jotego/jts16/cores/s16/ver/game/wb35/7.png

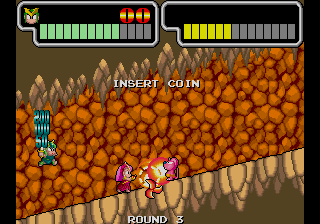
cores/s16/ver/game/wb35/7.png
