jotego/jts16/cores/s16/ver/game/shinobi/1.png

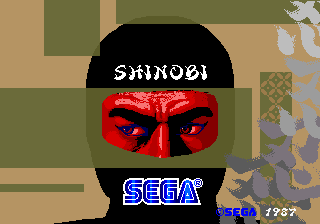
cores/s16/ver/game/shinobi/1.png
