jotego/jts16/cores/s16/ver/game/shinobi/2.png

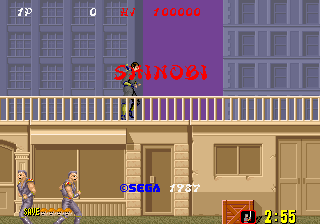
cores/s16/ver/game/shinobi/2.png
