jotego/jts16/cores/s16/ver/game/shinobi/3.png

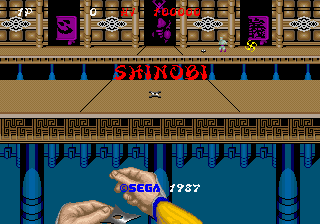
cores/s16/ver/game/shinobi/3.png
