jotego/jts16/cores/s16/ver/game/shinobi/4.png

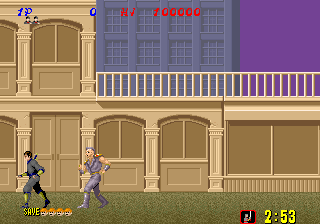
cores/s16/ver/game/shinobi/4.png
