jotego/jts16/cores/s16/ver/game/shinobi/5.png

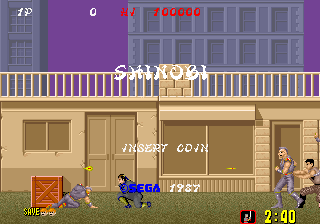
cores/s16/ver/game/shinobi/5.png
