jotego/jts16/cores/s16/ver/game/shinobi/6.png

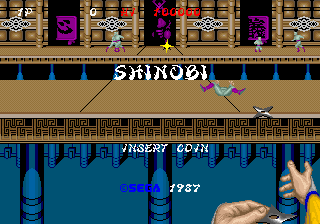
cores/s16/ver/game/shinobi/6.png
