jotego/jts16/cores/s16/ver/game/shinobi/7.png

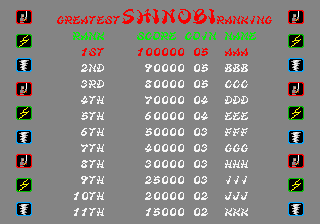
cores/s16/ver/game/shinobi/7.png
