jotego/jts16/cores/s16/ver/game/shinobi/8.png

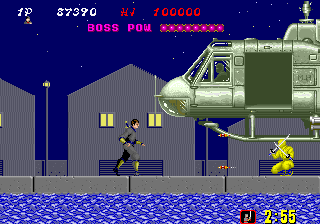
cores/s16/ver/game/shinobi/8.png
