jotego/jts16/cores/s16/ver/game/shinobi/9.png

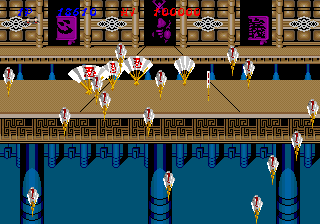
cores/s16/ver/game/shinobi/9.png
