jotego/jts16/cores/s16/ver/game/wb35/2.png

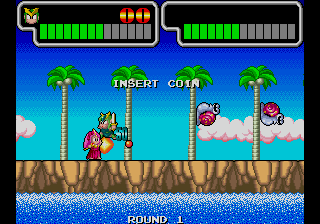
cores/s16/ver/game/wb35/2.png
