jotego/jts16/cores/s16/ver/game/wb35/3.png

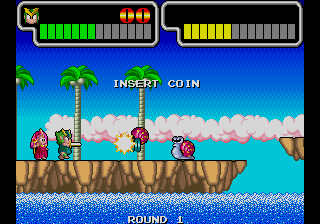
cores/s16/ver/game/wb35/3.png
