jotego/jts16/cores/s16/ver/game/wb35/4.png

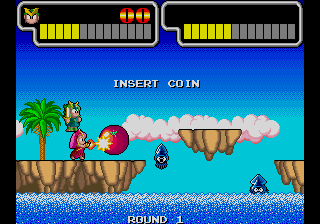
cores/s16/ver/game/wb35/4.png
