jotego/jts16/cores/s16/ver/game/wb35/6.png

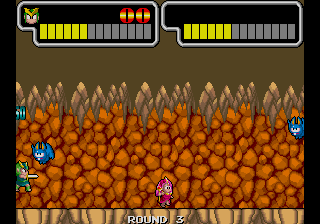
cores/s16/ver/game/wb35/6.png
