jotego/jts16/cores/s16/ver/game/wb35/8.png

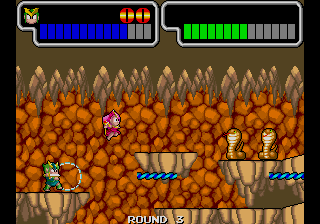
cores/s16/ver/game/wb35/8.png
