jotego/jts16/doc/scope/DTACKn.png

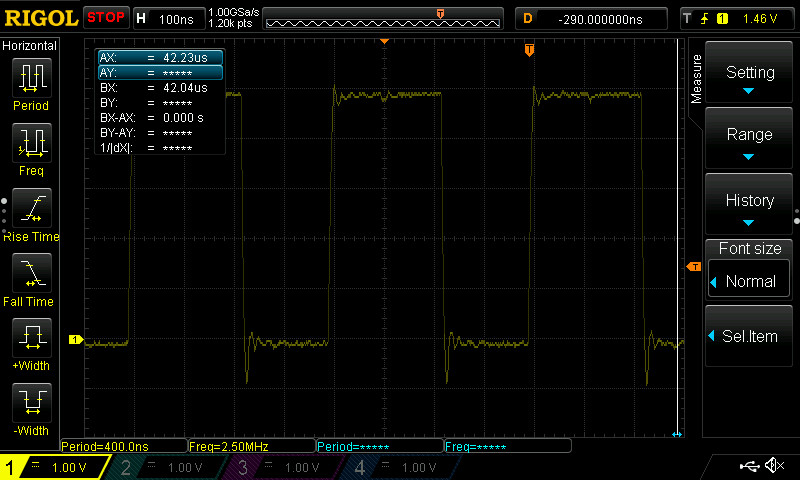
doc/scope/DTACKn.png
