jotego/jts16/doc/scope/IPL2.png

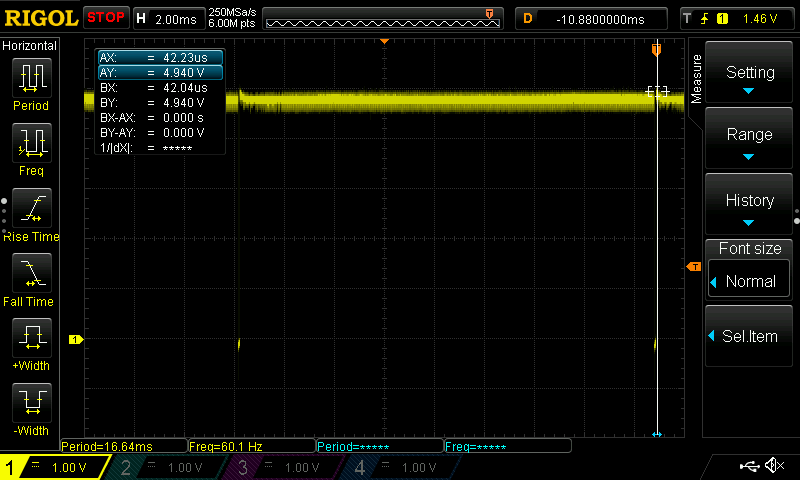
doc/scope/IPL2.png
