jotego/jts16/doc/scope/wb3/wb3.png

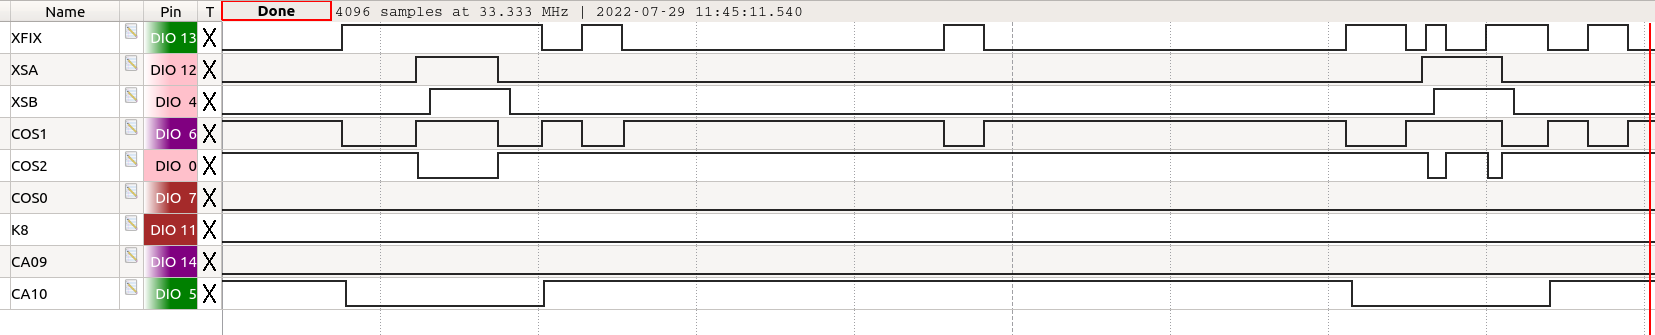
doc/scope/wb3/wb3.png
