jotego/jts16/doc/scope/wb3/WB3_no_OBJ.png

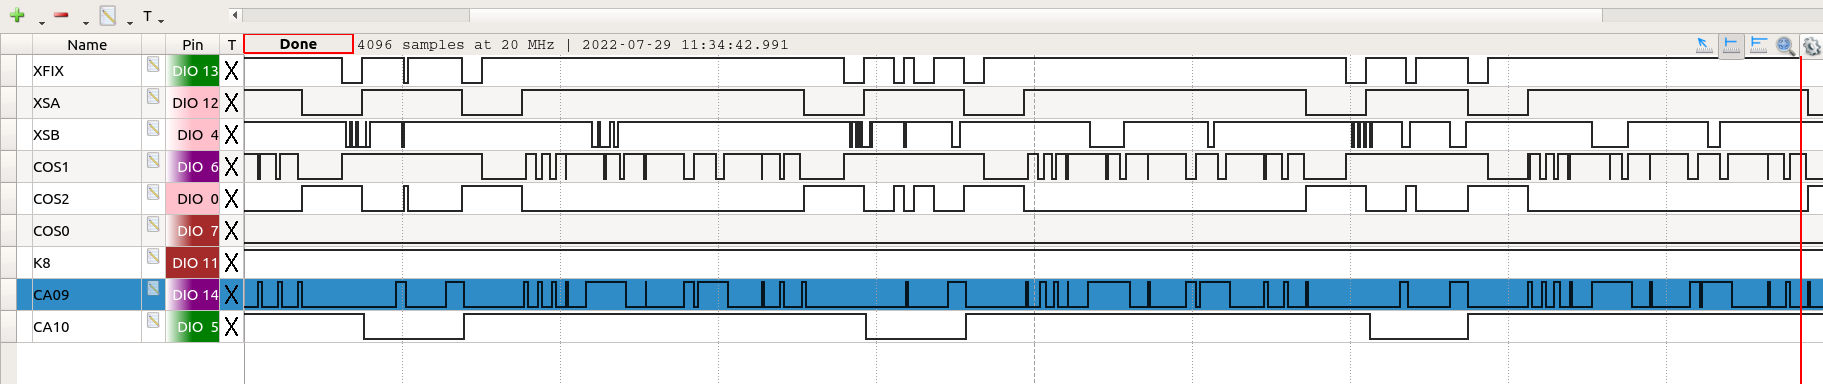
doc/scope/wb3/WB3_no_OBJ.png
