jotego/jts16/doc/scope/wb3/WB3_only_char.png

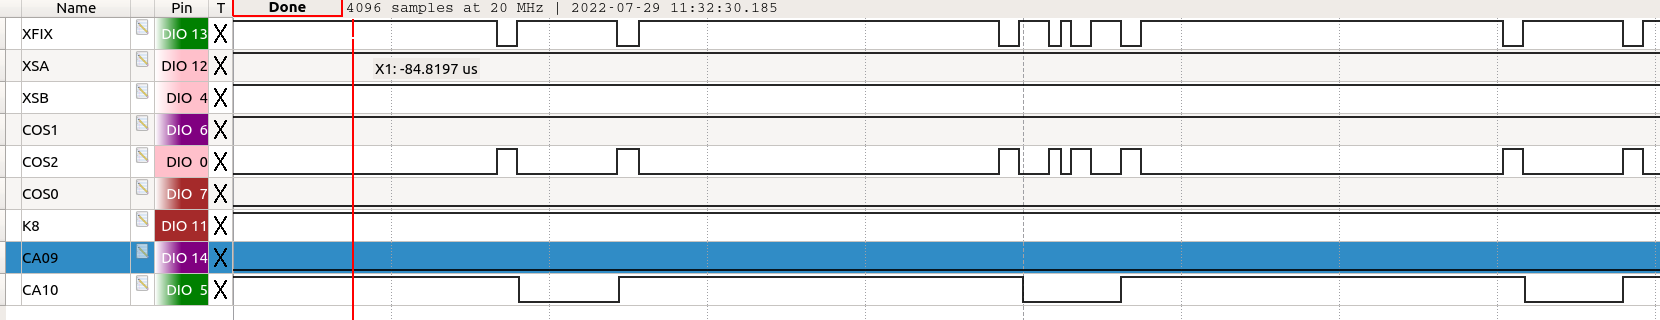
doc/scope/wb3/WB3_only_char.png
