jotego/jts16/doc/scope/Z80 clk.png

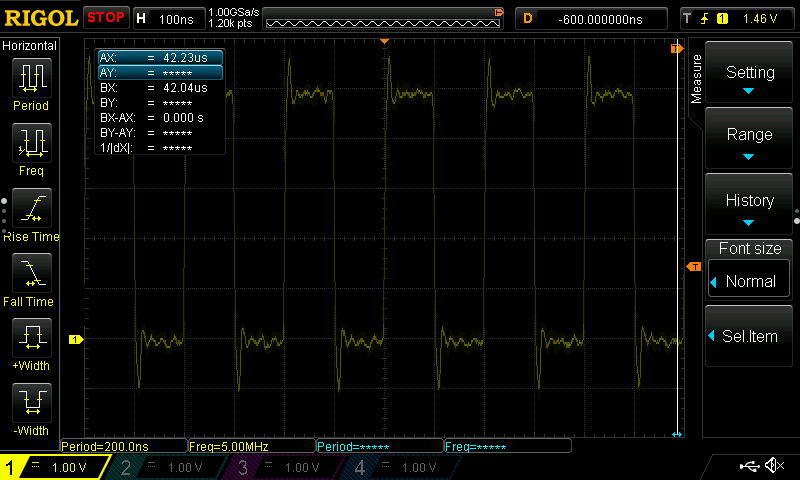
doc/scope/Z80 clk.png
