jotego/jts16/cores/s18/sch/amd.kicad_sch

## KiCad design cores/s18/sch/amd.kicad_sch (2022-12-19)

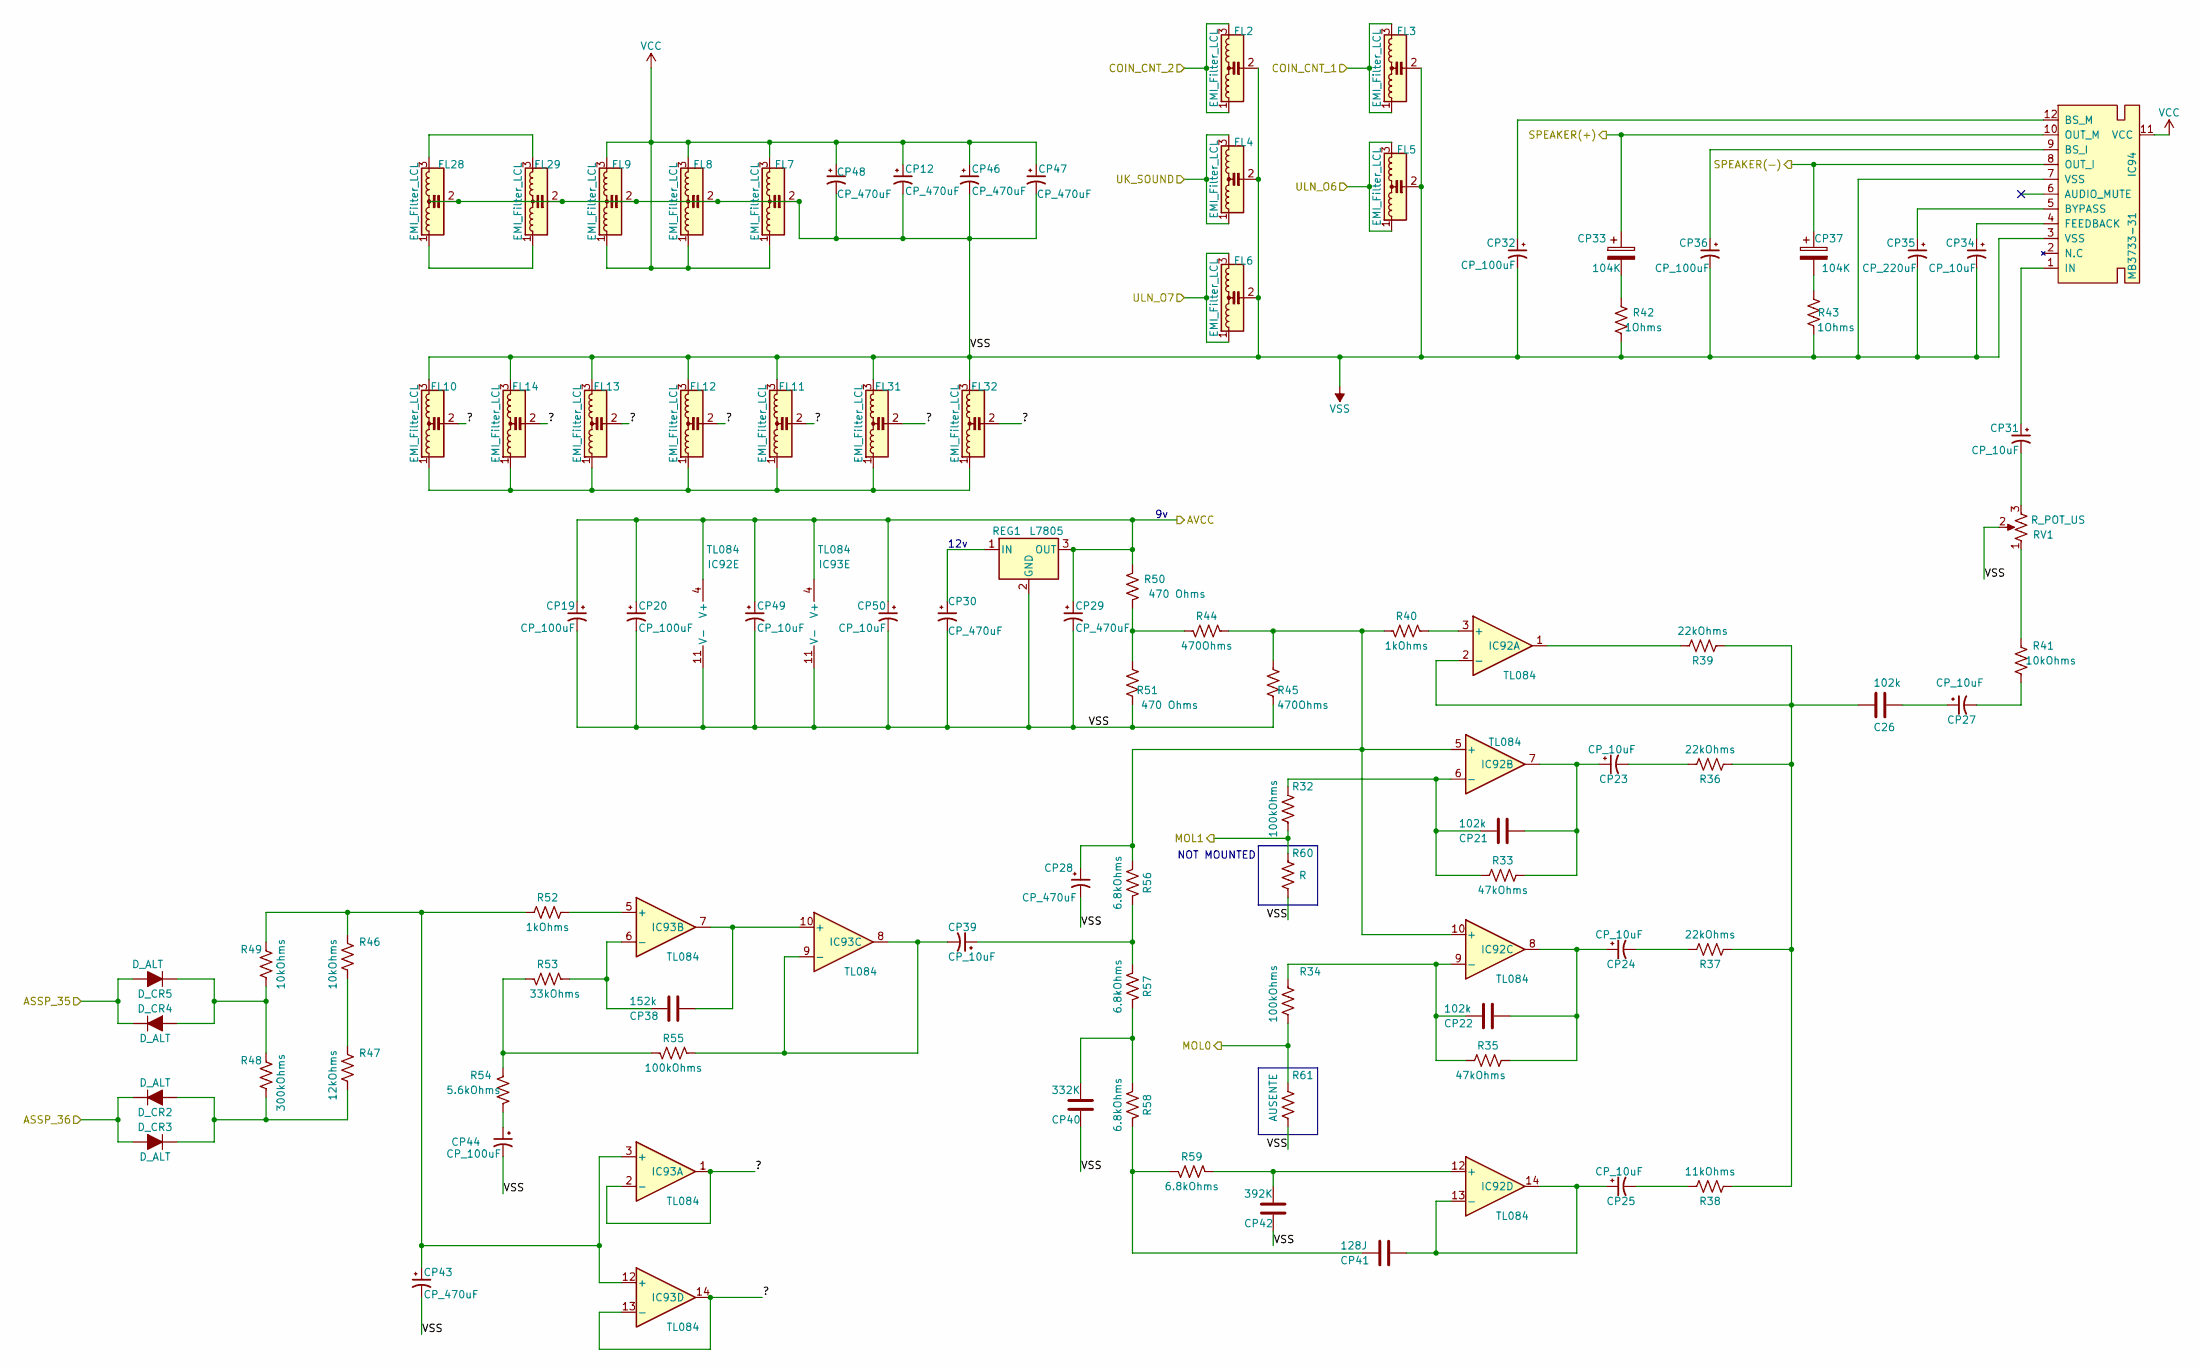
[picture p33: schematic amd.kicad_sch]

Parts:
104K: CP37
C26: 102k
CP12, CP28, CP29, CP30, CP43, CP46, CP47, CP48: CP_470uF
CP19, CP20, CP32, CP36, CP44: CP_100uF
CP21, CP22: 102k
CP23, CP24, CP25, CP27, CP31, CP34, CP39, CP49, CP50: CP_10uF
CP35: CP_220uF
CP38: 152k
CP40: 332K
CP41: 128J
CP42: 392K
D_CR2, D_CR3, D_CR4, D_CR5: D_ALT
FL2, FL3, FL4, FL5, FL6, FL7, FL8, FL9, FL10, FL11, FL12, FL13, FL14, FL28, FL29, FL31, FL32: EMI_Filter_LCL
IC92, IC93: TL084
IC94: MB3733-31
R32, R34, R55: 100kOhms
R33, R35: 47kOhms
R36, R37, R39: 22kOhms
R38: 11kOhms
R40, R52: 1kOhms
R41, R46, R49: 10kOhms
R42, R43: 1Ohms
R44, R45: 470Ohms
R47: 12kOhms
R48: 300kOhms
R50, R51: 470 Ohms
R53: 33kOhms
R54: 5.6kOhms
R56, R57, R58, R59: 6.8kOhms
R60: R
R61: AUSENTE
REG1: L7805
RV1: R_POT_US

Connections:
?: FL10.2, FL11.2, FL12.2, FL13.2, FL14.2, FL31.2, FL32.2, IC93.1, IC93.2 (-), IC93.13 (-), IC93.14
ASSP_35: D_CR4.1 (K), D_CR5.2 (A)
ASSP_36: D_CR2.1 (K), D_CR3.2 (A)
AVCC: CP19.1, CP20.1, CP29.1, CP49.1, CP50.1, IC92.4 (V+), IC93.4 (V+), R50.1, REG1.3 (OUT)
COIN_CNT_1: FL3.1, FL3.3
COIN_CNT_2: FL2.1, FL2.3
MOL0: R34.2, R61.1
MOL1: R32.2, R60.1
unnamed: 104K.2, R42.1, R43.1
unnamed: C26.1, CP27.1
unnamed: C26.2, IC92.2 (-), R36.2, R37.2, R38.2, R39.2
unnamed: CP12.1, CP46.1, CP47.1, CP48.1, FL7.1, FL7.3, FL8.1, FL8.3, FL9.1, FL9.3
unnamed: CP21.1, CP23.1, IC92.7, R33.1
unnamed: CP21.2, IC92.6 (-), R32.1, R33.2
unnamed: CP22.1, CP24.1, IC92.8, R35.1
unnamed: CP22.2, IC92.9 (-), R34.1, R35.2
unnamed: CP23.2, R36.1
unnamed: CP24.2, R37.1
unnamed: CP25.1, CP41.1, IC92.13 (-), IC92.14
unnamed: CP25.2, R38.1
unnamed: CP27.2, R41.1
unnamed: CP28.1, IC92.5 (+), IC92.10 (+), R40.1, R44.1, R45.1, R56.2
unnamed: CP30.1, REG1.1 (IN)
unnamed: CP31.1, IC94.1 (IN)
unnamed: CP31.2, RV1.3
unnamed: CP32.1, IC94.12 (BS_M)
unnamed: CP34.1, IC94.4 (FEEDBACK)
unnamed: CP35.1, IC94.5 (BYPASS)
unnamed: CP36.1, IC94.9 (BS_I)
unnamed: CP38.1, IC93.7, IC93.10 (+)
unnamed: CP38.2, IC93.6 (-), R53.1
unnamed: CP39.1, R56.1, R57.2
unnamed: CP39.2, IC93.8, IC93.9 (-), R55.1
unnamed: CP40.1, R57.1, R58.2
unnamed: CP41.2, R58.1, R59.1
unnamed: CP42.1, IC92.12 (+), R59.2
unnamed: CP43.1, IC93.3 (+), IC93.12 (+), R46.2, R49.1, R52.2
unnamed: CP44.1, R54.2
unnamed: D_CR2.2 (A), D_CR3.1 (K), R47.2, R48.1
unnamed: D_CR4.2 (A), D_CR5.1 (K), R48.2, R49.2
unnamed: FL10.1, FL11.1, FL12.1, FL13.1, FL14.1, FL31.1, FL32.1
unnamed: FL28.1, FL29.1
unnamed: FL28.3, FL29.3
unnamed: IC92.1, R39.1
unnamed: IC92.3 (+), R40.2
unnamed: IC93.5 (+), R52.1
unnamed: R41.2, RV1.1
unnamed: R44.2, R50.2, R51.2
unnamed: R46.1, R47.1
unnamed: R53.2, R54.1, R55.2
SPEAKER(+): 104K.1, IC94.10 (OUT_M)
SPEAKER(-): 104K.1, IC94.8 (OUT_I)
UK_SOUND: FL4.1, FL4.3
ULN_O6: FL5.1, FL5.3
ULN_O7: FL6.1, FL6.3
VSS: CP12.2, CP19.2, CP20.2, CP28.2, CP29.2, CP30.2, CP32.2, CP34.2, CP35.2, CP36.2, CP40.2, CP42.2, CP43.2, CP44.2, CP46.2, CP47.2, CP48.2, CP49.2, CP50.2, FL2.2, FL3.2, FL4.2, FL5.2, FL6.2, FL7.2, FL8.2, FL9.2, FL10.3, FL11.3, FL12.3, FL13.3, FL14.3, FL28.2, FL29.2, FL31.3, FL32.3, IC92.11 (V-), IC93.11 (V-), IC94.3 (VSS), IC94.7 (VSS), R42.2, R43.2, R45.2, R51.1, R60.2, R61.2, REG1.2 (GND), RV1.2

Notes on the sheet:
NOT MOUNTED
12v
