jotego/jts16/cores/s18/sch/blanking.kicad_sch

## KiCad design cores/s18/sch/blanking.kicad_sch (2022-12-19)

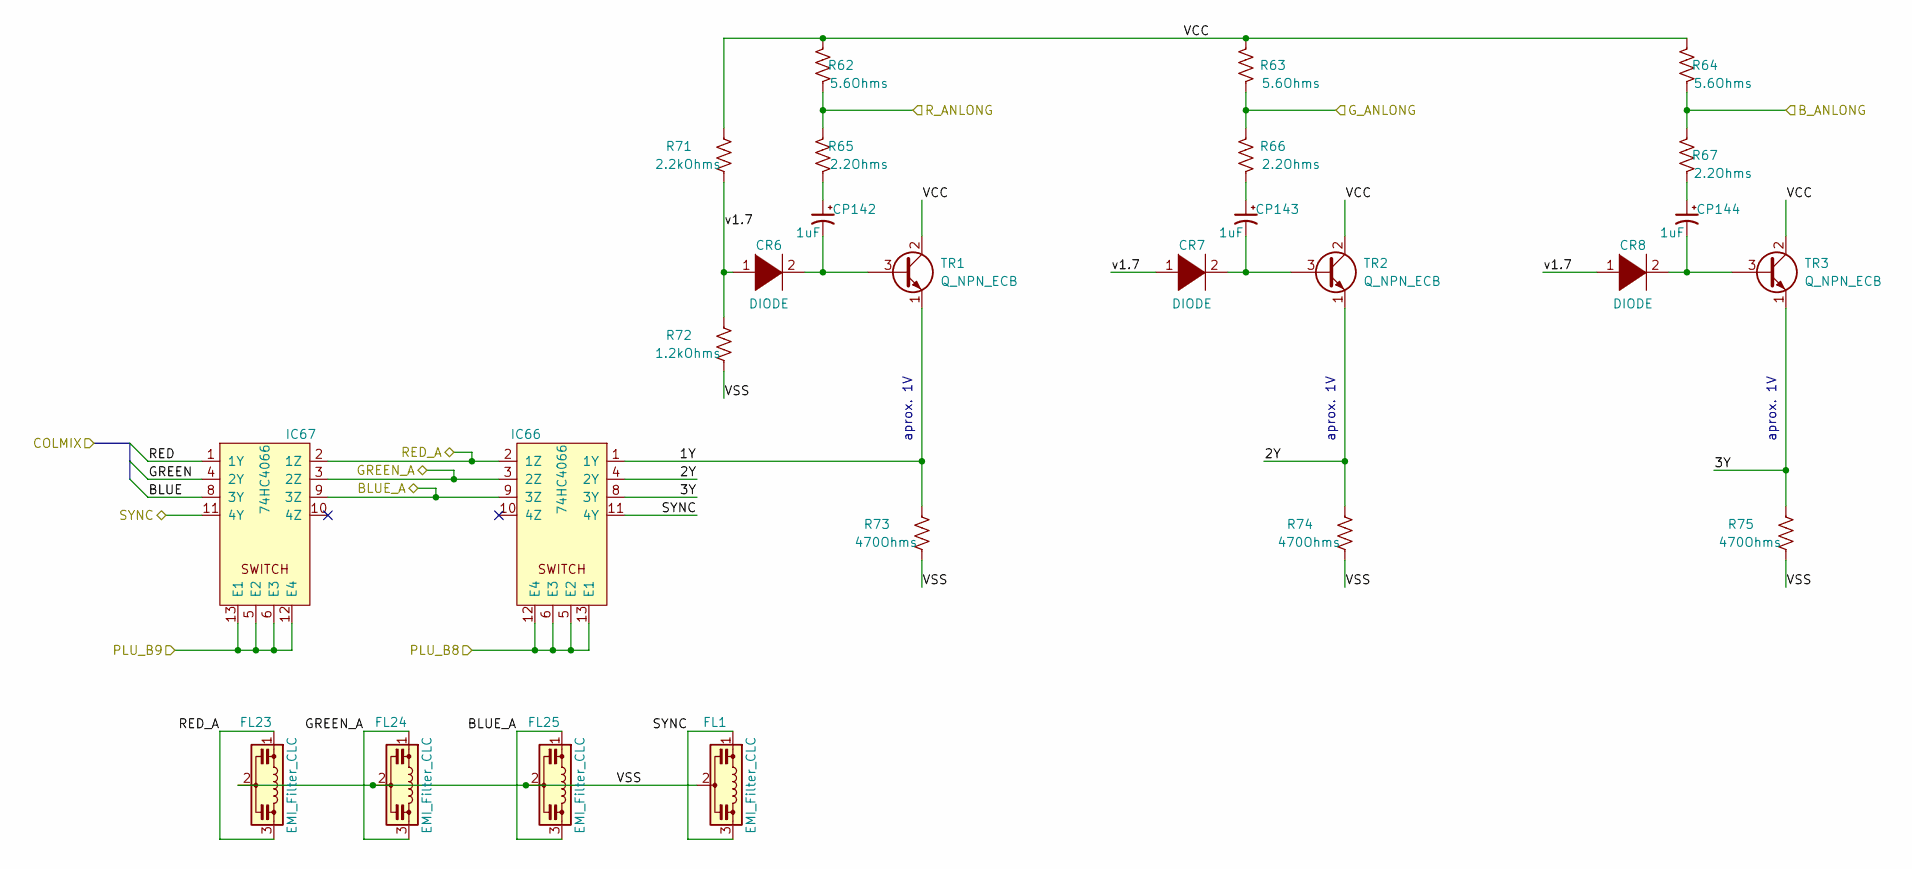
[picture p34: schematic blanking.kicad_sch]

Parts:
CP142, CP143, CP144: 1uF
CR6, CR7, CR8: DIODE
FL1, FL23, FL24, FL25: EMI_Filter_CLC
IC66, IC67: 74HC4066
R62, R63, R64: 5.6Ohms
R65, R66, R67: 2.2Ohms
R71: 2.2kOhms
R72: 1.2kOhms
R73, R74, R75: 470Ohms
TR1, TR2, TR3: Q_NPN_ECB

Connections:
1Y: IC66.1 (1Y), R73.1, TR1.1 (E)
2Y: IC66.4 (2Y), R74.1, TR2.1 (E)
3Y: IC66.8 (3Y), R75.1, TR3.1 (E)
BLUE: IC67.8 (3Y)
BLUE_A: FL25.1, FL25.3, IC66.9 (3Z), IC67.9 (3Z)
B_ANLONG: R64.1, R67.2
GREEN: IC67.4 (2Y)
GREEN_A: FL24.1, FL24.3, IC66.3 (2Z), IC67.3 (2Z)
G_ANLONG: R63.1, R66.2
unnamed: CP142.1, R65.1
unnamed: CP142.2, CR6.2 (A), TR1.3 (B)
unnamed: CP143.1, R66.1
unnamed: CP143.2, CR7.2 (A), TR2.3 (B)
unnamed: CP144.1, R67.1
unnamed: CP144.2, CR8.2 (A), TR3.3 (B)
PLU_B8: IC66.5 (E2), IC66.6 (E3), IC66.12 (E4), IC66.13 (E1)
PLU_B9: IC67.5 (E2), IC67.6 (E3), IC67.12 (E4), IC67.13 (E1)
RED: IC67.1 (1Y)
RED_A: FL23.1, FL23.3, IC66.2 (1Z), IC67.2 (1Z)
R_ANLONG: R62.1, R65.2
SYNC: FL1.1, FL1.3, IC66.11 (4Y), IC67.11 (4Y)
VCC: R62.2, R63.2, R64.2, R71.1, TR1.2 (C), TR2.2 (C), TR3.2 (C)
VSS: FL1.2, FL23.2, FL24.2, FL25.2, R72.2, R73.2, R74.2, R75.2
v1.7: CR6.1 (K), CR7.1 (K), CR8.1 (K), R71.2, R72.1

Notes on the sheet:
aprox. 1V
