jotego/jts16/cores/s18/sch/capacitors.kicad_sch

## KiCad design cores/s18/sch/capacitors.kicad_sch (2022-12-19)

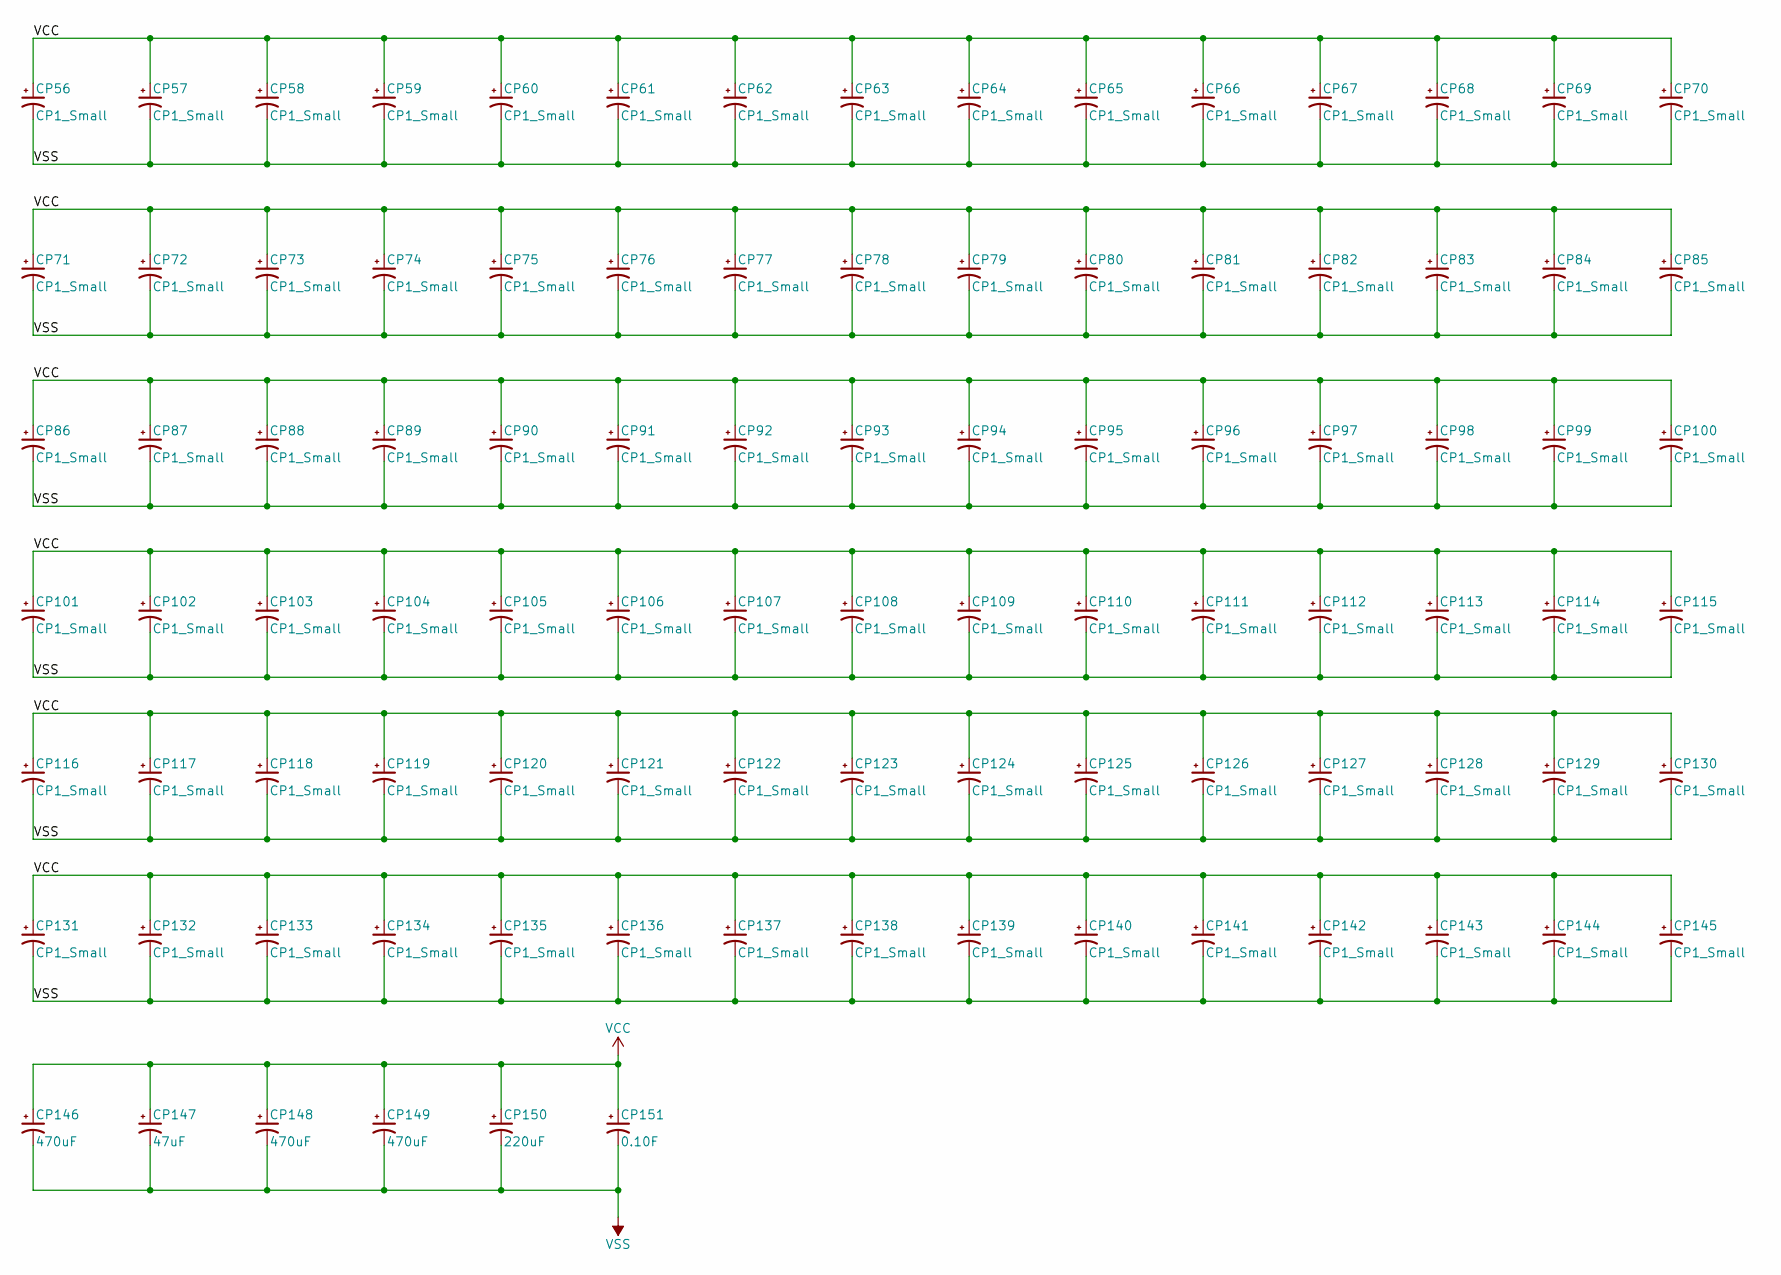
[picture p35: schematic capacitors.kicad_sch]

Parts:
CP56, CP57, CP58, CP59, CP60, CP61, CP62, CP63, CP64, CP65, CP66, CP67, CP68, CP69, CP70, CP71, CP72, CP73, CP74, CP75, CP76, CP77, CP78, CP79, CP80, CP81, CP82, CP83, CP84, CP85, CP86, CP87, CP88, CP89, CP90, CP91, CP92, CP93, CP94, CP95, CP96, CP97, CP98, CP99, CP100, CP101, CP102, CP103, CP104, CP105, CP106, CP107, CP108, CP109, CP110, CP111, CP112, CP113, CP114, CP115, CP116, CP117, CP118, CP119, CP120, CP121, CP122, CP123, CP124, CP125, CP126, CP127, CP128, CP129, CP130, CP131, CP132, CP133, CP134, CP135, CP136, CP137, CP138, CP139, CP140, CP141, CP142, CP143, CP144, CP145: CP1_Small
CP146, CP148, CP149: 470uF
CP147: 47uF
CP150: 220uF
CP151: 0.10F

Connections:
VCC: CP56.1, CP57.1, CP58.1, CP59.1, CP60.1, CP61.1, CP62.1, CP63.1, CP64.1, CP65.1, CP66.1, CP67.1, CP68.1, CP69.1, CP70.1, CP71.1, CP72.1, CP73.1, CP74.1, CP75.1, CP76.1, CP77.1, CP78.1, CP79.1, CP80.1, CP81.1, CP82.1, CP83.1, CP84.1, CP85.1, CP86.1, CP87.1, CP88.1, CP89.1, CP90.1, CP91.1, CP92.1, CP93.1, CP94.1, CP95.1, CP96.1, CP97.1, CP98.1, CP99.1, CP100.1, CP101.1, CP102.1, CP103.1, CP104.1, CP105.1, CP106.1, CP107.1, CP108.1, CP109.1, CP110.1, CP111.1, CP112.1, CP113.1, CP114.1, CP115.1, CP116.1, CP117.1, CP118.1, CP119.1, CP120.1, CP121.1, CP122.1, CP123.1, CP124.1, CP125.1, CP126.1, CP127.1, CP128.1, CP129.1, CP130.1, CP131.1, CP132.1, CP133.1, CP134.1, CP135.1, CP136.1, CP137.1, CP138.1, CP139.1, CP140.1, CP141.1, CP142.1, CP143.1, CP144.1, CP145.1, CP146.1, CP147.1, CP148.1, CP149.1, CP150.1, CP151.1
VSS: CP56.2, CP57.2, CP58.2, CP59.2, CP60.2, CP61.2, CP62.2, CP63.2, CP64.2, CP65.2, CP66.2, CP67.2, CP68.2, CP69.2, CP70.2, CP71.2, CP72.2, CP73.2, CP74.2, CP75.2, CP76.2, CP77.2, CP78.2, CP79.2, CP80.2, CP81.2, CP82.2, CP83.2, CP84.2, CP85.2, CP86.2, CP87.2, CP88.2, CP89.2, CP90.2, CP91.2, CP92.2, CP93.2, CP94.2, CP95.2, CP96.2, CP97.2, CP98.2, CP99.2, CP100.2, CP101.2, CP102.2, CP103.2, CP104.2, CP105.2, CP106.2, CP107.2, CP108.2, CP109.2, CP110.2, CP111.2, CP112.2, CP113.2, CP114.2, CP115.2, CP116.2, CP117.2, CP118.2, CP119.2, CP120.2, CP121.2, CP122.2, CP123.2, CP124.2, CP125.2, CP126.2, CP127.2, CP128.2, CP129.2, CP130.2, CP131.2, CP132.2, CP133.2, CP134.2, CP135.2, CP136.2, CP137.2, CP138.2, CP139.2, CP140.2, CP141.2, CP142.2, CP143.2, CP144.2, CP145.2, CP146.2, CP147.2, CP148.2, CP149.2, CP150.2, CP151.2
