jotego/jts16/cores/s18/sch/colmix.kicad_sch

## KiCad design cores/s18/sch/colmix.kicad_sch (2022-12-19)

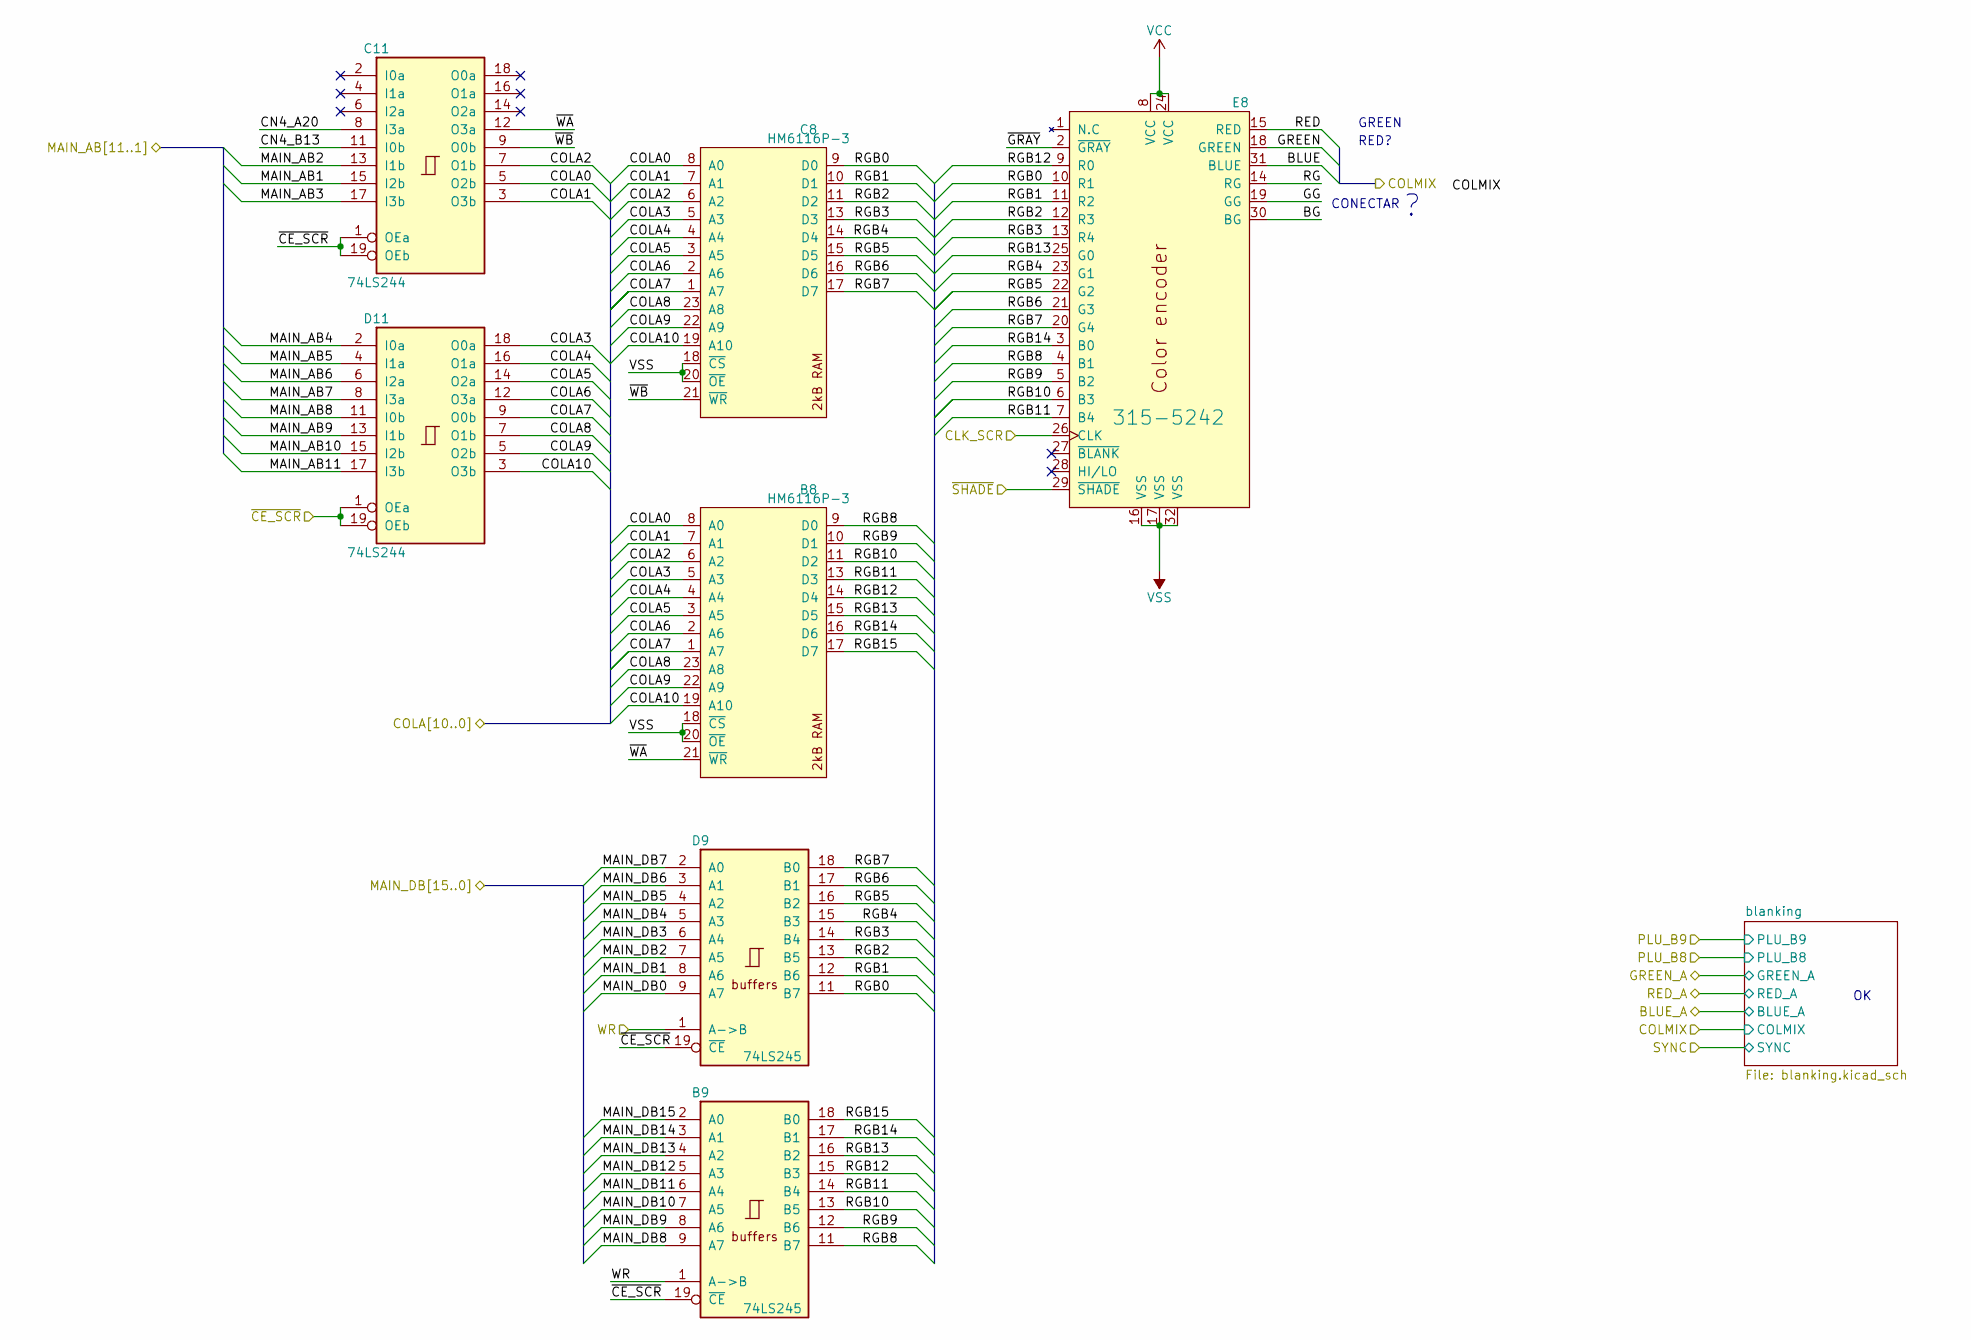
[picture p36: schematic colmix.kicad_sch]

Parts:
B8: HM6116P-3
B9: 74LS245
C8: HM6116P-3
C11: 74LS244
D9: 74LS245
D11: 74LS244
E8: 315-5242

Connections:
BG: E8.30 (BG)
BLUE: E8.31 (BLUE)
CLK_SCR: E8.26 (CLK)
CN4_A20: C11.8 (I3a)
CN4_B13: C11.11 (I0b)
COLA0: B8.8 (A0), C8.8 (A0), C11.5 (O2b)
COLA1: B8.7 (A1), C8.7 (A1), C11.3 (O3b)
COLA2: B8.6 (A2), C8.6 (A2), C11.7 (O1b)
COLA3: B8.5 (A3), C8.5 (A3), D11.18 (O0a)
COLA4: B8.4 (A4), C8.4 (A4), D11.16 (O1a)
COLA5: B8.3 (A5), C8.3 (A5), D11.14 (O2a)
COLA6: B8.2 (A6), C8.2 (A6), D11.12 (O3a)
COLA7: B8.1 (A7), C8.1 (A7), D11.9 (O0b)
COLA8: B8.23 (A8), C8.23 (A8), D11.7 (O1b)
COLA9: B8.22 (A9), C8.22 (A9), D11.5 (O2b)
COLA10: B8.19 (A10), C8.19 (A10), D11.3 (O3b)
GG: E8.19 (GG)
GREEN: E8.18 (GREEN)
MAIN_AB1: C11.15 (I2b)
MAIN_AB2: C11.13 (I1b)
MAIN_AB3: C11.17 (I3b)
MAIN_AB4: D11.2 (I0a)
MAIN_AB5: D11.4 (I1a)
MAIN_AB6: D11.6 (I2a)
MAIN_AB7: D11.8 (I3a)
MAIN_AB8: D11.11 (I0b)
MAIN_AB9: D11.13 (I1b)
MAIN_AB10: D11.15 (I2b)
MAIN_AB11: D11.17 (I3b)
MAIN_DB0: D9.9 (A7)
MAIN_DB1: D9.8 (A6)
MAIN_DB2: D9.7 (A5)
MAIN_DB3: D9.6 (A4)
MAIN_DB4: D9.5 (A3)
MAIN_DB5: D9.4 (A2)
MAIN_DB6: D9.3 (A1)
MAIN_DB7: D9.2 (A0)
MAIN_DB8: B9.9 (A7)
MAIN_DB9: B9.8 (A6)
MAIN_DB10: B9.7 (A5)
MAIN_DB11: B9.6 (A4)
MAIN_DB12: B9.5 (A3)
MAIN_DB13: B9.4 (A2)
MAIN_DB14: B9.3 (A1)
MAIN_DB15: B9.2 (A0)
unnamed: E8.16 (VSS), E8.17 (VSS), E8.32 (VSS)
unnamed: E8.8 (VCC), E8.24 (VCC)
RED: E8.15 (RED)
RG: E8.14 (RG)
RGB0: C8.9 (D0), D9.11 (B7), E8.10 (R1)
RGB1: C8.10 (D1), D9.12 (B6), E8.11 (R2)
RGB2: C8.11 (D2), D9.13 (B5), E8.12 (R3)
RGB3: C8.13 (D3), D9.14 (B4), E8.13 (R4)
RGB4: C8.14 (D4), D9.15 (B3), E8.23 (G1)
RGB5: C8.15 (D5), D9.16 (B2), E8.22 (G2)
RGB6: C8.16 (D6), D9.17 (B1), E8.21 (G3)
RGB7: C8.17 (D7), D9.18 (B0), E8.20 (G4)
RGB8: B8.9 (D0), B9.11 (B7), E8.4 (B1)
RGB9: B8.10 (D1), B9.12 (B6), E8.5 (B2)
RGB10: B8.11 (D2), B9.13 (B5), E8.6 (B3)
RGB11: B8.13 (D3), B9.14 (B4), E8.7 (B4)
RGB12: B8.14 (D4), B9.15 (B3), E8.9 (R0)
RGB13: B8.15 (D5), B9.16 (B2), E8.25 (G0)
RGB14: B8.16 (D6), B9.17 (B1), E8.3 (B0)
RGB15: B8.17 (D7), B9.18 (B0)
VSS: B8.18 (~CS), B8.20 (~OE), C8.18 (~CS), C8.20 (~OE)
WR: B9.1 (A->B), D9.1 (A->B)
~CE_SCR: B9.19 (~CE), C11.1 (OEa), C11.19 (OEb), D9.19 (~CE), D11.1 (OEa), D11.19 (OEb)
~GRAY: E8.2 (~GRAY)
~SHADE: E8.29 (~SHADE)
~WA: B8.21 (~WR), C11.12 (O3a)
~WB: C8.21 (~WR), C11.9 (O0b)

Notes on the sheet:
GREEN
RED?
CONECTAR
