jotego/jts16/cores/s18/sch/cpurom.kicad_sch

## KiCad design cores/s18/sch/cpurom.kicad_sch (2022-12-19)

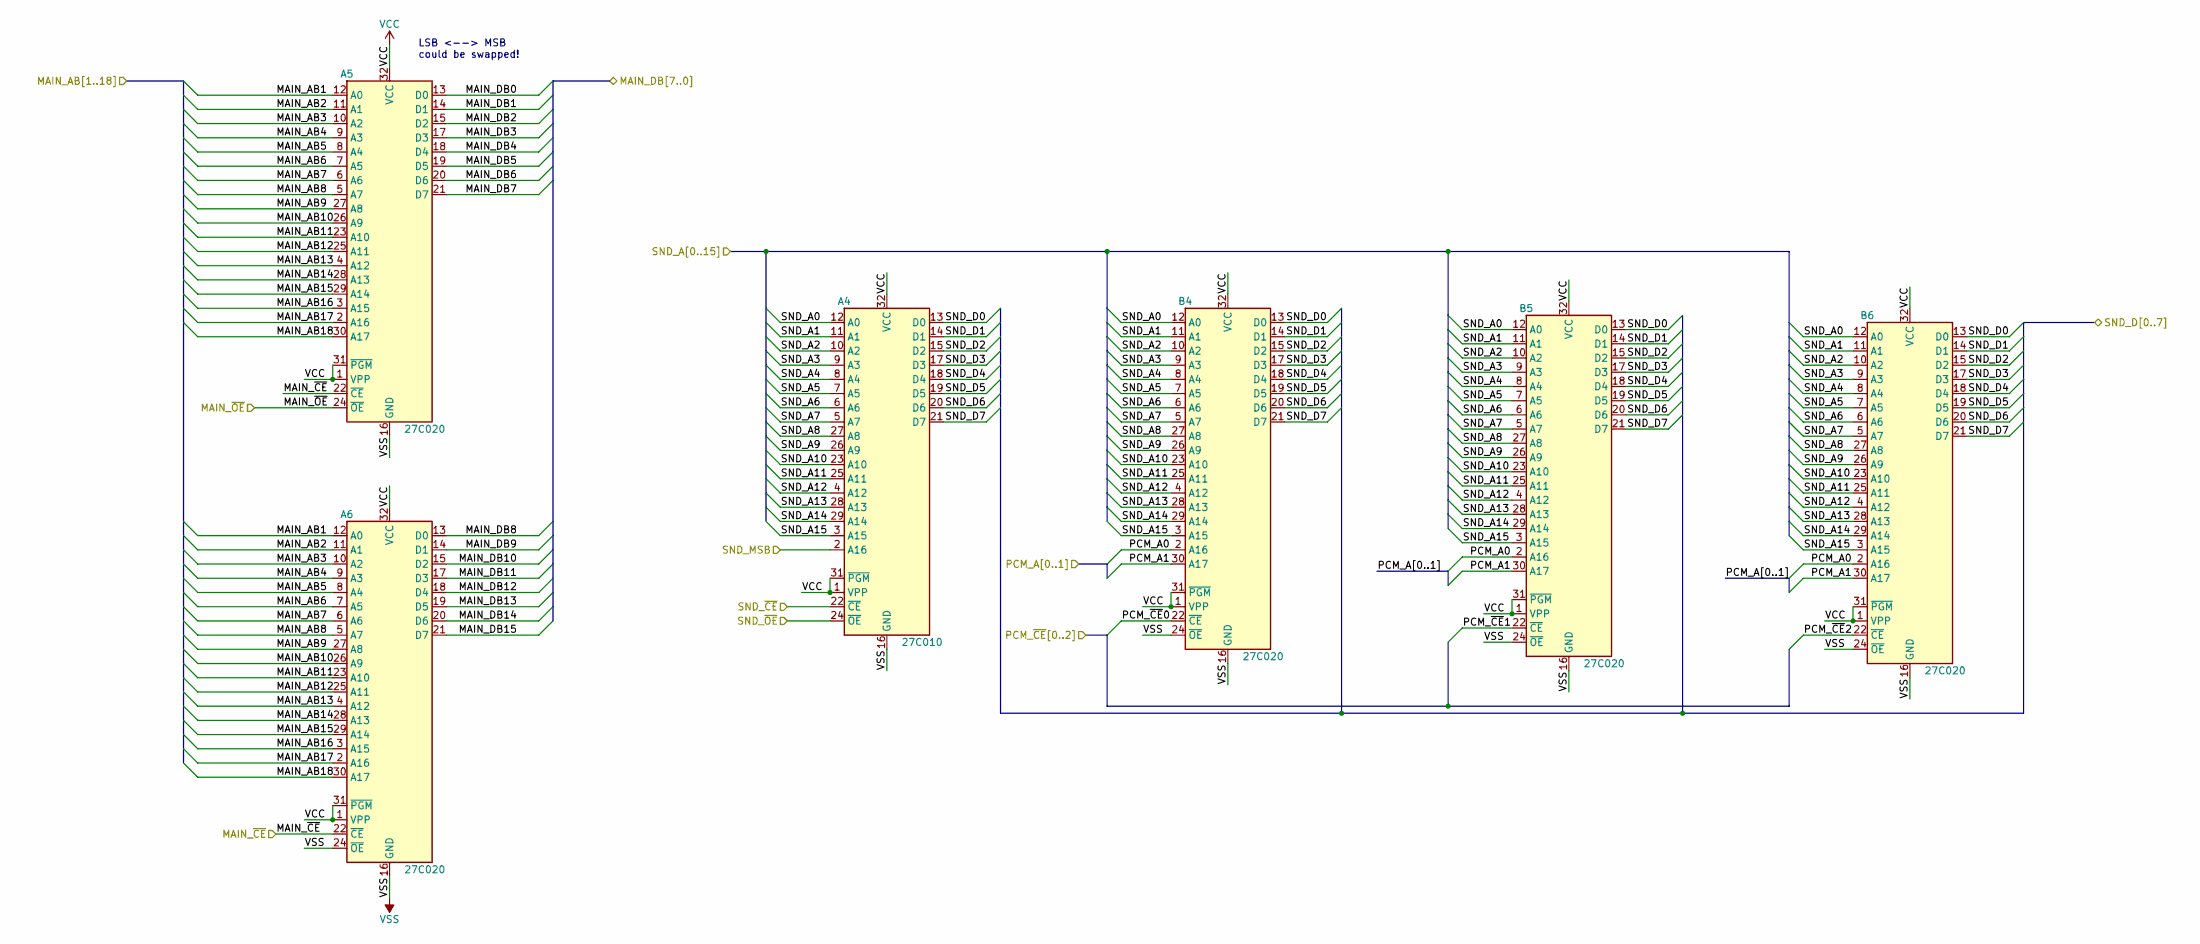
[picture p37: schematic cpurom.kicad_sch]

Parts:
A4: 27C010
A5, A6: 27C020
B4, B5, B6: 27C020

Connections:
MAIN_AB1: A5.12 (A0), A6.12 (A0)
MAIN_AB2: A5.11 (A1), A6.11 (A1)
MAIN_AB3: A5.10 (A2), A6.10 (A2)
MAIN_AB4: A5.9 (A3), A6.9 (A3)
MAIN_AB5: A5.8 (A4), A6.8 (A4)
MAIN_AB6: A5.7 (A5), A6.7 (A5)
MAIN_AB7: A5.6 (A6), A6.6 (A6)
MAIN_AB8: A5.5 (A7), A6.5 (A7)
MAIN_AB9: A5.27 (A8), A6.27 (A8)
MAIN_AB10: A5.26 (A9), A6.26 (A9)
MAIN_AB11: A5.23 (A10), A6.23 (A10)
MAIN_AB12: A5.25 (A11), A6.25 (A11)
MAIN_AB13: A5.4 (A12), A6.4 (A12)
MAIN_AB14: A5.28 (A13), A6.28 (A13)
MAIN_AB15: A5.29 (A14), A6.29 (A14)
MAIN_AB16: A5.3 (A15), A6.3 (A15)
MAIN_AB17: A5.2 (A16), A6.2 (A16)
MAIN_AB18: A5.30 (A17), A6.30 (A17)
MAIN_DB0: A5.13 (D0)
MAIN_DB1: A5.14 (D1)
MAIN_DB2: A5.15 (D2)
MAIN_DB3: A5.17 (D3)
MAIN_DB4: A5.18 (D4)
MAIN_DB5: A5.19 (D5)
MAIN_DB6: A5.20 (D6)
MAIN_DB7: A5.21 (D7)
MAIN_DB8: A6.13 (D0)
MAIN_DB9: A6.14 (D1)
MAIN_DB10: A6.15 (D2)
MAIN_DB11: A6.17 (D3)
MAIN_DB12: A6.18 (D4)
MAIN_DB13: A6.19 (D5)
MAIN_DB14: A6.20 (D6)
MAIN_DB15: A6.21 (D7)
MAIN_~CE: A5.22 (~CE), A6.22 (~CE)
MAIN_~OE: A5.24 (~OE)
PCM_A0: B4.2 (A16), B5.2 (A16), B6.2 (A16)
PCM_A1: B4.30 (A17), B5.30 (A17), B6.30 (A17)
PCM_~CE0: B4.22 (~CE)
PCM_~CE1: B5.22 (~CE)
PCM_~CE2: B6.22 (~CE)
SND_A0: A4.12 (A0), B4.12 (A0), B5.12 (A0), B6.12 (A0)
SND_A1: A4.11 (A1), B4.11 (A1), B5.11 (A1), B6.11 (A1)
SND_A2: A4.10 (A2), B4.10 (A2), B5.10 (A2), B6.10 (A2)
SND_A3: A4.9 (A3), B4.9 (A3), B5.9 (A3), B6.9 (A3)
SND_A4: A4.8 (A4), B4.8 (A4), B5.8 (A4), B6.8 (A4)
SND_A5: A4.7 (A5), B4.7 (A5), B5.7 (A5), B6.7 (A5)
SND_A6: A4.6 (A6), B4.6 (A6), B5.6 (A6), B6.6 (A6)
SND_A7: A4.5 (A7), B4.5 (A7), B5.5 (A7), B6.5 (A7)
SND_A8: A4.27 (A8), B4.27 (A8), B5.27 (A8), B6.27 (A8)
SND_A9: A4.26 (A9), B4.26 (A9), B5.26 (A9), B6.26 (A9)
SND_A10: A4.23 (A10), B4.23 (A10), B5.23 (A10), B6.23 (A10)
SND_A11: A4.25 (A11), B4.25 (A11), B5.25 (A11), B6.25 (A11)
SND_A12: A4.4 (A12), B4.4 (A12), B5.4 (A12), B6.4 (A12)
SND_A13: A4.28 (A13), B4.28 (A13), B5.28 (A13), B6.28 (A13)
SND_A14: A4.29 (A14), B4.29 (A14), B5.29 (A14), B6.29 (A14)
SND_A15: A4.3 (A15), B4.3 (A15), B5.3 (A15), B6.3 (A15)
SND_D0: A4.13 (D0), B4.13 (D0), B5.13 (D0), B6.13 (D0)
SND_D1: A4.14 (D1), B4.14 (D1), B5.14 (D1), B6.14 (D1)
SND_D2: A4.15 (D2), B4.15 (D2), B5.15 (D2), B6.15 (D2)
SND_D3: A4.17 (D3), B4.17 (D3), B5.17 (D3), B6.17 (D3)
SND_D4: A4.18 (D4), B4.18 (D4), B5.18 (D4), B6.18 (D4)
SND_D5: A4.19 (D5), B4.19 (D5), B5.19 (D5), B6.19 (D5)
SND_D6: A4.20 (D6), B4.20 (D6), B5.20 (D6), B6.20 (D6)
SND_D7: A4.21 (D7), B4.21 (D7), B5.21 (D7), B6.21 (D7)
SND_MSB: A4.2 (A16)
SND_~CE: A4.22 (~CE)
SND_~OE: A4.24 (~OE)
VCC: A4.1 (VPP), A4.31 (~PGM), A4.32 (VCC), A5.1 (VPP), A5.31 (~PGM), A5.32 (VCC), A6.1 (VPP), A6.31 (~PGM), A6.32 (VCC), B4.1 (VPP), B4.31 (~PGM), B4.32 (VCC), B5.1 (VPP), B5.31 (~PGM), B5.32 (VCC), B6.1 (VPP), B6.31 (~PGM), B6.32 (VCC)
VSS: A4.16 (GND), A5.16 (GND), A6.16 (GND), A6.24 (~OE), B4.16 (GND), B4.24 (~OE), B5.16 (GND), B5.24 (~OE), B6.16 (GND), B6.24 (~OE)

Notes on the sheet:
LSB <--> MSB could be swapped!
