jotego/jts16/cores/s18/sch/gfx_main.kicad_sch

## KiCad design cores/s18/sch/gfx_main.kicad_sch (2022-12-19)

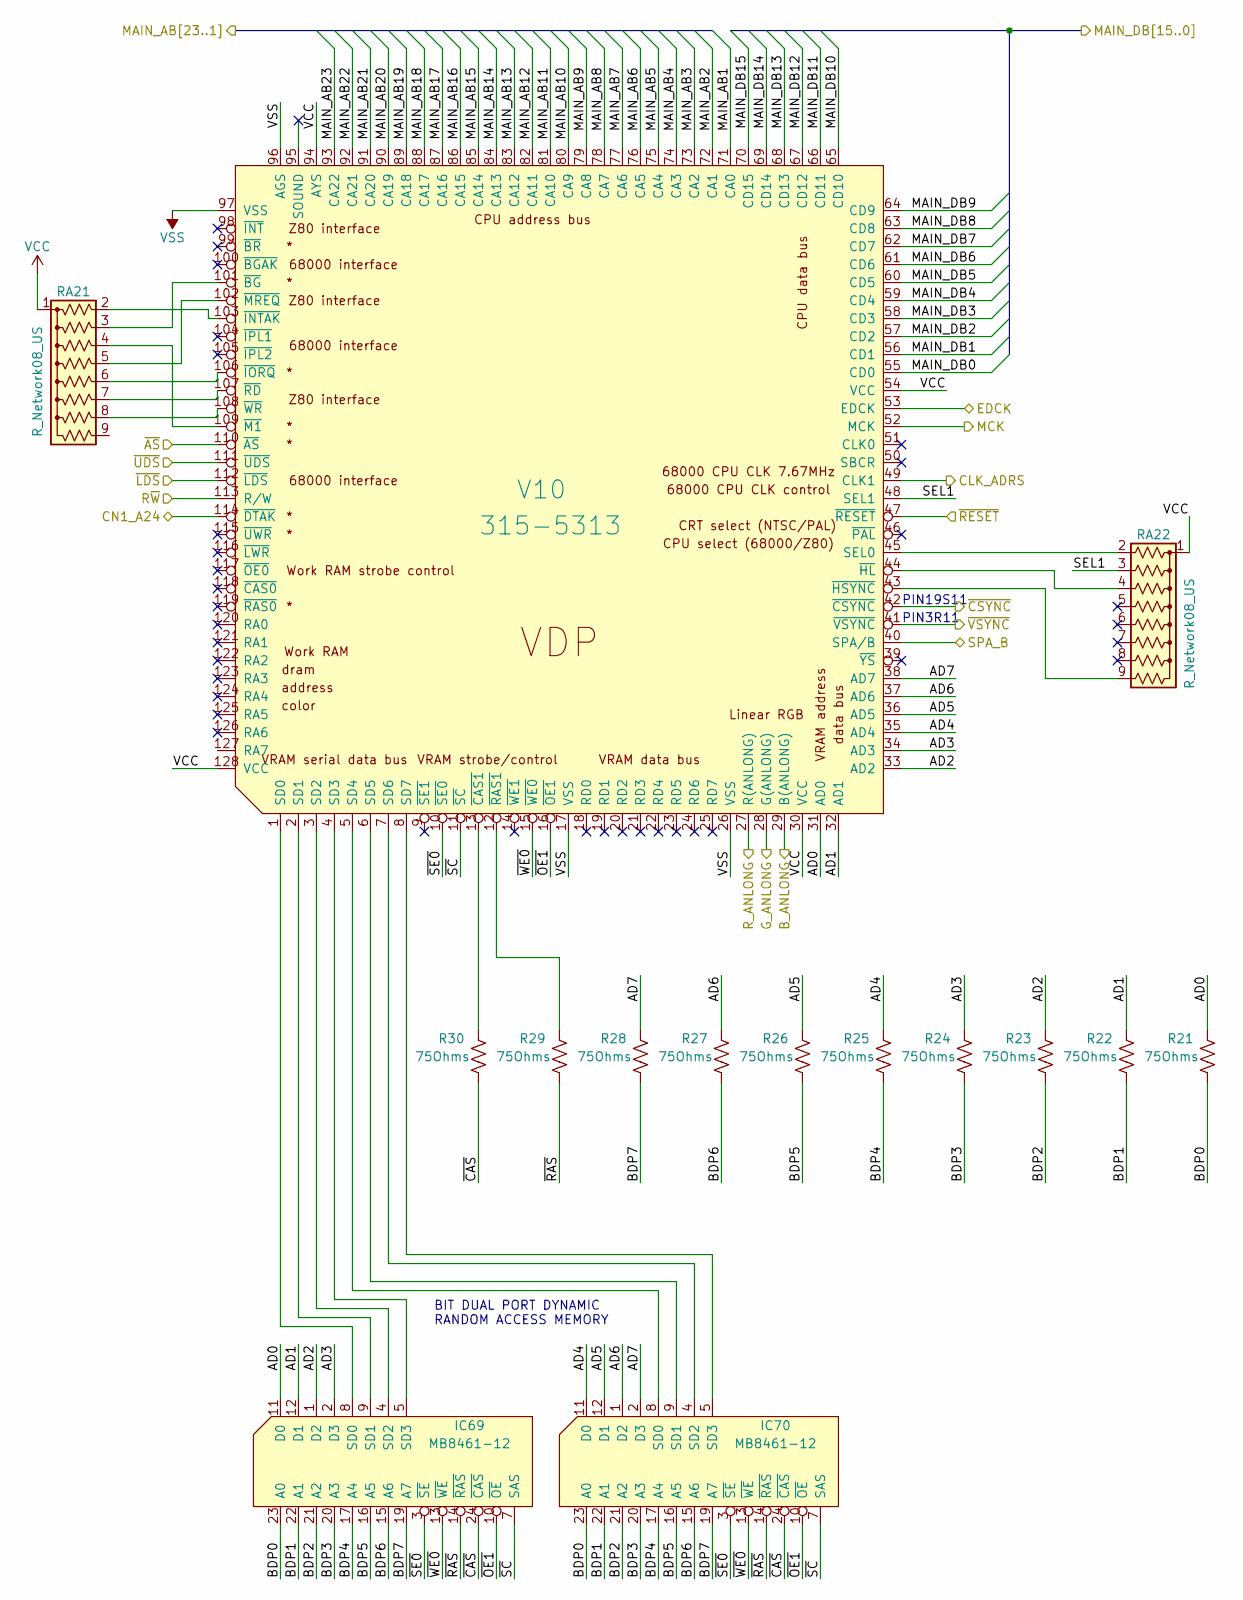
[picture p38: schematic gfx_main.kicad_sch]

Parts:
75Ohms: R30
IC69, IC70: MB8461-12
RA21, RA22: R_Network08_US; R_Array_SIP9
V10: 315-5313

Connections:
AD0: 75Ohms.1, IC69.11 (D0), V10.31 (AD0)
AD1: 75Ohms.1, IC69.12 (D1), V10.32 (AD1)
AD2: 75Ohms.1, IC69.1 (D2), V10.33 (AD2)
AD3: 75Ohms.1, IC69.2 (D3), V10.34 (AD3)
AD4: 75Ohms.1, IC70.11 (D0), V10.35 (AD4)
AD5: 75Ohms.1, IC70.12 (D1), V10.36 (AD5)
AD6: 75Ohms.1, IC70.1 (D2), V10.37 (AD6)
AD7: 75Ohms.1, IC70.2 (D3), V10.38 (AD7)
BDP0: 75Ohms.2, IC69.23 (A0), IC70.23 (A0)
BDP1: 75Ohms.2, IC69.22 (A1), IC70.22 (A1)
BDP2: 75Ohms.2, IC69.21 (A2), IC70.21 (A2)
BDP3: 75Ohms.2, IC69.20 (A3), IC70.20 (A3)
BDP4: 75Ohms.2, IC69.17 (A4), IC70.17 (A4)
BDP5: 75Ohms.2, IC69.16 (A5), IC70.16 (A5)
BDP6: 75Ohms.2, IC69.15 (A6), IC70.15 (A6)
BDP7: 75Ohms.2, IC69.19 (A7), IC70.19 (A7)
B_ANLONG: V10.29 (B(ANLONG))
CLK_ADRS: V10.49 (CLK1)
CN1_A24: V10.114 (~DTAK)
EDCK: V10.53 (EDCK)
G_ANLONG: V10.28 (G(ANLONG))
MAIN_AB1: V10.71 (CA0)
MAIN_AB2: V10.72 (CA1)
MAIN_AB3: V10.73 (CA2)
MAIN_AB4: V10.74 (CA3)
MAIN_AB5: V10.75 (CA4)
MAIN_AB6: V10.76 (CA5)
MAIN_AB7: V10.77 (CA6)
MAIN_AB8: V10.78 (CA7)
MAIN_AB9: V10.79 (CA8)
MAIN_AB10: V10.80 (CA9)
MAIN_AB11: V10.81 (CA10)
MAIN_AB12: V10.82 (CA11)
MAIN_AB13: V10.83 (CA12)
MAIN_AB14: V10.84 (CA13)
MAIN_AB15: V10.85 (CA14)
MAIN_AB16: V10.86 (CA15)
MAIN_AB17: V10.87 (CA16)
MAIN_AB18: V10.88 (CA17)
MAIN_AB19: V10.89 (CA18)
MAIN_AB20: V10.90 (CA19)
MAIN_AB21: V10.91 (CA20)
MAIN_AB22: V10.92 (CA21)
MAIN_AB23: V10.93 (CA22)
MAIN_DB0: V10.55 (CD0)
MAIN_DB1: V10.56 (CD1)
MAIN_DB2: V10.57 (CD2)
MAIN_DB3: V10.58 (CD3)
MAIN_DB4: V10.59 (CD4)
MAIN_DB5: V10.60 (CD5)
MAIN_DB6: V10.61 (CD6)
MAIN_DB7: V10.62 (CD7)
MAIN_DB8: V10.63 (CD8)
MAIN_DB9: V10.64 (CD9)
MAIN_DB10: V10.65 (CD10)
MAIN_DB11: V10.66 (CD11)
MAIN_DB12: V10.67 (CD12)
MAIN_DB13: V10.68 (CD13)
MAIN_DB14: V10.69 (CD14)
MAIN_DB15: V10.70 (CD15)
MCK: V10.52 (MCK)
unnamed: 75Ohms.1, V10.12 (~RAS1), V10.13 (~CAS1)
unnamed: IC69.4 (SD2), V10.3 (SD2)
unnamed: IC69.5 (SD3), V10.4 (SD3)
unnamed: IC69.8 (SD0), V10.1 (SD0)
unnamed: IC69.9 (SD1), V10.2 (SD1)
unnamed: IC70.4 (SD2), V10.7 (SD6)
unnamed: IC70.5 (SD3), V10.8 (SD7)
unnamed: IC70.8 (SD0), V10.5 (SD4)
unnamed: IC70.9 (SD1), V10.6 (SD5)
unnamed: RA21.2 (R1), V10.103 (~INTAK)
unnamed: RA21.3 (R2), V10.101 (~BG)
unnamed: RA21.4 (R3), V10.109 (~M1)
unnamed: RA21.5 (R4), V10.102 (~MREQ)
unnamed: RA21.6 (R5), V10.106 (~IORQ)
unnamed: RA21.7 (R6), V10.107 (~RD)
unnamed: RA21.8 (R7), V10.108 (~WR)
unnamed: RA22.2 (R1), V10.45 (SEL0)
unnamed: RA22.4 (R3), V10.44 (~HL)
unnamed: RA22.9 (R8), V10.43 (~HSYNC)
R_ANLONG: V10.27 (R(ANLONG))
R~W: V10.113 (R/W)
SEL1: RA22.3 (R2), V10.48 (SEL1)
SPA_B: V10.40 (SPA/B)
VCC: RA22.1 (common), V10.30 (VCC), V10.54 (VCC), V10.94 (AYS), V10.128 (VCC)
VSS: V10.17 (VSS), V10.26 (VSS), V10.96 (AGS)
~AS: V10.110 (~AS)
~CAS: 75Ohms.2, IC69.24 (~CAS), IC70.24 (~CAS)
~CSYNC: V10.42 (~CSYNC)
~LDS: V10.112 (~LDS)
~OE1: IC69.10 (~OE), IC70.10 (~OE), V10.16 (~OE1)
~RAS: 75Ohms.2, IC69.14 (~RAS), IC70.14 (~RAS)
~RESET: V10.47 (~RESET)
~SC: IC69.7 (SAS), IC70.7 (SAS), V10.11 (~SC)
~SE0: IC69.3 (~SE), IC70.3 (~SE), V10.10 (~SE0)
~UDS: V10.111 (~UDS)
~VSYNC: V10.41 (~VSYNC)
~WE0: IC69.13 (~WE), IC70.13 (~WE), V10.15 (~WE0)

Notes on the sheet:
PIN19S11
PIN3R11
BIT DUAL PORT DYNAMIC RANDOM ACCESS MEMORY
