jotego/jts16/cores/s18/sch/gfx_obj.kicad_sch

## KiCad design cores/s18/sch/gfx_obj.kicad_sch (2022-12-19)

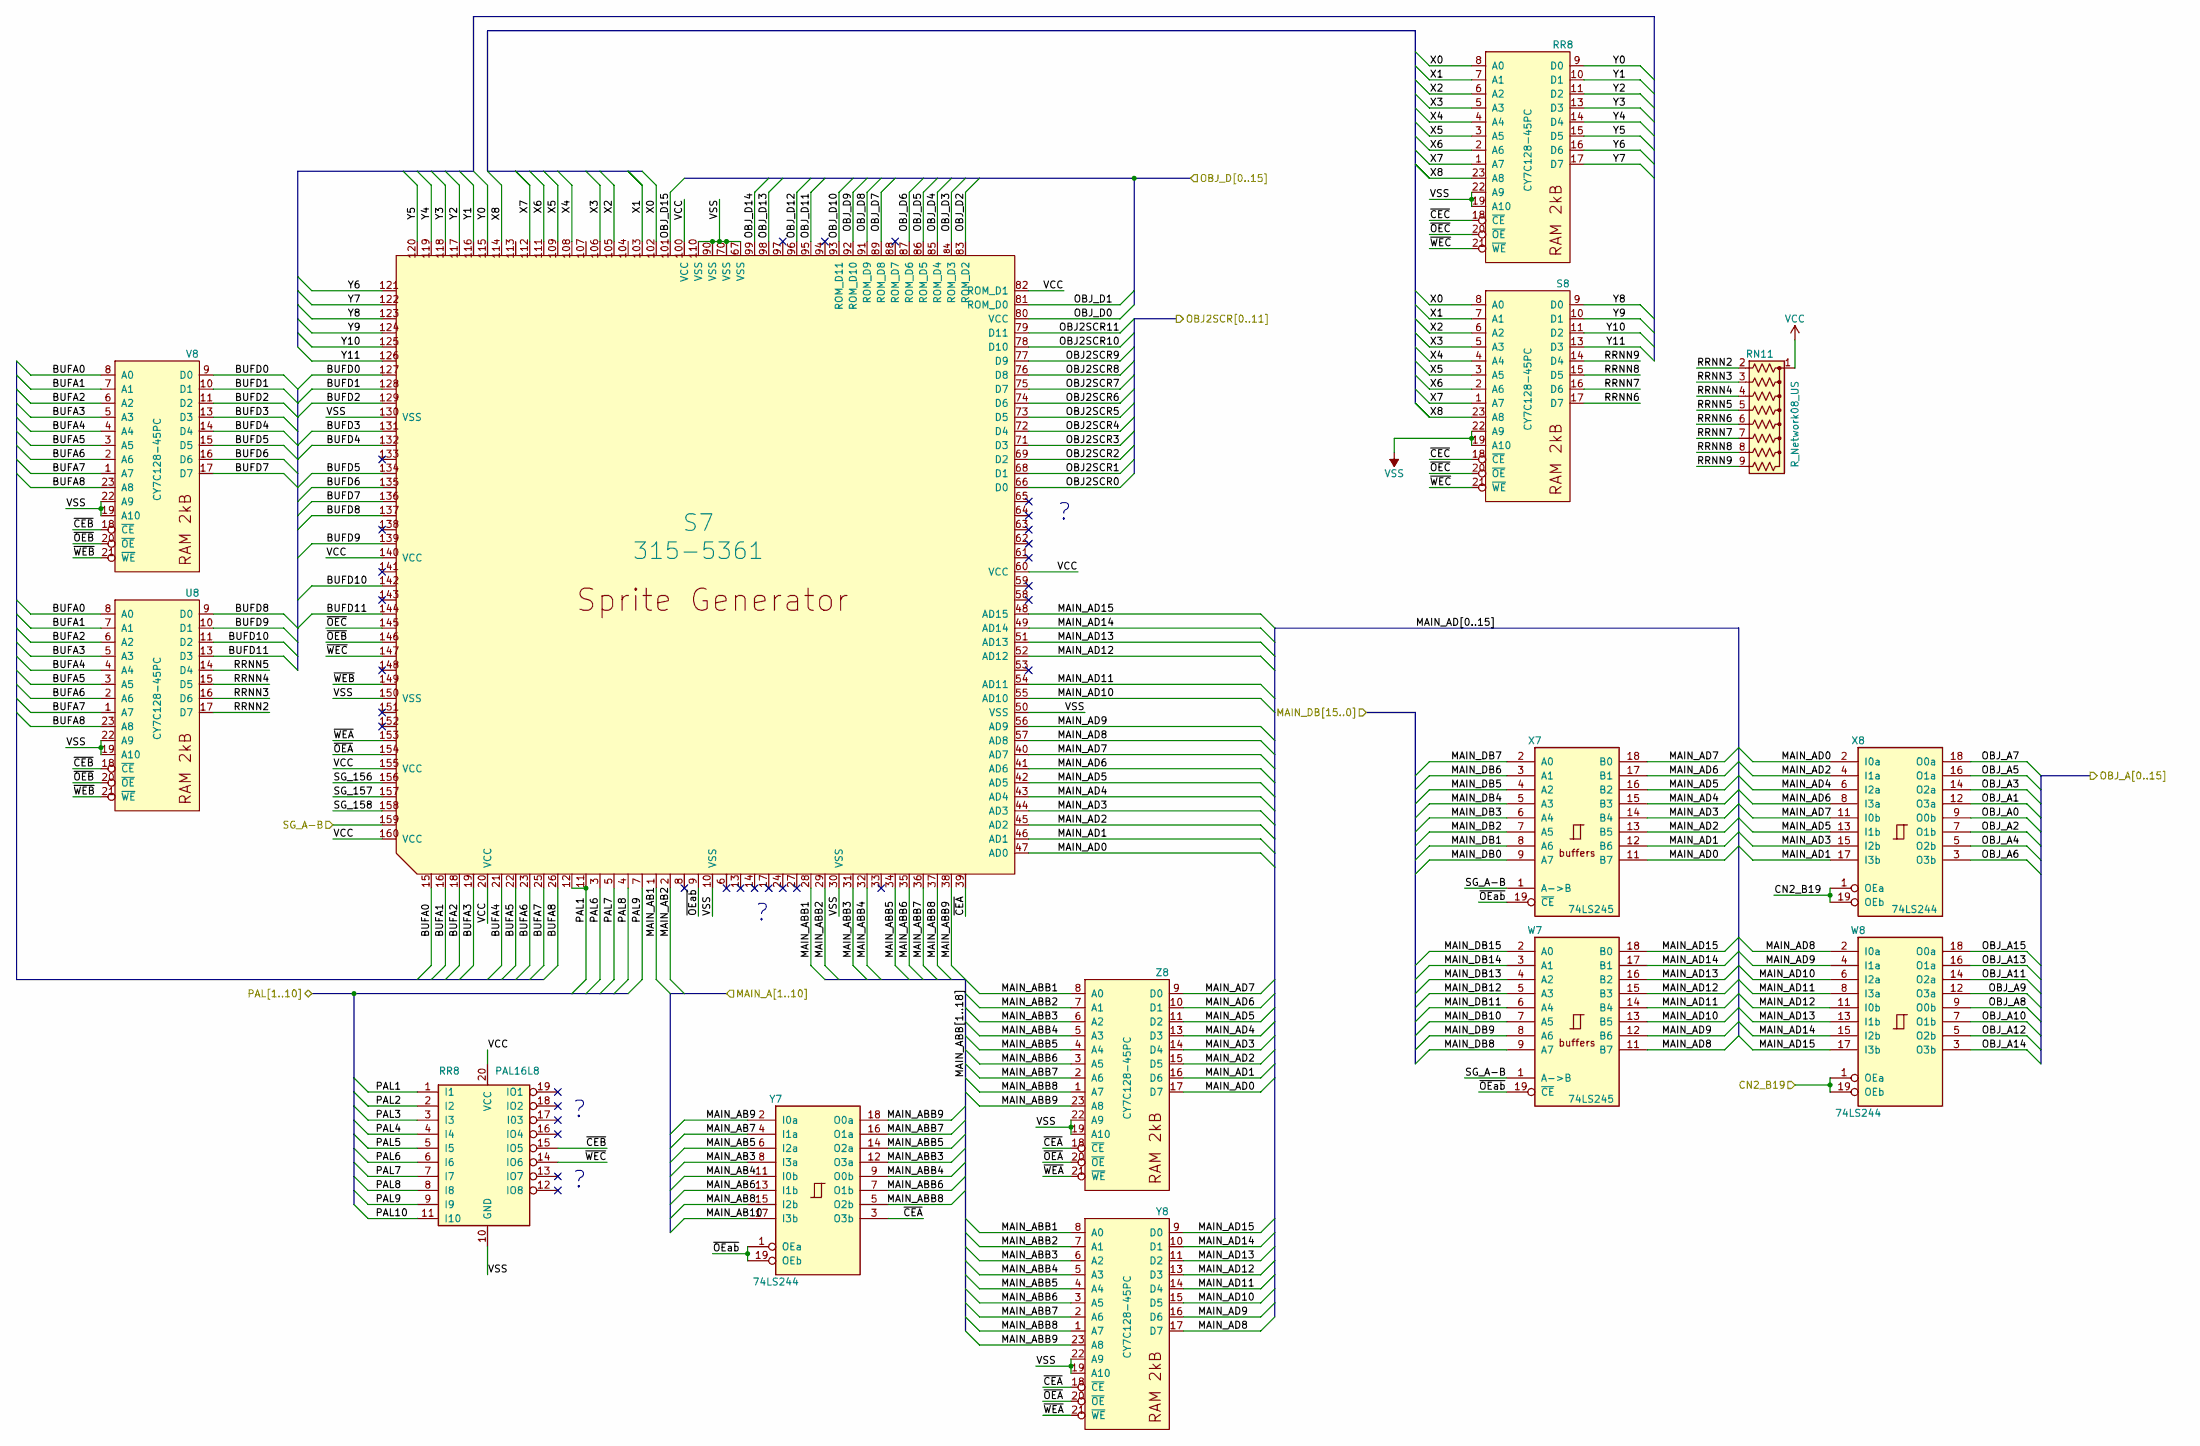
[picture p39: schematic gfx_obj.kicad_sch]

Parts:
RN11: R_Network08_US; R_Array_SIP9
RR8: CY7C128-45PC
S7: 315-5361
S8: CY7C128-45PC
U8: CY7C128-45PC
V8: CY7C128-45PC
W7: 74LS245
W8: 74LS244
X7: 74LS245
X8: 74LS244
Y7: 74LS244
Y8: CY7C128-45PC
Z8: CY7C128-45PC

Connections:
BUFA0: S7.15, U8.8 (A0), V8.8 (A0)
BUFA1: S7.16, U8.7 (A1), V8.7 (A1)
BUFA2: S7.18, U8.6 (A2), V8.6 (A2)
BUFA3: S7.19, U8.5 (A3), V8.5 (A3)
BUFA4: S7.21, U8.4 (A4), V8.4 (A4)
BUFA5: S7.22, U8.3 (A5), V8.3 (A5)
BUFA6: S7.23, U8.2 (A6), V8.2 (A6)
BUFA7: S7.25, U8.1 (A7), V8.1 (A7)
BUFA8: S7.26, U8.23 (A8), V8.23 (A8)
BUFD0: S7.127, V8.9 (D0)
BUFD1: S7.128, V8.10 (D1)
BUFD2: S7.129, V8.11 (D2)
BUFD3: S7.131, V8.13 (D3)
BUFD4: S7.132, V8.14 (D4)
BUFD5: S7.134, V8.15 (D5)
BUFD6: S7.135, V8.16 (D6)
BUFD7: S7.136, V8.17 (D7)
BUFD8: S7.137, U8.9 (D0)
BUFD9: S7.139, U8.10 (D1)
BUFD10: S7.142, U8.11 (D2)
BUFD11: S7.144, U8.13 (D3)
CN2_B19: W8.1 (OEa), W8.19 (OEb), X8.1 (OEa), X8.19 (OEb)
MAIN_AB1: S7.1
MAIN_AB2: S7.2
MAIN_AB3: Y7.8 (I3a)
MAIN_AB4: Y7.11 (I0b)
MAIN_AB5: Y7.6 (I2a)
MAIN_AB6: Y7.13 (I1b)
MAIN_AB7: Y7.4 (I1a)
MAIN_AB8: Y7.15 (I2b)
MAIN_AB9: Y7.2 (I0a)
MAIN_AB10: Y7.17 (I3b)
MAIN_ABB1: S7.28, Y8.8 (A0), Z8.8 (A0)
MAIN_ABB2: S7.29, Y8.7 (A1), Z8.7 (A1)
MAIN_ABB3: S7.31, Y7.12 (O3a), Y8.6 (A2), Z8.6 (A2)
MAIN_ABB4: S7.32, Y7.9 (O0b), Y8.5 (A3), Z8.5 (A3)
MAIN_ABB5: S7.34, Y7.14 (O2a), Y8.4 (A4), Z8.4 (A4)
MAIN_ABB6: S7.35, Y7.7 (O1b), Y8.3 (A5), Z8.3 (A5)
MAIN_ABB7: S7.36, Y7.16 (O1a), Y8.2 (A6), Z8.2 (A6)
MAIN_ABB8: S7.37, Y7.5 (O2b), Y8.1 (A7), Z8.1 (A7)
MAIN_ABB9: S7.38, Y7.18 (O0a), Y8.23 (A8), Z8.23 (A8)
MAIN_AD0: S7.47 (AD0), X7.11 (B7), X8.2 (I0a), Z8.17 (D7)
MAIN_AD1: S7.46 (AD1), X7.12 (B6), X8.17 (I3b), Z8.16 (D6)
MAIN_AD2: S7.45 (AD2), X7.13 (B5), X8.4 (I1a), Z8.15 (D5)
MAIN_AD3: S7.44 (AD3), X7.14 (B4), X8.15 (I2b), Z8.14 (D4)
MAIN_AD4: S7.43 (AD4), X7.15 (B3), X8.6 (I2a), Z8.13 (D3)
MAIN_AD5: S7.42 (AD5), X7.16 (B2), X8.13 (I1b), Z8.11 (D2)
MAIN_AD6: S7.41 (AD6), X7.17 (B1), X8.8 (I3a), Z8.10 (D1)
MAIN_AD7: S7.40 (AD7), X7.18 (B0), X8.11 (I0b), Z8.9 (D0)
MAIN_AD8: S7.57 (AD8), W7.11 (B7), W8.2 (I0a), Y8.17 (D7)
MAIN_AD9: S7.56 (AD9), W7.12 (B6), W8.4 (I1a), Y8.16 (D6)
MAIN_AD10: S7.55 (AD10), W7.13 (B5), W8.6 (I2a), Y8.15 (D5)
MAIN_AD11: S7.54 (AD11), W7.14 (B4), W8.8 (I3a), Y8.14 (D4)
MAIN_AD12: S7.52 (AD12), W7.15 (B3), W8.11 (I0b), Y8.13 (D3)
MAIN_AD13: S7.51 (AD13), W7.16 (B2), W8.13 (I1b), Y8.11 (D2)
MAIN_AD14: S7.49 (AD14), W7.17 (B1), W8.15 (I2b), Y8.10 (D1)
MAIN_AD15: S7.48 (AD15), W7.18 (B0), W8.17 (I3b), Y8.9 (D0)
MAIN_DB0: X7.9 (A7)
MAIN_DB1: X7.8 (A6)
MAIN_DB2: X7.7 (A5)
MAIN_DB3: X7.6 (A4)
MAIN_DB4: X7.5 (A3)
MAIN_DB5: X7.4 (A2)
MAIN_DB6: X7.3 (A1)
MAIN_DB7: X7.2 (A0)
MAIN_DB8: W7.9 (A7)
MAIN_DB9: W7.8 (A6)
MAIN_DB10: W7.7 (A5)
MAIN_DB11: W7.6 (A4)
MAIN_DB12: W7.5 (A3)
MAIN_DB13: W7.4 (A2)
MAIN_DB14: W7.3 (A1)
MAIN_DB15: W7.2 (A0)
unnamed: S8.19 (A10), S8.22 (A9)
OBJ2SCR0: S7.66 (D0)
OBJ2SCR1: S7.68 (D1)
OBJ2SCR2: S7.69 (D2)
OBJ2SCR3: S7.71 (D3)
OBJ2SCR4: S7.72 (D4)
OBJ2SCR5: S7.73 (D5)
OBJ2SCR6: S7.74 (D6)
OBJ2SCR7: S7.75 (D7)
OBJ2SCR8: S7.76 (D8)
OBJ2SCR9: S7.77 (D9)
OBJ2SCR10: S7.78 (D10)
OBJ2SCR11: S7.79 (D11)
OBJ_A0: X8.9 (O0b)
OBJ_A1: X8.12 (O3a)
OBJ_A2: X8.7 (O1b)
OBJ_A3: X8.14 (O2a)
OBJ_A4: X8.5 (O2b)
OBJ_A5: X8.16 (O1a)
OBJ_A6: X8.3 (O3b)
OBJ_A7: X8.18 (O0a)
OBJ_A8: W8.9 (O0b)
OBJ_A9: W8.12 (O3a)
OBJ_A10: W8.7 (O1b)
OBJ_A11: W8.14 (O2a)
OBJ_A12: W8.5 (O2b)
OBJ_A13: W8.16 (O1a)
OBJ_A14: W8.3 (O3b)
OBJ_A15: W8.18 (O0a)
OBJ_D0: S7.80 (VCC)
OBJ_D1: S7.81 (ROM_D0)
OBJ_D2: S7.83 (ROM_D2)
OBJ_D3: S7.84 (ROM_D3)
OBJ_D4: S7.85 (ROM_D4)
OBJ_D5: S7.86 (ROM_D5)
OBJ_D6: S7.87 (ROM_D6)
OBJ_D7: S7.89 (ROM_D8)
OBJ_D8: S7.91 (ROM_D9)
OBJ_D9: S7.92 (ROM_D10)
OBJ_D10: S7.93 (ROM_D11)
OBJ_D11: S7.95
OBJ_D12: S7.96
OBJ_D13: S7.98
OBJ_D14: S7.99
OBJ_D15: S7.101
PAL1: RR8.1 (I1), S7.11, S7.12
PAL2: RR8.2 (I2)
PAL3: RR8.3 (I3)
PAL4: RR8.4 (I4)
PAL5: RR8.5 (I5)
PAL6: RR8.6 (I6), S7.3
PAL7: RR8.7 (I7), S7.5
PAL8: RR8.8 (I8), S7.4
PAL9: RR8.9 (I9), S7.7
PAL10: RR8.11 (I10)
RRNN2: RN11.2 (R1), U8.17 (D7)
RRNN3: RN11.3 (R2), U8.16 (D6)
RRNN4: RN11.4 (R3), U8.15 (D5)
RRNN5: RN11.5 (R4), U8.14 (D4)
RRNN6: RN11.6 (R5), S8.17 (D7)
RRNN7: RN11.7 (R6), S8.16 (D6)
RRNN8: RN11.8 (R7), S8.15 (D5)
RRNN9: RN11.9 (R8), S8.14 (D4)
SG_156: S7.156
SG_157: S7.157
SG_158: S7.158
SG_A-B: S7.159, W7.1 (A->B), X7.1 (A->B)
VCC: RR8.20 (VCC), S7.20 (VCC), S7.60 (VCC), S7.82 (ROM_D1), S7.100 (VCC), S7.140 (VCC), S7.155 (VCC), S7.160 (VCC)
VSS: RR8.10 (GND), RR8.19 (IO1), RR8.22 (A9), S7.10 (VSS), S7.30 (VSS), S7.50 (VSS), S7.67 (VSS), S7.70 (VSS), S7.90 (VSS), S7.110 (VSS), S7.130 (VSS), S7.150 (VSS), U8.19 (A10), U8.22 (A9), V8.19 (A10), V8.22 (A9), Y8.19 (A10), Y8.22 (A9), Z8.19 (A10), Z8.22 (A9)
X0: RR8.8 (I8), S7.102, S8.8 (A0)
X1: RR8.7 (I7), S7.103, S8.7 (A1)
X2: RR8.6 (I6), S7.105, S8.6 (A2)
X3: RR8.5 (I5), S7.106, S8.5 (A3)
X4: RR8.4 (I4), S7.108, S8.4 (A4)
X5: RR8.3 (I3), S7.109, S8.3 (A5)
X6: RR8.2 (I2), S7.111, S8.2 (A6)
X7: RR8.1 (I1), S7.112, S8.1 (A7)
X8: RR8.23 (A8), S7.114, S8.23 (A8)
Y0: RR8.9 (I9), S7.115
Y1: RR8.10 (GND), S7.116
Y2: RR8.11 (I10), S7.117
Y3: RR8.13 (IO7), S7.118
Y4: RR8.14 (IO6), S7.119
Y5: RR8.15 (IO5), S7.120
Y6: RR8.16 (IO4), S7.121
Y7: RR8.17 (I03), S7.122
Y8: S7.123, S8.9 (D0)
Y9: S7.124, S8.10 (D1)
Y10: S7.125, S8.11 (D2)
Y11: S7.126, S8.13 (D3)
~CEA: S7.39, Y7.3 (O3b), Y8.18 (~CE), Z8.18 (~CE)
~CEB: RR8.15 (IO5), U8.18 (~CE), V8.18 (~CE)
~CEC: RR8.18 (IO2), S8.18 (~CE)
~OEA: S7.154, Y8.20 (~OE), Z8.20 (~OE)
~OEB: S7.146, U8.20 (~OE), V8.20 (~OE)
~OEC: RR8.20 (VCC), S7.145, S8.20 (~OE)
~OEab: S7.9, W7.19 (~CE), X7.19 (~CE), Y7.1 (OEa), Y7.19 (OEb)
~WEA: S7.153, Y8.21 (~WE), Z8.21 (~WE)
~WEB: S7.149, U8.21 (~WE), V8.21 (~WE)
~WEC: RR8.14 (IO6), RR8.21 (~WE), S7.147, S8.21 (~WE)
