jotego/jts16/cores/s18/sch/gfx_scr.kicad_sch

## KiCad design cores/s18/sch/gfx_scr.kicad_sch (2022-12-19)

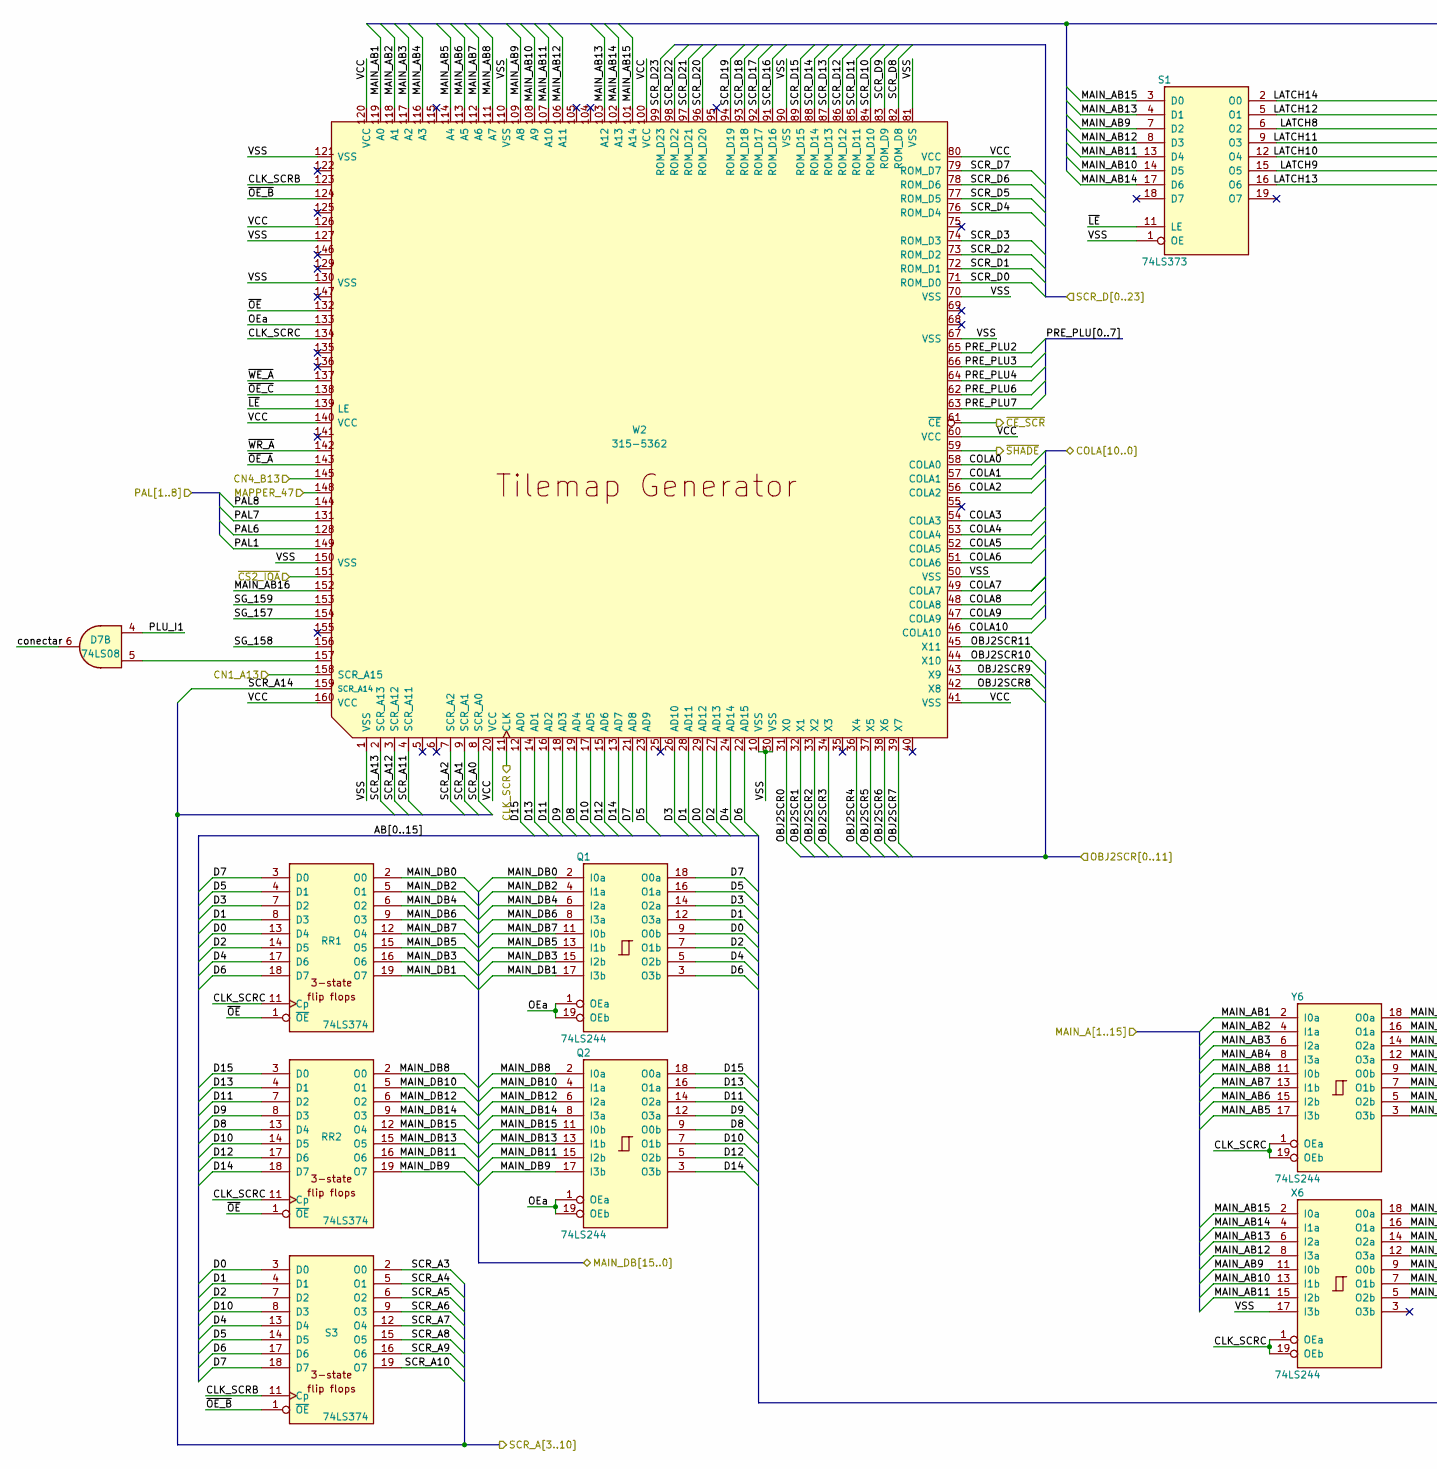
[picture p40: schematic gfx_scr.kicad_sch, part in row 1, column 1]

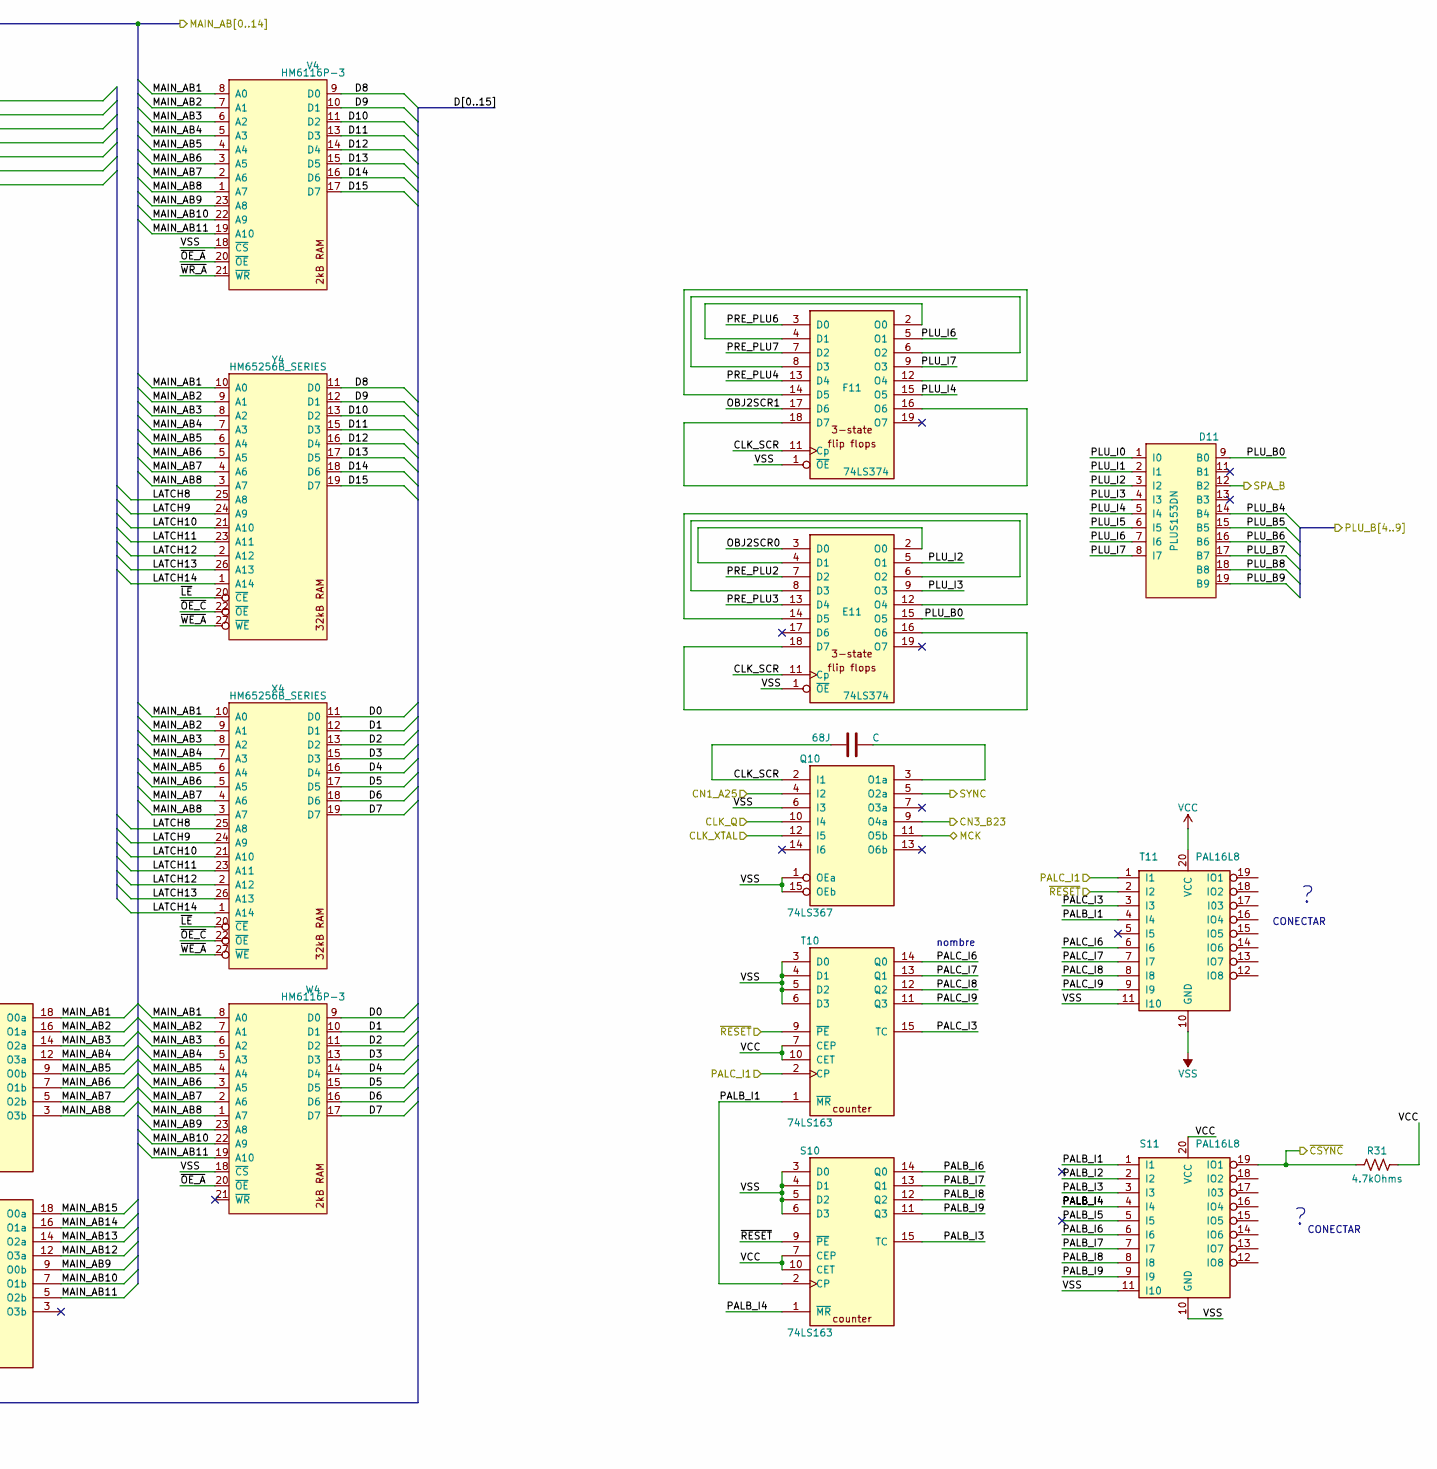
[picture p41: schematic gfx_scr.kicad_sch, part in row 1, column 2]

Parts:
4.7kOhms: R31
68J: C
D7: 74LS08
D11: PLUS153DN
E11: 74LS374
F11: 74LS374
Q1, Q2: 74LS244
Q10: 74LS367
RR1, RR2: 74LS374
S1: 74LS373
S3: 74LS374
S10: 74LS163
S11: PAL16L8
T10: 74LS163
T11: PAL16L8
V4: HM6116P-3
W2: 315-5362
W4: HM6116P-3
X4: HM65256B_SERIES
X6: 74LS244
Y4: HM65256B_SERIES
Y6: 74LS244

Connections:
CLK_Q: Q10.10 (I4)
CLK_SCR: 68J.1, E11.11 (Cp), F11.11 (Cp), Q10.2 (I1), W2.11 (CLK)
CLK_SCRB: S3.11 (Cp), W2.123
CLK_SCRC: RR1.11 (Cp), RR2.11 (Cp), W2.134, X6.1 (OEa), X6.19 (OEb), Y6.1 (OEa), Y6.19 (OEb)
CLK_XTAL: Q10.12 (I5)
CN1_A13: W2.158 (SCR_A15)
CN1_A25: Q10.4 (I2)
CN3_B23: Q10.9 (O4a)
CN4_B13: W2.145
COLA0: W2.58 (COLA0)
COLA1: W2.57 (COLA1)
COLA2: W2.56 (COLA2)
COLA3: W2.54 (COLA3)
COLA4: W2.53 (COLA4)
COLA5: W2.52 (COLA5)
COLA6: W2.51 (COLA6)
COLA7: W2.49 (COLA7)
COLA8: W2.48 (COLA8)
COLA9: W2.47 (COLA9)
COLA10: W2.46 (COLA10)
D0: Q1.9 (O0b), RR1.13 (D4), S3.3 (D0), W2.29 (AD12), W4.9 (D0), X4.11 (D0)
D1: Q1.12 (O3a), RR1.8 (D3), S3.4 (D1), W2.28 (AD11), W4.10 (D1), X4.12 (D1)
D2: Q1.7 (O1b), RR1.14 (D5), S3.7 (D2), W2.27 (AD13), W4.11 (D2), X4.13 (D2)
D3: Q1.14 (O2a), RR1.7 (D2), W2.26 (AD10), W4.13 (D3), X4.15 (D3)
D4: Q1.5 (O2b), RR1.17 (D6), S3.13 (D4), W2.24 (AD14), W4.14 (D4), X4.16 (D4)
D5: Q1.16 (O1a), RR1.4 (D1), S3.14 (D5), W2.23 (AD9), W4.15 (D5), X4.17 (D5)
D6: Q1.3 (O3b), RR1.18 (D7), S3.17 (D6), W2.22 (AD15), W4.16 (D6), X4.18 (D6)
D7: Q1.18 (O0a), RR1.3 (D0), S3.18 (D7), W2.21 (AD8), W4.17 (D7), X4.19 (D7)
D8: Q2.9 (O0b), RR2.13 (D4), V4.9 (D0), W2.19 (AD4), Y4.11 (D0)
D9: Q2.12 (O3a), RR2.8 (D3), V4.10 (D1), W2.18 (AD3), Y4.12 (D1)
D10: Q2.7 (O1b), RR2.14 (D5), S3.8 (D3), V4.11 (D2), W2.17 (AD5), Y4.13 (D2)
D11: Q2.14 (O2a), RR2.7 (D2), V4.13 (D3), W2.16 (AD2), Y4.15 (D3)
D12: Q2.5 (O2b), RR2.17 (D6), V4.14 (D4), W2.15 (AD6), Y4.16 (D4)
D13: Q2.16 (O1a), RR2.4 (D1), V4.15 (D5), W2.14 (AD1), Y4.17 (D5)
D14: Q2.3 (O3b), RR2.18 (D7), V4.16 (D6), W2.13 (AD7), Y4.18 (D6)
D15: Q2.18 (O0a), RR2.3 (D0), V4.17 (D7), W2.12 (AD0), Y4.19 (D7)
LATCH8: S1.6 (O2), X4.25 (A8), Y4.25 (A8)
LATCH9: S1.15 (O5), X4.24 (A9), Y4.24 (A9)
LATCH10: S1.12 (O4), X4.21 (A10), Y4.21 (A10)
LATCH11: S1.9 (O3), X4.23 (A11), Y4.23 (A11)
LATCH12: S1.5 (O1), X4.2 (A12), Y4.2 (A12)
LATCH13: S1.16 (O6), X4.26 (A13), Y4.26 (A13)
LATCH14: S1.2 (O0), X4.1 (A14), Y4.1 (A14)
MAIN_AB1: V4.8 (A0), W2.119 (A0), W4.8 (A0), X4.10 (A0), Y4.10 (A0), Y6.2 (I0a), Y6.18 (O0a)
MAIN_AB2: V4.7 (A1), W2.118 (A1), W4.7 (A1), X4.9 (A1), Y4.9 (A1), Y6.4 (I1a), Y6.16 (O1a)
MAIN_AB3: V4.6 (A2), W2.117 (A2), W4.6 (A2), X4.8 (A2), Y4.8 (A2), Y6.6 (I2a), Y6.14 (O2a)
MAIN_AB4: V4.5 (A3), W2.116 (A3), W4.5 (A3), X4.7 (A3), Y4.7 (A3), Y6.8 (I3a), Y6.12 (O3a)
MAIN_AB5: V4.4 (A4), W2.114 (A4), W4.4 (A4), X4.6 (A4), Y4.6 (A4), Y6.9 (O0b), Y6.17 (I3b)
MAIN_AB6: V4.3 (A5), W2.113 (A5), W4.3 (A5), X4.5 (A5), Y4.5 (A5), Y6.7 (O1b), Y6.15 (I2b)
MAIN_AB7: V4.2 (A6), W2.112 (A6), W4.2 (A6), X4.4 (A6), Y4.4 (A6), Y6.5 (O2b), Y6.13 (I1b)
MAIN_AB8: V4.1 (A7), W2.111 (A7), W4.1 (A7), X4.3 (A7), Y4.3 (A7), Y6.3 (O3b), Y6.11 (I0b)
MAIN_AB9: S1.7 (D2), V4.23 (A8), W2.109 (A8), W4.23 (A8), X6.9 (O0b), X6.11 (I0b)
MAIN_AB10: S1.14 (D5), V4.22 (A9), W2.108 (A9), W4.22 (A9), X6.7 (O1b), X6.13 (I1b)
MAIN_AB11: S1.13 (D4), V4.19 (A10), W2.107 (A10), W4.19 (A10), X6.5 (O2b), X6.15 (I2b)
MAIN_AB12: S1.8 (D3), W2.106 (A11), X6.8 (I3a), X6.12 (O3a)
MAIN_AB13: S1.4 (D1), W2.103 (A12), X6.6 (I2a), X6.14 (O2a)
MAIN_AB14: S1.17 (D6), W2.102 (A13), X6.4 (I1a), X6.16 (O1a)
MAIN_AB15: S1.3 (D0), W2.101 (A14), X6.2 (I0a), X6.18 (O0a)
MAIN_AB16: W2.152
MAIN_DB0: Q1.2 (I0a), RR1.2 (O0)
MAIN_DB1: Q1.17 (I3b), RR1.19 (O7)
MAIN_DB2: Q1.4 (I1a), RR1.5 (O1)
MAIN_DB3: Q1.15 (I2b), RR1.16 (O6)
MAIN_DB4: Q1.6 (I2a), RR1.6 (O2)
MAIN_DB5: Q1.13 (I1b), RR1.15 (O5)
MAIN_DB6: Q1.8 (I3a), RR1.9 (O3)
MAIN_DB7: Q1.11 (I0b), RR1.12 (O4)
MAIN_DB8: Q2.2 (I0a), RR2.2 (O0)
MAIN_DB9: Q2.17 (I3b), RR2.19 (O7)
MAIN_DB10: Q2.4 (I1a), RR2.5 (O1)
MAIN_DB11: Q2.15 (I2b), RR2.16 (O6)
MAIN_DB12: Q2.6 (I2a), RR2.6 (O2)
MAIN_DB13: Q2.13 (I1b), RR2.15 (O5)
MAIN_DB14: Q2.8 (I3a), RR2.9 (O3)
MAIN_DB15: Q2.11 (I0b), RR2.12 (O4)
MAPPER_47: W2.148
MCK: Q10.11 (O5b)
unnamed: 68J.2, Q10.3 (O1a)
unnamed: D7.5, W2.157
unnamed: E11.2 (O0), E11.4 (D1)
unnamed: E11.6 (O2), E11.8 (D3)
unnamed: E11.12 (O4), E11.14 (D5)
unnamed: E11.16 (O6), E11.18 (D7)
unnamed: F11.2 (O0), F11.4 (D1)
unnamed: F11.6 (O2), F11.8 (D3)
unnamed: F11.12 (O4), F11.14 (D5)
unnamed: F11.16 (O6), F11.18 (D7)
OBJ2SCR0: E11.3 (D0), W2.31 (X0)
OBJ2SCR1: F11.17 (D6), W2.32 (X1)
OBJ2SCR2: W2.33 (X2)
OBJ2SCR3: W2.34 (X3)
OBJ2SCR4: W2.36 (X4)
OBJ2SCR5: W2.37 (X5)
OBJ2SCR6: W2.38 (X6)
OBJ2SCR7: W2.39 (X7)
OBJ2SCR8: W2.42 (X8)
OBJ2SCR9: W2.43 (X9)
OBJ2SCR10: W2.44 (X10)
OBJ2SCR11: W2.45 (X11)
OEa: Q1.1 (OEa), Q1.19 (OEb), Q2.1 (OEa), Q2.19 (OEb), W2.133
PAL1: W2.149
PAL6: W2.128
PAL7: W2.131
PAL8: W2.144
PALB_I1: S10.2 (CP), S11.1 (I1), T10.1 (~MR), T11.4 (I4)
PALB_I2: S11.2 (I2)
PALB_I3: S10.15 (TC), S11.3 (I3)
PALB_I4: S10.1 (~MR), S11.4 (I4)
PALB_I5: S11.5 (I5)
PALB_I6: S10.14 (Q0), S11.6 (I6)
PALB_I7: S10.13 (Q1), S11.7 (I7)
PALB_I8: S10.12 (Q2), S11.8 (I8)
PALB_I9: S10.11 (Q3), S11.9 (I9)
PALC_I1: T10.2 (CP), T11.1 (I1)
PALC_I3: T10.15 (TC), T11.3 (I3)
PALC_I6: T10.14 (Q0), T11.6 (I6)
PALC_I7: T10.13 (Q1), T11.7 (I7)
PALC_I8: T10.12 (Q2), T11.8 (I8)
PALC_I9: T10.11 (Q3), T11.9 (I9)
PLU_B0: D11.9 (B0), E11.15 (O5)
PLU_B4: D11.14 (B4)
PLU_B5: D11.15 (B5)
PLU_B6: D11.16 (B6)
PLU_B7: D11.17 (B7)
PLU_B8: D11.18 (B8)
PLU_B9: D11.19 (B9)
PLU_I0: D11.1 (I0)
PLU_I1: D7.4, D11.2 (I1)
PLU_I2: D11.3 (I2), E11.5 (O1)
PLU_I3: D11.4 (I3), E11.9 (O3)
PLU_I4: D11.5 (I4), F11.15 (O5)
PLU_I5: D11.6 (I5)
PLU_I6: D11.7 (I6), F11.5 (O1)
PLU_I7: D11.8 (I7), F11.9 (O3)
PRE_PLU2: E11.7 (D2), W2.65
PRE_PLU3: E11.13 (D4), W2.66
PRE_PLU4: F11.13 (D4), W2.64
PRE_PLU6: F11.3 (D0), W2.62
PRE_PLU7: F11.7 (D2), W2.63
SCR_A0: W2.8 (SCR_A0)
SCR_A1: W2.9 (SCR_A1)
SCR_A2: W2.7 (SCR_A2)
SCR_A3: S3.2 (O0)
SCR_A4: S3.5 (O1)
SCR_A5: S3.6 (O2)
SCR_A6: S3.9 (O3)
SCR_A7: S3.12 (O4)
SCR_A8: S3.15 (O5)
SCR_A9: S3.16 (O6)
SCR_A10: S3.19 (O7)
SCR_A11: W2.4 (SCR_A11)
SCR_A12: W2.3 (SCR_A12)
SCR_A13: W2.2 (SCR_A13)
SCR_A14: W2.159 (SCR_A14)
SCR_D0: W2.71 (ROM_D0)
SCR_D1: W2.72 (ROM_D1)
SCR_D2: W2.73 (ROM_D2)
SCR_D3: W2.74 (ROM_D3)
SCR_D4: W2.76 (ROM_D4)
SCR_D5: W2.77 (ROM_D5)
SCR_D6: W2.78 (ROM_D6)
SCR_D7: W2.79 (ROM_D7)
SCR_D8: W2.82 (ROM_D8)
SCR_D9: W2.83 (ROM_D9)
SCR_D10: W2.84 (ROM_D10)
SCR_D11: W2.85 (ROM_D11)
SCR_D12: W2.86 (ROM_D12)
SCR_D13: W2.87 (ROM_D13)
SCR_D14: W2.88 (ROM_D14)
SCR_D15: W2.89 (ROM_D15)
SCR_D16: W2.91 (ROM_D16)
SCR_D17: W2.92 (ROM_D17)
SCR_D18: W2.93 (ROM_D18)
SCR_D19: W2.94 (ROM_D19)
SCR_D20: W2.96 (ROM_D20)
SCR_D21: W2.97 (ROM_D21)
SCR_D22: W2.98 (ROM_D22)
SCR_D23: W2.99 (ROM_D23)
SG_157: W2.154
SG_158: W2.156
SG_159: W2.153
SPA_B: D11.12 (B2)
SYNC: Q10.5 (O2a)
VCC: 4.7kOhms.1, S10.7 (CEP), S10.10 (CET), S11.20 (VCC), T10.7 (CEP), T10.10 (CET), W2.20 (VCC), W2.41 (VSS), W2.60 (VCC), W2.80 (VCC), W2.100 (VCC), W2.120 (VCC), W2.126, W2.140 (VCC), W2.160 (VCC)
VSS: E11.1 (~OE), F11.1 (~OE), Q10.1 (OEa), Q10.6 (I3), Q10.15 (OEb), S1.1 (OE), S10.3 (D0), S10.4 (D1), S10.5 (D2), S10.6 (D3), S11.10 (GND), S11.11 (I10), T10.3 (D0), T10.4 (D1), T10.5 (D2), T10.6 (D3), T11.11 (I10), V4.18 (~CS), W2.1 (VSS), W2.10 (VSS), W2.30 (VSS), W2.50 (VSS), W2.67 (VSS), W2.70 (VSS), W2.81 (VSS), W2.90 (VSS), W2.110 (VSS), W2.121 (VSS), W2.127, W2.130 (VSS), W2.150 (VSS), W4.18 (~CS), X6.17 (I3b)
conectar: D7.6
~CE_SCR: W2.61 (~CE)
~CS2_IOA: W2.151
~CSYNC: 4.7kOhms.2, S11.19 (IO1)
~LE: S1.11 (LE), W2.139 (LE), X4.20 (~CE), Y4.20 (~CE)
~OE_A: V4.20 (~OE), W2.143, W4.20 (~OE)
~OE_B: S3.1 (~OE), W2.124
~OE_C: W2.138, X4.22 (~OE), Y4.22 (~OE)
~OE: RR1.1 (~OE), RR2.1 (~OE), W2.132
~RESET: S10.9 (~PE), T10.9 (~PE), T11.2 (I2)
~SHADE: W2.59
~WE_A: W2.137, X4.27 (~WE), Y4.27 (~WE)
~WR_A: V4.21 (~WR), W2.142

Notes on the sheet:
CONECTAR
nombre
