jotego/jts16/cores/s18/sch/main.kicad_sch

## KiCad design cores/s18/sch/main.kicad_sch (2022-12-19)

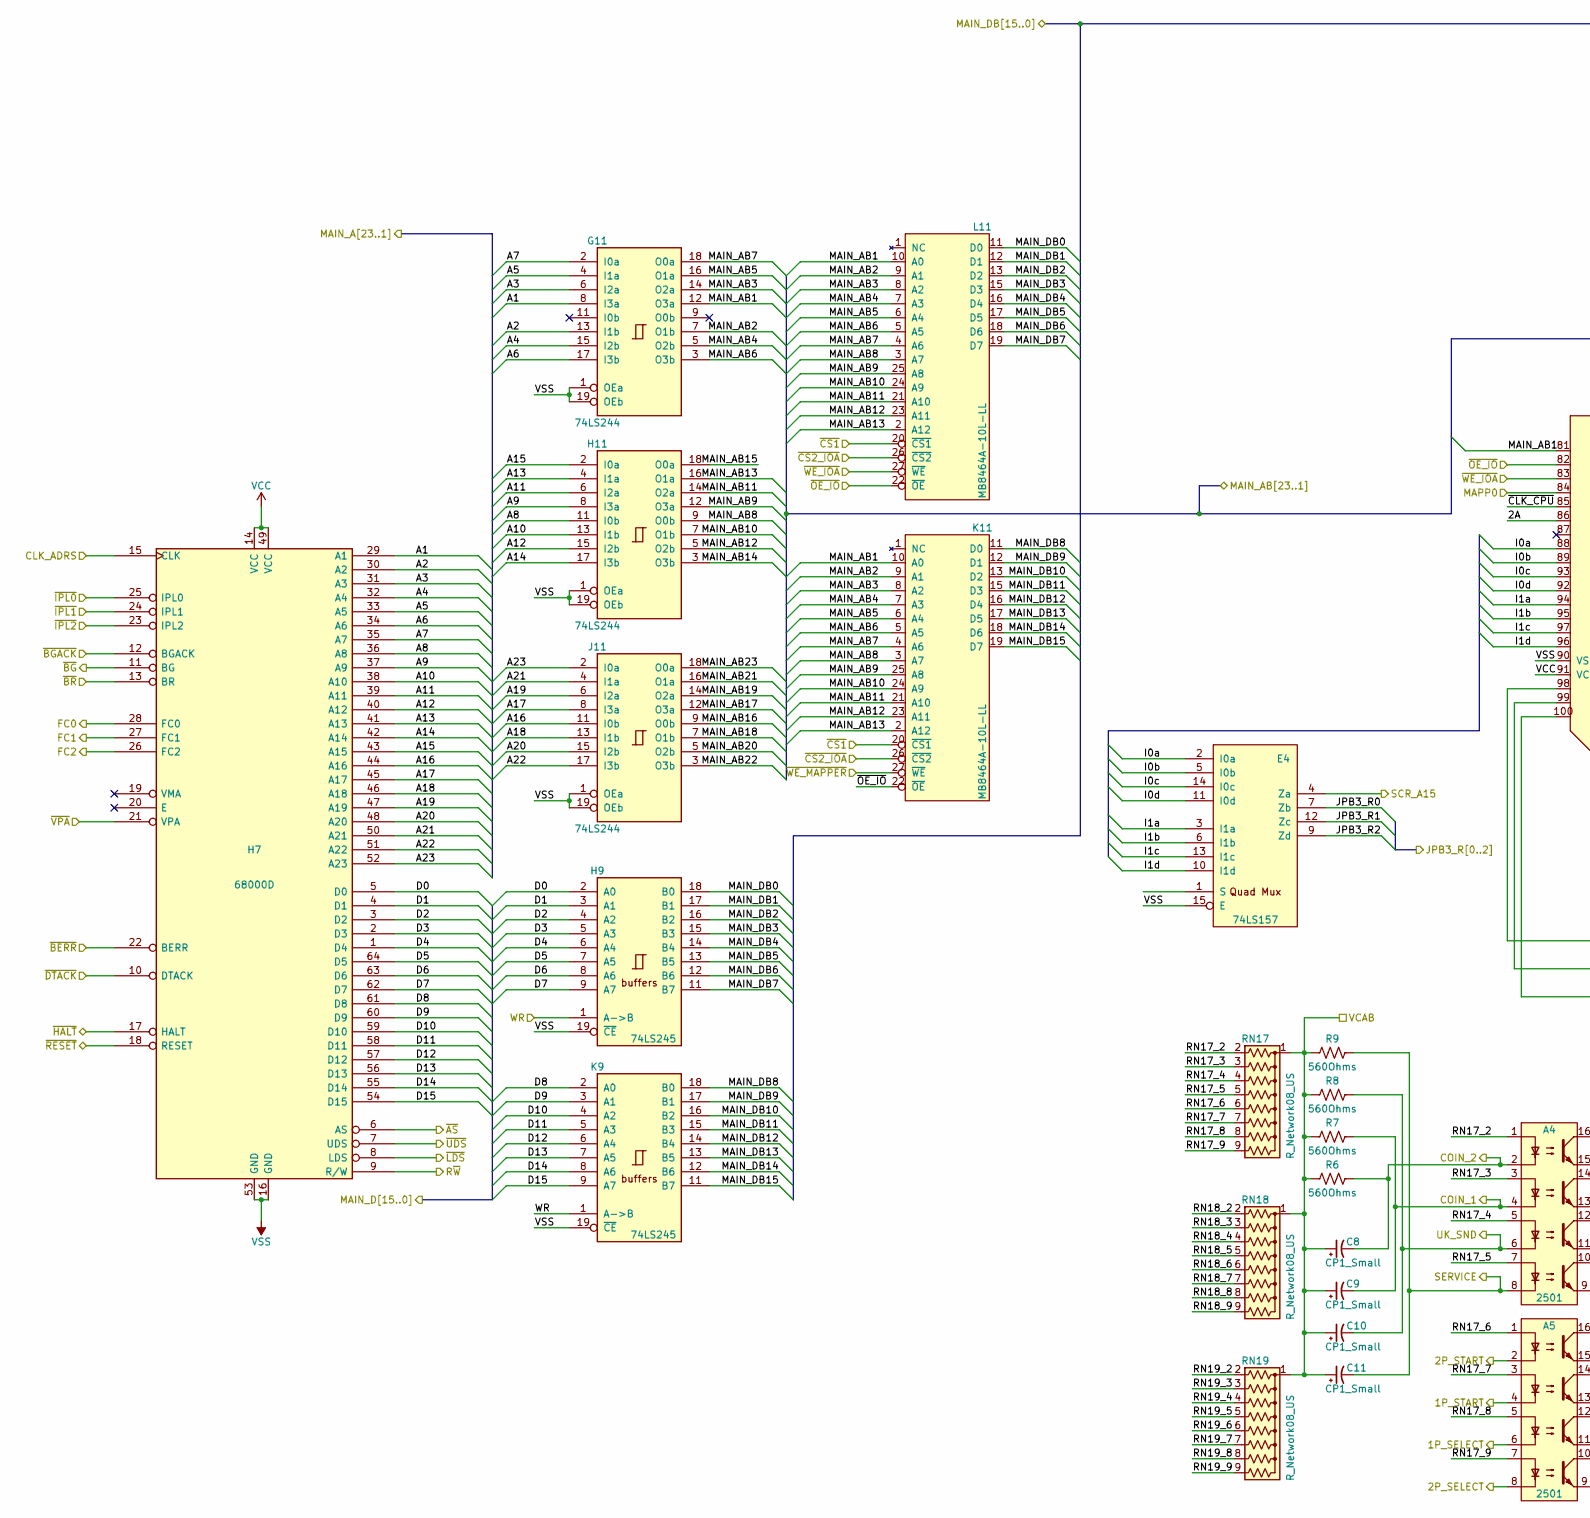
[picture p42: schematic main.kicad_sch, part in row 1, column 1]

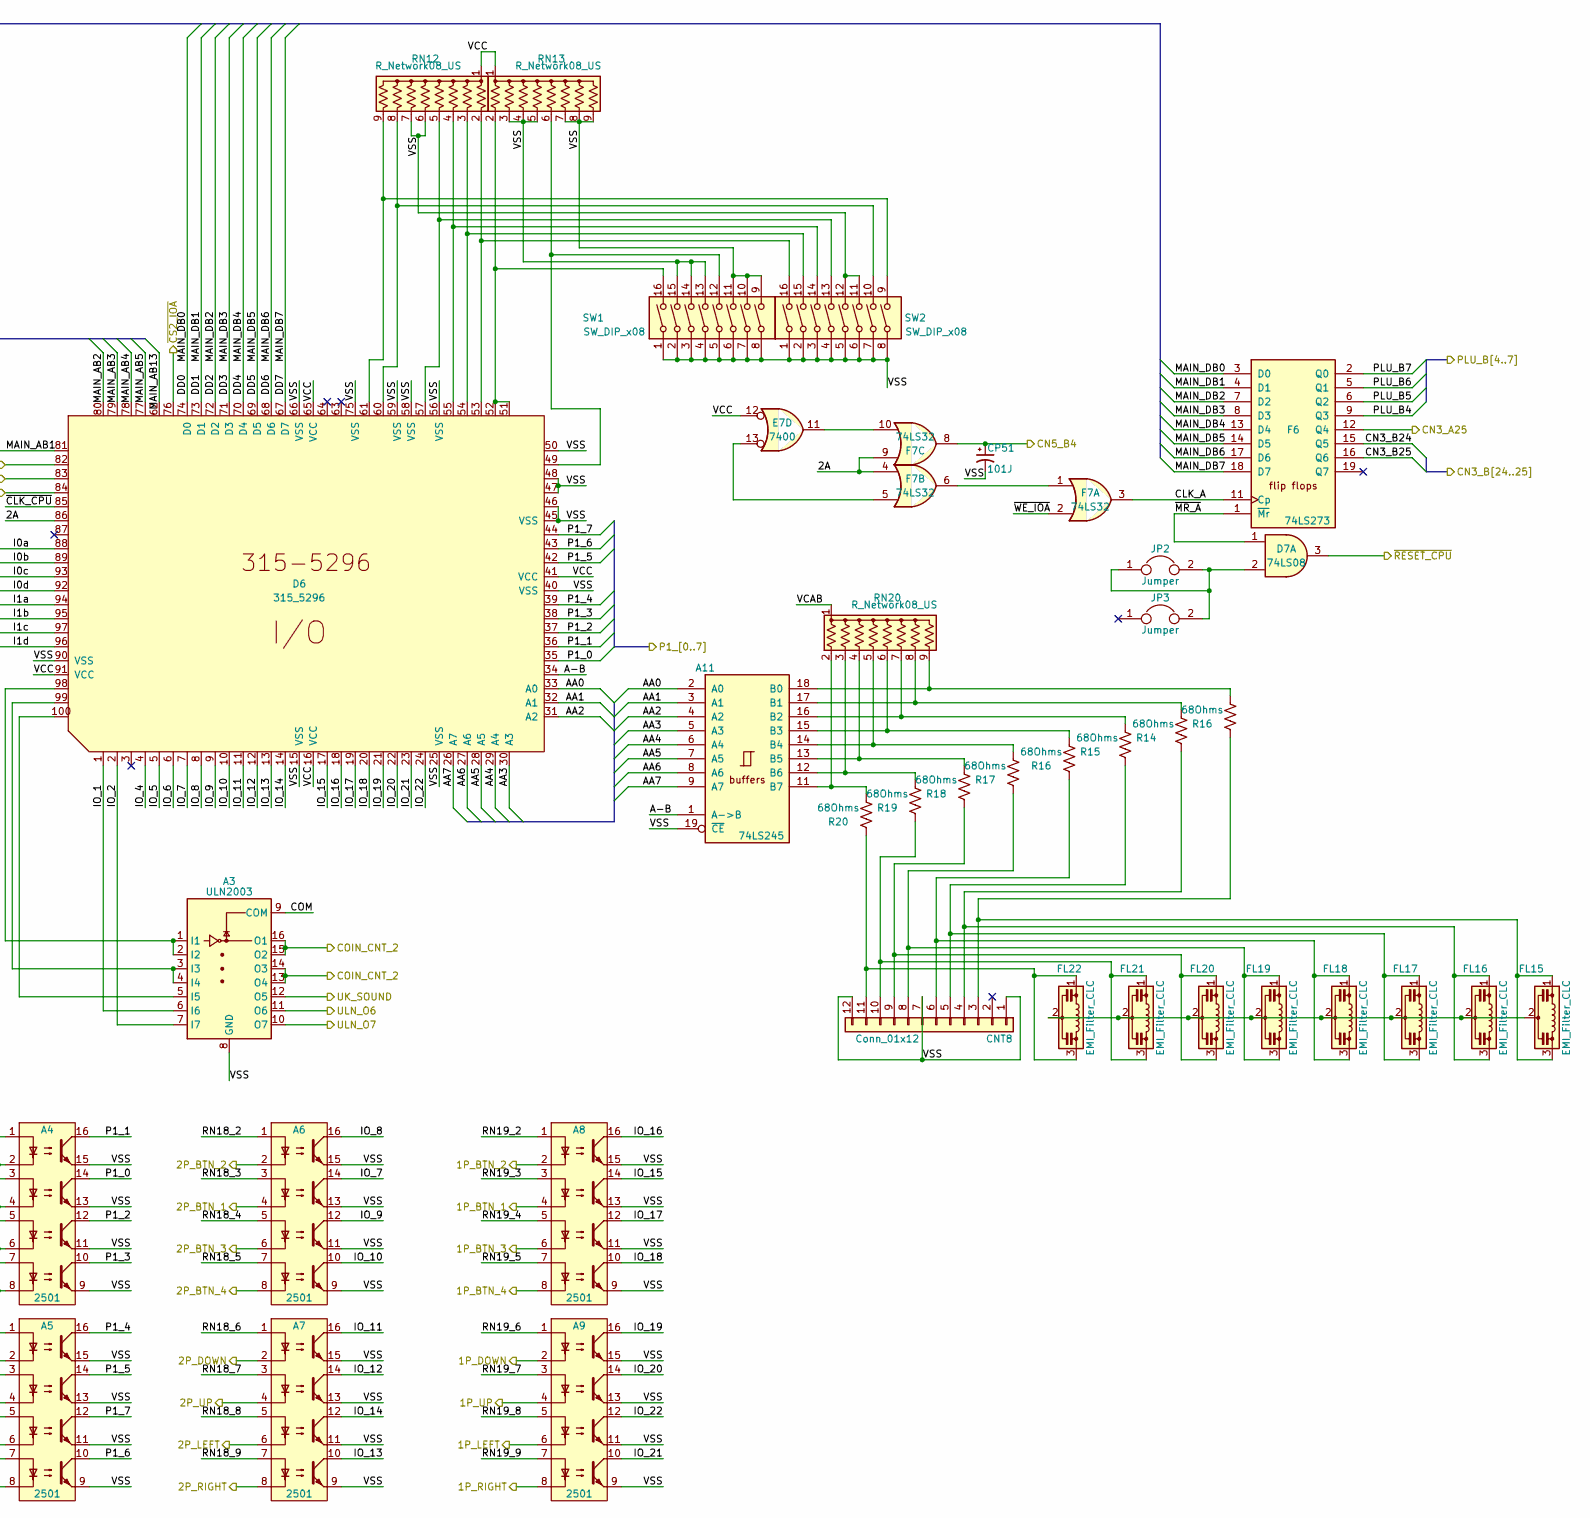
[picture p43: schematic main.kicad_sch, part in row 1, column 2]

Parts:
A3: ULN2003
A4, A5, A6, A7, A8, A9: 2501
A11: 74LS245
C8, C9, C10, C11: CP1_Small
CNT8: Conn_01x12
CP51: 101J
D6: 315_5296
D7: 74LS08
E4: 74LS157
E7: 7400
F6: 74LS273
F7: 74LS32
FL15, FL16, FL17, FL18, FL19, FL20, FL21, FL22: EMI_Filter_CLC
G11: 74LS244
H7: 68000D
H9: 74LS245
H11: 74LS244
J11: 74LS244
JP2, JP3: Jumper
K9: 74LS245
K11: MB8464A-10L-LL
L11: MB8464A-10L-LL
R6, R7, R8, R9: 560Ohms
R14, R15, R16, R17, R18, R19, R20: 68Ohms
RN12, RN13, RN17, RN18, RN19, RN20: R_Network08_US; R_Array_SIP9
SW1, SW2: SW_DIP_x08

Connections:
1P_BTN_1: A8.4
1P_BTN_2: A8.2
1P_BTN_3: A8.6
1P_BTN_4: A8.8
1P_DOWN: A9.2
1P_LEFT: A9.6
1P_RIGHT: A9.8
1P_SELECT: A5.6
1P_START: A5.4
1P_UP: A9.4
2A: D6.86, F7.4, F7.9
2P_BTN_1: A6.4
2P_BTN_2: A6.2
2P_BTN_3: A6.6
2P_BTN_4: A6.8
2P_DOWN: A7.2
2P_LEFT: A7.6
2P_RIGHT: A7.8
2P_SELECT: A5.8
2P_START: A5.2
2P_UP: A7.4
A1: G11.8 (I3a), H7.29 (A1)
A2: G11.13 (I1b), H7.30 (A2)
A3: G11.6 (I2a), H7.31 (A3)
A4: G11.15 (I2b), H7.32 (A4)
A5: G11.4 (I1a), H7.33 (A5)
A6: G11.17 (I3b), H7.34 (A6)
A7: G11.2 (I0a), H7.35 (A7)
A8: H7.36 (A8), H11.11 (I0b)
A9: H7.37 (A9), H11.8 (I3a)
A10: H7.38 (A10), H11.13 (I1b)
A11: H7.39 (A11), H11.6 (I2a)
A12: H7.40 (A12), H11.15 (I2b)
A13: H7.41 (A13), H11.4 (I1a)
A14: H7.42 (A14), H11.17 (I3b)
A15: H7.43 (A15), H11.2 (I0a)
A16: H7.44 (A16), J11.11 (I0b)
A17: H7.45 (A17), J11.8 (I3a)
A18: H7.46 (A18), J11.13 (I1b)
A19: H7.47 (A19), J11.6 (I2a)
A20: H7.48 (A20), J11.15 (I2b)
A21: H7.50 (A21), J11.4 (I1a)
A22: H7.51 (A22), J11.17 (I3b)
A23: H7.52 (A23), J11.2 (I0a)
A-B: A11.1 (A->B), D6.34
AA0: A11.2 (A0), D6.33 (A0)
AA1: A11.3 (A1), D6.32 (A1)
AA2: A11.4 (A2), D6.31 (A2)
AA3: A11.5 (A3), D6.30 (A3)
AA4: A11.6 (A4), D6.29 (A4)
AA5: A11.7 (A5), D6.28 (A5)
AA6: A11.8 (A6), D6.27 (A6)
AA7: A11.9 (A7), D6.26 (A7)
CLK_A: F6.11 (Cp), F7.3
CLK_ADRS: H7.15 (CLK)
CN3_A25: F6.12 (Q4)
CN3_B24: F6.15 (Q5)
CN3_B25: F6.16 (Q6)
CN5_B4: CP51.1, F7.8
COIN_1: A4.4, C9.2, R7.1
COIN_2: A4.2, C8.2, R6.1
COIN_CNT_2: A3.13 (O4), A3.14 (O3), A3.15 (O2), A3.16 (O1)
COM: A3.9 (COM)
D0: H7.5 (D0), H9.2 (A0)
D1: H7.4 (D1), H9.3 (A1)
D2: H7.3 (D2), H9.4 (A2)
D3: H7.2 (D3), H9.5 (A3)
D4: H7.1 (D4), H9.6 (A4)
D5: H7.64 (D5), H9.7 (A5)
D6: H7.63 (D6), H9.8 (A6)
D7: H7.62 (D7), H9.9 (A7)
D8: H7.61 (D8), K9.2 (A0)
D9: H7.60 (D9), K9.3 (A1)
D10: H7.59 (D10), K9.4 (A2)
D11: H7.58 (D11), K9.5 (A3)
D12: H7.57 (D12), K9.6 (A4)
D13: H7.56 (D13), K9.7 (A5)
D14: H7.55 (D14), K9.8 (A6)
D15: H7.54 (D15), K9.9 (A7)
DD0: D6.74 (D0), F6.3 (D0), H9.18 (B0), L11.11 (D0)
DD1: D6.73 (D1), F6.4 (D1), H9.17 (B1), L11.12 (D1)
DD2: D6.72 (D2), F6.7 (D2), H9.16 (B2), L11.13 (D2)
DD3: D6.71 (D3), F6.8 (D3), H9.15 (B3), L11.15 (D3)
DD4: D6.70 (D4), F6.13 (D4), H9.14 (B4), L11.16 (D4)
DD5: D6.69 (D5), F6.14 (D5), H9.13 (B5), L11.17 (D5)
DD6: D6.68 (D6), F6.17 (D6), H9.12 (B6), L11.18 (D6)
DD7: D6.67 (D7), F6.18 (D7), H9.11 (B7), L11.19 (D7)
FC0: H7.28 (FC0)
FC1: H7.27 (FC1)
FC2: H7.26 (FC2)
I0a: D6.88, E4.2 (I0a)
I0b: D6.89, E4.5 (I0b)
I0c: D6.93, E4.14 (I0c)
I0d: D6.92, E4.11 (I0d)
I1a: D6.94, E4.3 (I1a)
I1b: D6.95, E4.6 (I1b)
I1c: D6.97, E4.13 (I1c)
I1d: D6.96, E4.10 (I1d)
IO_1: A3.6 (I6), D6.1
IO_2: A3.7 (I7), D6.2
IO_4: D6.4
IO_5: D6.5
IO_6: D6.6
IO_7: A6.14, D6.7
IO_8: A6.16, D6.8
IO_9: A6.12, D6.9
IO_10: A6.10, D6.10
IO_11: A7.16, D6.11
IO_12: A7.14, D6.12
IO_13: A7.10, D6.13
IO_14: A7.12, D6.14
IO_15: A8.14, D6.17
IO_16: A8.16, D6.18
IO_17: A8.12, D6.19
IO_18: A8.10, D6.20
IO_19: A9.16, D6.21
IO_20: A9.14, D6.22
IO_21: A9.10, D6.23
IO_22: A9.12, D6.24
JPB3_R0: E4.7 (Zb)
JPB3_R1: E4.12 (Zc)
JPB3_R2: E4.9 (Zd)
MAIN_AB1: D6.81, G11.12 (O3a), K11.10 (A0), L11.10 (A0)
MAIN_AB2: D6.80, G11.7 (O1b), K11.9 (A1), L11.9 (A1)
MAIN_AB3: D6.79, G11.14 (O2a), K11.8 (A2), L11.8 (A2)
MAIN_AB4: D6.78, G11.5 (O2b), K11.7 (A3), L11.7 (A3)
MAIN_AB5: D6.77, G11.16 (O1a), K11.6 (A4), L11.6 (A4)
MAIN_AB6: G11.3 (O3b), K11.5 (A5), L11.5 (A5)
MAIN_AB7: G11.18 (O0a), K11.4 (A6), L11.4 (A6)
MAIN_AB8: H11.9 (O0b), K11.3 (A7), L11.3 (A7)
MAIN_AB9: H11.12 (O3a), K11.25 (A8), L11.25 (A8)
MAIN_AB10: H11.7 (O1b), K11.24 (A9), L11.24 (A9)
MAIN_AB11: H11.14 (O2a), K11.21 (A10), L11.21 (A10)
MAIN_AB12: H11.5 (O2b), K11.23 (A11), L11.23 (A11)
MAIN_AB13: D6.62, H11.16 (O1a), K11.2 (A12), L11.2 (A12)
MAIN_AB14: H11.3 (O3b)
MAIN_AB15: H11.18 (O0a)
MAIN_AB16: J11.9 (O0b)
MAIN_AB17: J11.12 (O3a)
MAIN_AB18: J11.7 (O1b)
MAIN_AB19: J11.14 (O2a)
MAIN_AB20: J11.5 (O2b)
MAIN_AB21: J11.16 (O1a)
MAIN_AB22: J11.3 (O3b)
MAIN_AB23: J11.18 (O0a)
MAIN_DB8: K9.18 (B0), K11.11 (D0)
MAIN_DB9: K9.17 (B1), K11.12 (D1)
MAIN_DB10: K9.16 (B2), K11.13 (D2)
MAIN_DB11: K9.15 (B3), K11.15 (D3)
MAIN_DB12: K9.14 (B4), K11.16 (D4)
MAIN_DB13: K9.13 (B5), K11.17 (D5)
MAIN_DB14: K9.12 (B6), K11.18 (D6)
MAIN_DB15: K9.11 (B7), K11.19 (D7)
MAPP0: D6.84
unnamed: A3.1 (I1), A3.2 (I2), D6.98
unnamed: A3.3 (I3), A3.4 (I4), D6.99
unnamed: A3.5 (I5), D6.100
unnamed: A11.11 (B7), R20.1, RN20.2 (R1)
unnamed: A11.12 (B6), R19.1, RN20.3 (R2)
unnamed: A11.13 (B5), R18.1, RN20.4 (R3)
unnamed: A11.14 (B4), R17.1, RN20.5 (R4)
unnamed: A11.15 (B3), R16.1, RN20.6 (R5)
unnamed: A11.16 (B2), R15.1, RN20.7 (R6)
unnamed: A11.17 (B1), R14.1, RN20.8 (R7)
unnamed: A11.18 (B0), R16.1, RN20.9 (R8)
unnamed: CNT8.3, FL15.1, FL15.3, R16.2
unnamed: CNT8.4, FL16.1, FL16.3, R14.2
unnamed: CNT8.5, FL17.1, FL17.3, R15.2
unnamed: CNT8.6, FL18.1, FL18.3, R16.2
unnamed: CNT8.8, FL19.1, FL19.3, R17.2
unnamed: CNT8.9, FL20.1, FL20.3, R18.2
unnamed: CNT8.10, FL21.1, FL21.3, R19.2
unnamed: CNT8.11, FL22.1, FL22.3, R20.2
unnamed: D6.49, RN13.6 (R5), SW1.12
unnamed: D6.51, D6.52, RN13.2 (R1), SW1.16
unnamed: D6.53, RN12.2 (R1), SW2.16
unnamed: D6.54, RN12.3 (R2), SW2.15
unnamed: D6.55, RN12.4 (R3), SW2.14
unnamed: D6.57, RN12.5 (R4), SW2.13
unnamed: D6.60, RN12.8 (R7), SW2.10
unnamed: D6.61, RN12.9 (R8), SW2.9
unnamed: D7.2, JP2.1, JP2.2, JP3.2
unnamed: E7.11, F7.10
unnamed: E7.13, F7.5
unnamed: F7.1, F7.6
unnamed: FL15.2, FL16.2, FL17.2, FL18.2, FL19.2, FL20.2, FL21.2, FL22.2
unnamed: H7.14 (VCC), H7.49 (VCC)
unnamed: H7.16 (GND), H7.53 (GND)
P1_0: A4.14, D6.35
P1_1: A4.16, D6.36
P1_2: A4.12, D6.37
P1_3: A4.10, D6.38
P1_4: A5.16, D6.39
P1_5: A5.14, D6.42
P1_6: A5.10, D6.43
P1_7: A5.12, D6.44
PLU_B4: F6.9 (Q3)
PLU_B5: F6.6 (Q2)
PLU_B6: F6.5 (Q1)
PLU_B7: F6.2 (Q0)
RN17_2: A4.1, RN17.2 (R1)
RN17_3: A4.3, RN17.3 (R2)
RN17_4: A4.5, RN17.4 (R3)
RN17_5: A4.7, RN17.5 (R4)
RN17_6: A5.1, RN17.6 (R5)
RN17_7: A5.3, RN17.7 (R6)
RN17_8: A5.5, RN17.8 (R7)
RN17_9: A5.7, RN17.9 (R8)
RN18_2: A6.1, RN18.2 (R1)
RN18_3: A6.3, RN18.3 (R2)
RN18_4: A6.5, RN18.4 (R3)
RN18_5: A6.7, RN18.5 (R4)
RN18_6: A7.1, RN18.6 (R5)
RN18_7: A7.3, RN18.7 (R6)
RN18_8: A7.5, RN18.8 (R7)
RN18_9: A7.7, RN18.9 (R8)
RN19_2: A8.1, RN19.2 (R1)
RN19_3: A8.3, RN19.3 (R2)
RN19_4: A8.5, RN19.4 (R3)
RN19_5: A8.7, RN19.5 (R4)
RN19_6: A9.1, RN19.6 (R5)
RN19_7: A9.3, RN19.7 (R6)
RN19_8: A9.5, RN19.8 (R7)
RN19_9: A9.7, RN19.9 (R8)
R~W: H7.9 (R/W)
SCR_A15: E4.4 (Za)
SERVICE: A4.8, C11.2, R9.1
UK_SND: A4.6, C10.2, R8.1
UK_SOUND: A3.12 (O5)
ULN_O6: A3.11 (O6)
ULN_O7: A3.10 (O7)
VCAB: C8.1, C9.1, C10.1, C11.1, R6.2, R7.2, R8.2, R9.2, RN17.1 (common), RN18.1 (common), RN19.1 (common), RN20.1 (common)
VCC: D6.16 (VCC), D6.41 (VCC), D6.65 (VCC), D6.91 (VCC), E7.12, RN12.1 (common), RN13.1 (common)
VSS: A3.8 (GND), A4.9, A4.11, A4.13, A4.15, A5.9, A5.11, A5.13, A5.15, A6.9, A6.11, A6.13, A6.15, A7.9, A7.11, A7.13, A7.15, A8.9, A8.11, A8.13, A8.15, A9.9, A9.11, A9.13, A9.15, A11.19 (~CE), CNT8.1, CNT8.7, CNT8.12, CP51.2, D6.15 (VSS), D6.25 (VSS), D6.40 (VSS), D6.45 (VSS), D6.46, D6.47, D6.48, D6.50, D6.56 (VSS), D6.58 (VSS), D6.59 (VSS), D6.66 (VSS), D6.75 (VSS), D6.90 (VSS), E4.15 (E), G11.1 (OEa), G11.19 (OEb), H9.19 (~CE), H11.1 (OEa), H11.19 (OEb), J11.1 (OEa), J11.19 (OEb), K9.19 (~CE), RN12.6 (R5), RN12.7 (R6), RN13.3 (R2), RN13.4 (R3), RN13.5 (R4), RN13.7 (R6), RN13.8 (R7), RN13.9 (R8), SW1.1, SW1.2, SW1.3, SW1.4, SW1.5, SW1.6, SW1.7, SW1.8, SW1.9, SW1.10, SW1.11, SW1.13, SW1.14, SW1.15, SW2.1, SW2.2, SW2.3, SW2.4, SW2.5, SW2.6, SW2.7, SW2.8, SW2.11, SW2.12
WR: H9.1 (A->B), K9.1 (A->B)
~AS: H7.6 (AS)
~BERR: H7.22 (BERR)
~BGACK: H7.12 (BGACK)
~BG: H7.11 (BG)
~BR: H7.13 (BR)
~CLK_CPU: D6.85
~CS1: K11.20 (~CS1), L11.20 (~CS1)
~CS2_IOA: D6.76, K11.26 (~CS2), L11.26 (~CS2)
~DTACK: H7.10 (DTACK)
~HALT: H7.17 (HALT)
~IPL0: H7.25 (IPL0)
~IPL1: H7.24 (IPL1)
~IPL2: H7.23 (IPL2)
~LDS: H7.8 (LDS)
~MR_A: D7.1, F6.1 (~Mr)
~OE_IO: D6.82, K11.22 (~OE), L11.22 (~OE)
~RESET_CPU: D7.3
~RESET: H7.18 (RESET)
~UDS: H7.7 (UDS)
~VPA: H7.21 (VPA)
~WE_IOA: D6.83, F7.2, L11.27 (~WE)
~WE_MAPPER: K11.27 (~WE)
