jotego/jts16/cores/s18/sch/memorymapper.kicad_sch

## KiCad design cores/s18/sch/memorymapper.kicad_sch (2022-12-19)

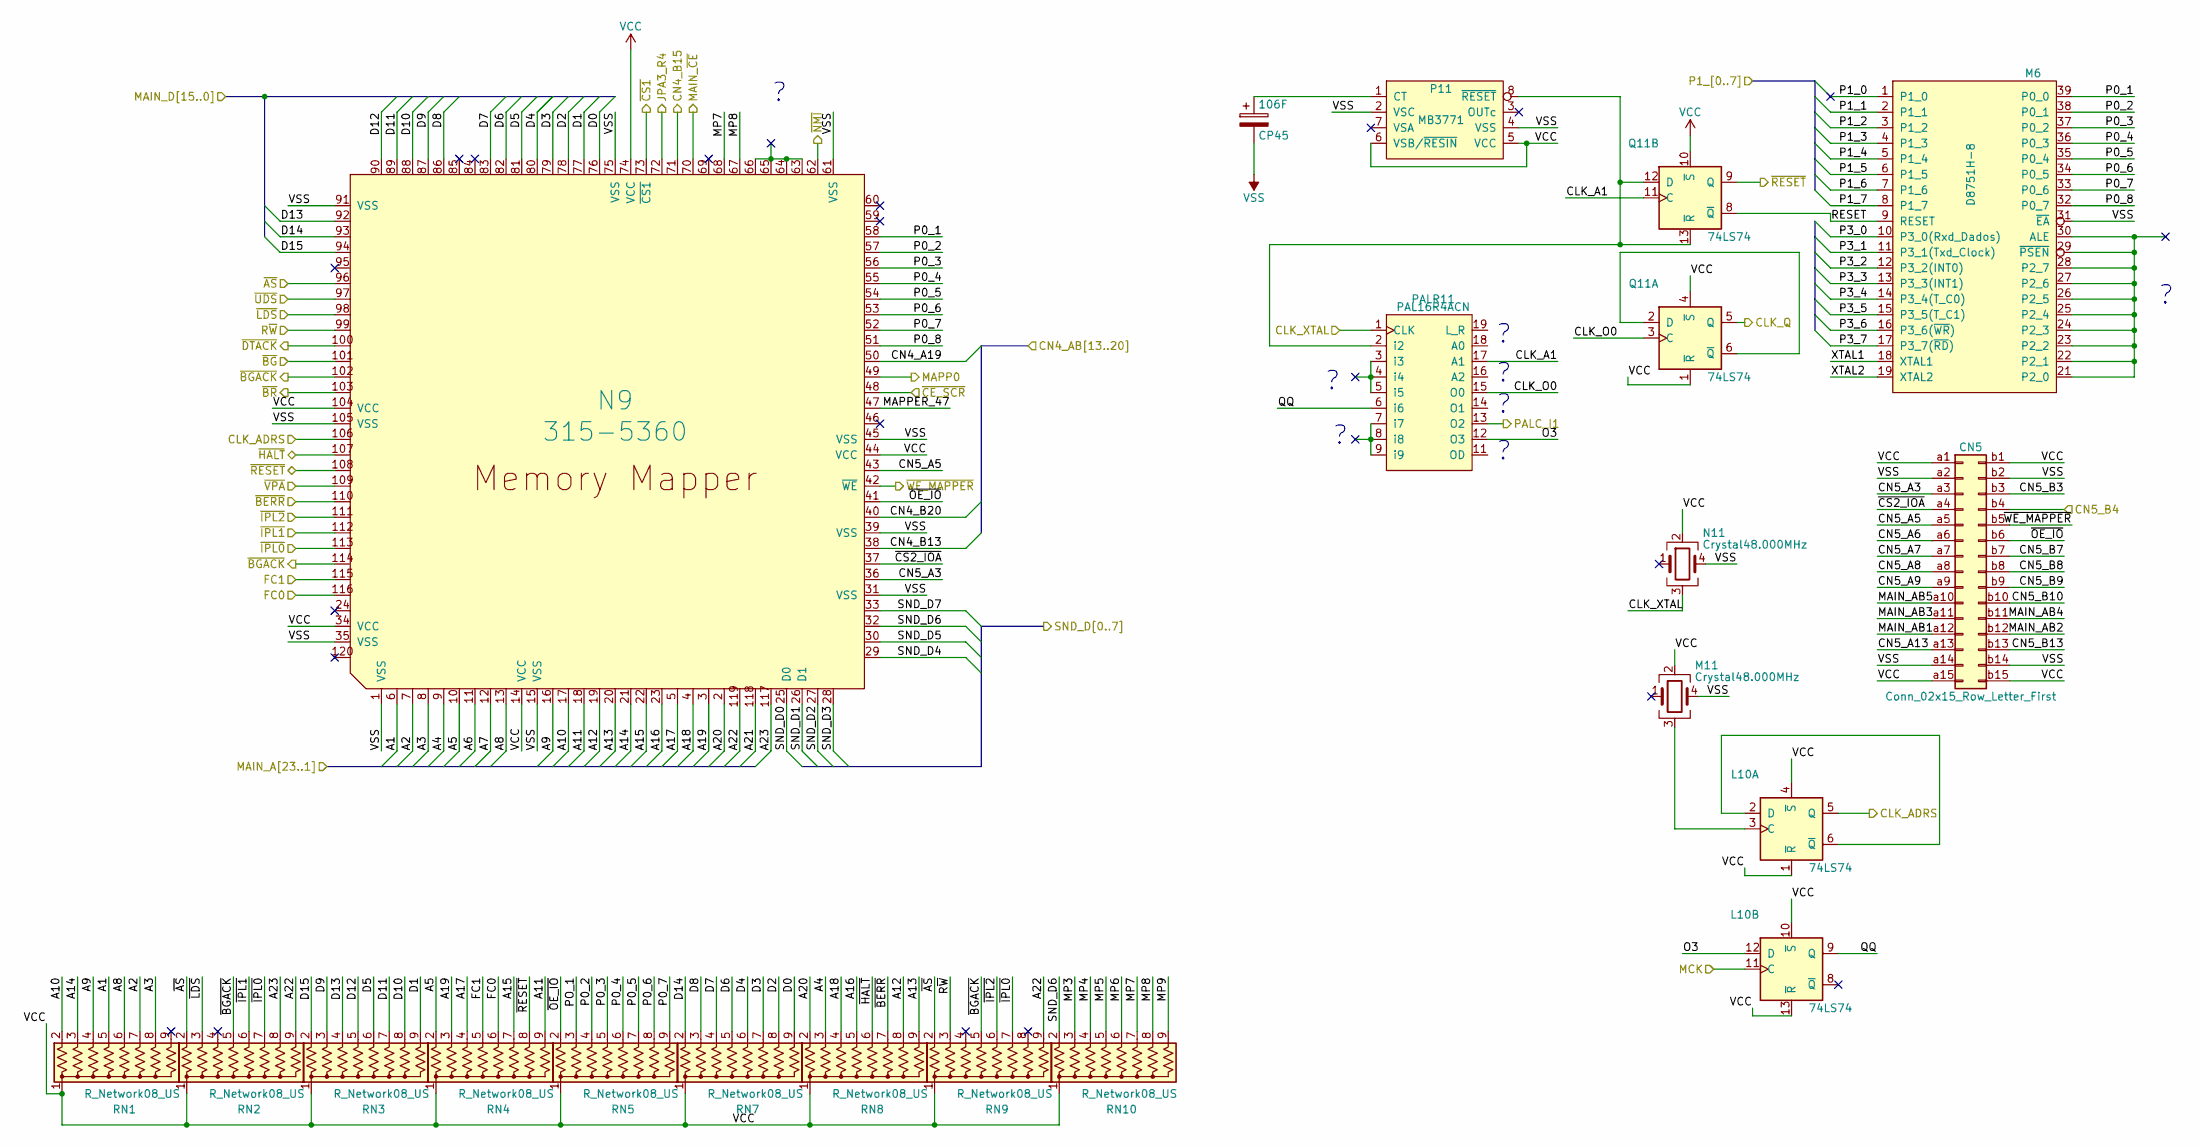
[picture p44: schematic memorymapper.kicad_sch]

Parts:
106F: CP45
CN5: Conn_02x15_Row_Letter_First
L10: 74LS74
M6: D8751H-8
M11: Crystal48.000MHz
N9: 315-5360
N11: Crystal48.000MHz
P11: MB3771
PALR11: PAL16R4ACN
Q11: 74LS74
RN1, RN2, RN3, RN4, RN5, RN7, RN8, RN9, RN10: R_Network08_US; R_Array_SIP9

Connections:
A1: N9.6, RN1.5 (R4)
A2: N9.7, RN1.7 (R6)
A3: N9.8, RN1.8 (R7)
A4: N9.9, RN8.3 (R2)
A5: N9.10, RN4.2 (R1)
A6: N9.11
A7: N9.12
A8: N9.13, RN1.6 (R5)
A9: N9.16, RN1.4 (R3)
A10: N9.17, RN1.2 (R1)
A11: N9.18, RN4.9 (R8)
A12: N9.19, RN8.8 (R7)
A13: N9.20, RN8.9 (R8)
A14: N9.21, RN1.3 (R2)
A15: N9.22, RN4.7 (R6)
A16: N9.23, RN8.5 (R4)
A17: N9.5, RN4.4 (R3)
A18: N9.4, RN8.4 (R3)
A19: N9.3, RN4.3 (R2)
A20: N9.2, RN8.2 (R1)
A21: N9.118
A22: N9.119, RN2.9 (R8), RN9.9 (R8)
A23: N9.117, RN2.8 (R7)
CLK_A1: PALR11.17 (A1), Q11.11 (C)
CLK_ADRS: L10.5 (Q), N9.106
CLK_O0: PALR11.15 (O0), Q11.3 (C)
CLK_Q: Q11.5 (Q)
CLK_XTAL: N11.3, PALR11.1 (CLK)
CN4_A19: N9.50
CN4_B13: N9.38
CN4_B15: N9.71
CN4_B20: N9.40
CN5_A3: CN5.a3, N9.36
CN5_A5: CN5.a5, N9.43
CN5_A6: CN5.a6
CN5_A7: CN5.a7
CN5_A8: CN5.a8
CN5_A9: CN5.a9
CN5_A13: CN5.a13
CN5_B3: CN5.b3
CN5_B4: CN5.b4
CN5_B7: CN5.b7
CN5_B8: CN5.b8
CN5_B9: CN5.b9
CN5_B10: CN5.b10
CN5_B13: CN5.b13
D0: N9.76, RN7.9 (R8)
D1: N9.77, RN3.9 (R8)
D2: N9.78, RN7.8 (R7)
D3: N9.79, RN7.7 (R6)
D4: N9.80, RN7.6 (R5)
D5: N9.81, RN3.6 (R5)
D6: N9.82, RN7.5 (R4)
D7: N9.83, RN7.4 (R3)
D8: N9.86, RN7.3 (R2)
D9: N9.87, RN3.3 (R2)
D10: N9.88, RN3.8 (R7)
D11: N9.89, RN3.7 (R6)
D12: N9.90, RN3.5 (R4)
D13: N9.92, RN3.4 (R3)
D14: N9.93, RN7.2 (R1)
D15: N9.94, RN3.2 (R1)
FC0: N9.116, RN4.6 (R5)
FC1: N9.115, RN4.5 (R4)
JPA3_R4: N9.72
MAIN_AB1: CN5.a12
MAIN_AB2: CN5.b12
MAIN_AB3: CN5.a11
MAIN_AB4: CN5.b11
MAIN_AB5: CN5.a10
MAIN_~CE: N9.70
MAPP0: N9.49
MAPPER_47: N9.47
MCK: L10.11 (C)
MP3: RN10.3 (R2)
MP4: RN10.4 (R3)
MP5: RN10.5 (R4)
MP6: RN10.6 (R5)
MP7: N9.68, RN10.7 (R6)
MP8: N9.67, RN10.8 (R7)
MP9: RN10.9 (R8)
unnamed: 106F.1, P11.1 (CT)
unnamed: L10.2 (D), L10.6 (~Q)
unnamed: L10.3 (C), M11.3
unnamed: M6.21 (P2_0), M6.22 (P2_1), M6.23 (P2_2), M6.24 (P2_3), M6.25 (P2_4), M6.26 (P2_5), M6.27 (P2_6), M6.28 (P2_7), M6.29 (~PSEN), M6.30 (ALE)
unnamed: N9.63, N9.64, N9.65, N9.66
unnamed: P11.8 (~RESET), PALR11.2 (i2), Q11.12 (D), Q11.13 (~R)
unnamed: PALR11.3 (i3), PALR11.4 (i4), PALR11.5 (i5)
unnamed: PALR11.7 (i7), PALR11.8 (i8), PALR11.9 (i9)
unnamed: Q11.2 (D), Q11.6 (~Q)
O3: L10.12 (D), PALR11.12 (O3)
P0_1: M6.39 (P0_0), N9.58
P0_2: M6.38 (P0_1), N9.57, RN5.4 (R3)
P0_3: M6.37 (P0_2), N9.56, RN5.5 (R4)
P0_4: M6.36 (P0_3), N9.55, RN5.6 (R5)
P0_5: M6.35 (P0_4), N9.54, RN5.7 (R6)
P0_6: M6.34 (P0_5), N9.53, RN5.8 (R7)
P0_7: M6.33 (P0_6), N9.52, RN5.9 (R8)
P0_8: M6.32 (P0_7), N9.51
P1_0: M6.1 (P1_0)
P1_1: M6.2 (P1_1)
P1_2: M6.3 (P1_2)
P1_3: M6.4 (P1_3)
P1_4: M6.5 (P1_4)
P1_5: M6.6 (P1_5)
P1_6: M6.7 (P1_6)
P1_7: M6.8 (P1_7)
P3_0: M6.10 (P3_0(Rxd_Dados))
P3_1: M6.11 (P3_1(Txd_Clock))
P3_2: M6.12 (P3_2(INT0))
P3_3: M6.13 (P3_3(INT1))
P3_4: M6.14 (P3_4(T_C0))
P3_5: M6.15 (P3_5(T_C1))
P3_6: M6.16 (P3_6(~WR))
P3_7: M6.17 (P3_7(~RD))
PALC_I1: PALR11.13 (O2)
PO_1: RN5.3 (R2)
QQ: L10.9 (Q), PALR11.6 (i6)
RESET: M6.9 (RESET), Q11.8 (~Q)
R~W: N9.99, RN9.3 (R2)
SND_D0: N9.25 (D0)
SND_D1: N9.26 (D1)
SND_D2: N9.27
SND_D3: N9.28
SND_D4: N9.29
SND_D5: N9.30
SND_D6: N9.32, RN10.2 (R1)
SND_D7: N9.33
VCC: CN5.a1, CN5.a15, CN5.b1, CN5.b15, L10.1 (~R), L10.4 (~S), L10.10 (~S), L10.13 (~R), M11.2, N9.14 (VCC), N9.34 (VCC), N9.44 (VCC), N9.104 (VCC), N11.2, P11.5 (VCC), P11.6 (VSB/~RESIN), Q11.1 (~R), Q11.4 (~S), RN1.1 (common), RN2.1 (common), RN3.1 (common), RN4.1 (common), RN5.1 (common), RN7.1 (common), RN8.1 (common), RN9.1 (common), RN10.1 (common)
VSS: CN5.a2, CN5.a14, CN5.b2, CN5.b14, M6.31 (~EA), M11.4, N9.1 (VSS), N9.15 (VSS), N9.31 (VSS), N9.35 (VSS), N9.39 (VSS), N9.45 (VSS), N9.61 (VSS), N9.75 (VSS), N9.91 (VSS), N9.105 (VSS), N11.4, P11.2 (VSC), P11.4 (VSS)
XTAL1: M6.18 (XTAL1)
XTAL2: M6.19 (XTAL2)
~AS: N9.96, RN2.2 (R1), RN9.2 (R1)
~BERR: N9.110, RN8.7 (R6)
~BGACK: N9.102, N9.114, RN2.5 (R4), RN9.5 (R4)
~BG: N9.101
~BR: N9.103
~CE_SCR: N9.48
~CS1: N9.73 (~CS1)
~CS2_IOA: CN5.a4, N9.37
~DTACK: N9.100
~HALT: N9.107, RN8.6 (R5)
~IPL0: N9.113, RN2.7 (R6), RN9.7 (R6)
~IPL1: N9.112, RN2.6 (R5)
~IPL2: N9.111, RN9.6 (R5)
~LDS: N9.98, RN2.3 (R2)
~NMI: N9.62
~OE_IO: CN5.b6, N9.41, RN5.2 (R1)
~RESET: N9.108, Q11.9 (Q), RN4.8 (R7)
~UDS: N9.97
~VPA: N9.109
~WE_MAPPER: CN5.b5, N9.42 (~WE)
