jotego/jts16/cores/s18/sch/objrom.kicad_sch

## KiCad design cores/s18/sch/objrom.kicad_sch (2022-12-19)

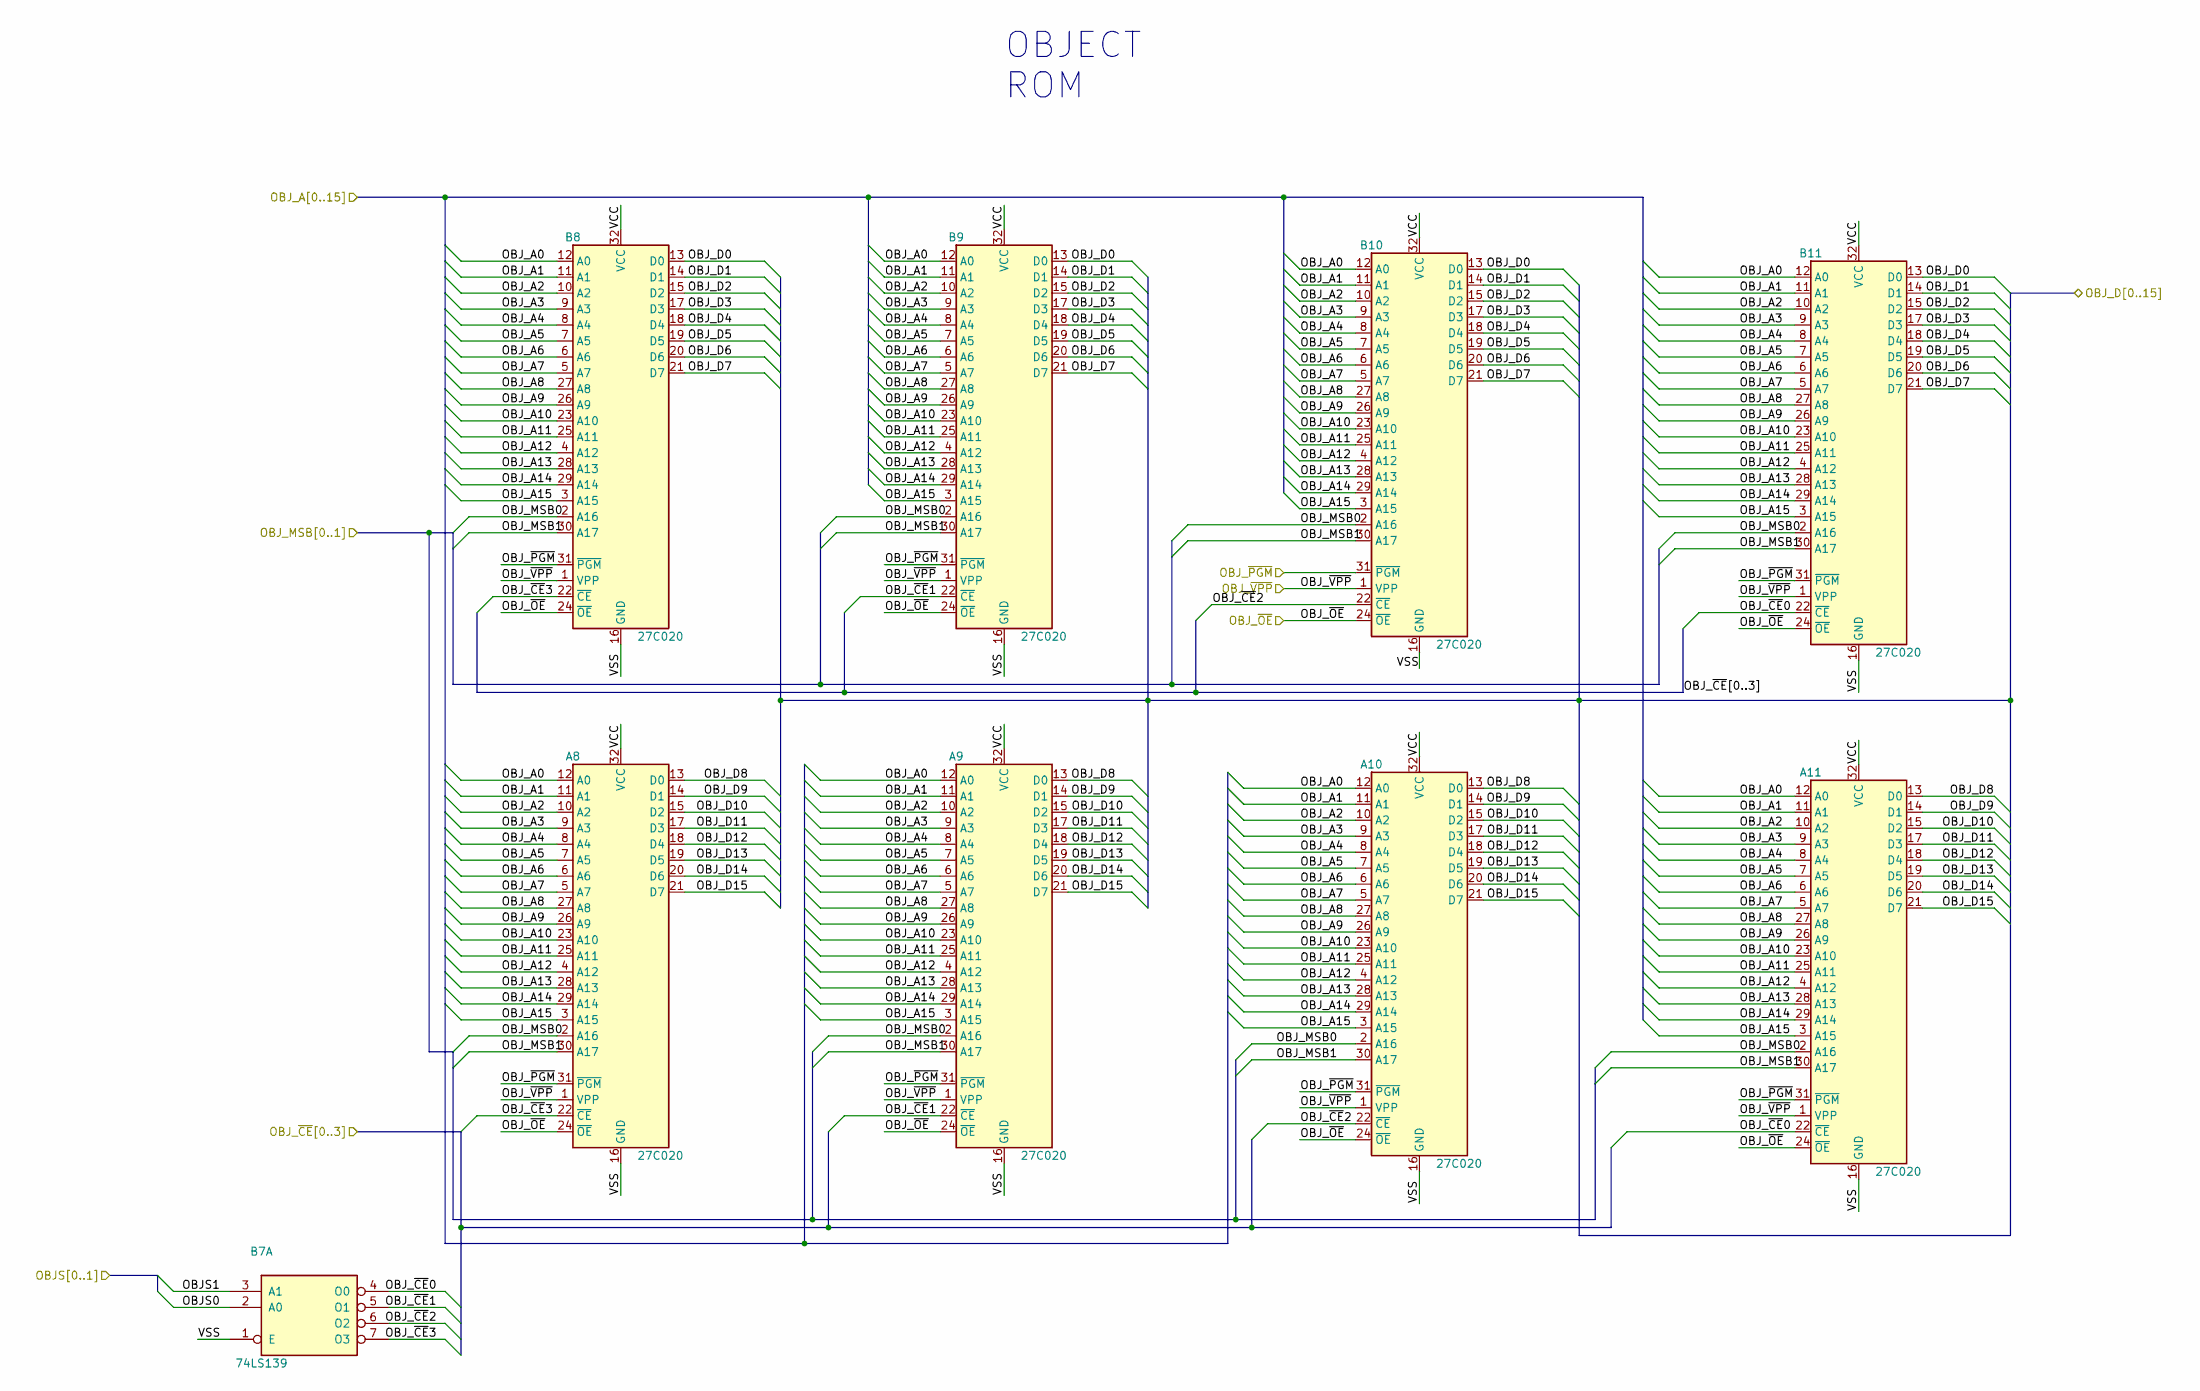
[picture p45: schematic objrom.kicad_sch]

Parts:
A8, A9, A10, A11: 27C020
B7: 74LS139
B8, B9, B10, B11: 27C020

Connections:
OBJS0: B7.2 (A0)
OBJS1: B7.3 (A1)
OBJ_A0: A8.12 (A0), A9.12 (A0), A10.12 (A0), A11.12 (A0), B8.12 (A0), B9.12 (A0), B10.12 (A0), B11.12 (A0)
OBJ_A1: A8.11 (A1), A9.11 (A1), A10.11 (A1), A11.11 (A1), B8.11 (A1), B9.11 (A1), B10.11 (A1), B11.11 (A1)
OBJ_A2: A8.10 (A2), A9.10 (A2), A10.10 (A2), A11.10 (A2), B8.10 (A2), B9.10 (A2), B10.10 (A2), B11.10 (A2)
OBJ_A3: A8.9 (A3), A9.9 (A3), A10.9 (A3), A11.9 (A3), B8.9 (A3), B9.9 (A3), B10.9 (A3), B11.9 (A3)
OBJ_A4: A8.8 (A4), A9.8 (A4), A10.8 (A4), A11.8 (A4), B8.8 (A4), B9.8 (A4), B10.8 (A4), B11.8 (A4)
OBJ_A5: A8.7 (A5), A9.7 (A5), A10.7 (A5), A11.7 (A5), B8.7 (A5), B9.7 (A5), B10.7 (A5), B11.7 (A5)
OBJ_A6: A8.6 (A6), A9.6 (A6), A10.6 (A6), A11.6 (A6), B8.6 (A6), B9.6 (A6), B10.6 (A6), B11.6 (A6)
OBJ_A7: A8.5 (A7), A9.5 (A7), A10.5 (A7), A11.5 (A7), B8.5 (A7), B9.5 (A7), B10.5 (A7), B11.5 (A7)
OBJ_A8: A8.27 (A8), A9.27 (A8), A10.27 (A8), A11.27 (A8), B8.27 (A8), B9.27 (A8), B10.27 (A8), B11.27 (A8)
OBJ_A9: A8.26 (A9), A9.26 (A9), A10.26 (A9), A11.26 (A9), B8.26 (A9), B9.26 (A9), B10.26 (A9), B11.26 (A9)
OBJ_A10: A8.23 (A10), A9.23 (A10), A10.23 (A10), A11.23 (A10), B8.23 (A10), B9.23 (A10), B10.23 (A10), B11.23 (A10)
OBJ_A11: A8.25 (A11), A9.25 (A11), A10.25 (A11), A11.25 (A11), B8.25 (A11), B9.25 (A11), B10.25 (A11), B11.25 (A11)
OBJ_A12: A8.4 (A12), A9.4 (A12), A10.4 (A12), A11.4 (A12), B8.4 (A12), B9.4 (A12), B10.4 (A12), B11.4 (A12)
OBJ_A13: A8.28 (A13), A9.28 (A13), A10.28 (A13), A11.28 (A13), B8.28 (A13), B9.28 (A13), B10.28 (A13), B11.28 (A13)
OBJ_A14: A8.29 (A14), A9.29 (A14), A10.29 (A14), A11.29 (A14), B8.29 (A14), B9.29 (A14), B10.29 (A14), B11.29 (A14)
OBJ_A15: A8.3 (A15), A9.3 (A15), A10.3 (A15), A11.3 (A15), B8.3 (A15), B9.3 (A15), B10.3 (A15), B11.3 (A15)
OBJ_D0: B8.13 (D0), B9.13 (D0), B10.13 (D0), B11.13 (D0)
OBJ_D1: B8.14 (D1), B9.14 (D1), B10.14 (D1), B11.14 (D1)
OBJ_D2: B8.15 (D2), B9.15 (D2), B10.15 (D2), B11.15 (D2)
OBJ_D3: B8.17 (D3), B9.17 (D3), B10.17 (D3), B11.17 (D3)
OBJ_D4: B8.18 (D4), B9.18 (D4), B10.18 (D4), B11.18 (D4)
OBJ_D5: B8.19 (D5), B9.19 (D5), B10.19 (D5), B11.19 (D5)
OBJ_D6: B8.20 (D6), B9.20 (D6), B10.20 (D6), B11.20 (D6)
OBJ_D7: B8.21 (D7), B9.21 (D7), B10.21 (D7), B11.21 (D7)
OBJ_D8: A8.13 (D0), A9.13 (D0), A10.13 (D0), A11.13 (D0)
OBJ_D9: A8.14 (D1), A9.14 (D1), A10.14 (D1), A11.14 (D1)
OBJ_D10: A8.15 (D2), A9.15 (D2), A10.15 (D2), A11.15 (D2)
OBJ_D11: A8.17 (D3), A9.17 (D3), A10.17 (D3), A11.17 (D3)
OBJ_D12: A8.18 (D4), A9.18 (D4), A10.18 (D4), A11.18 (D4)
OBJ_D13: A8.19 (D5), A9.19 (D5), A10.19 (D5), A11.19 (D5)
OBJ_D14: A8.20 (D6), A9.20 (D6), A10.20 (D6), A11.20 (D6)
OBJ_D15: A8.21 (D7), A9.21 (D7), A10.21 (D7), A11.21 (D7)
OBJ_MSB0: A8.2 (A16), A9.2 (A16), A10.2 (A16), A11.2 (A16), B8.2 (A16), B9.2 (A16), B10.2 (A16), B11.2 (A16)
OBJ_MSB1: A8.30 (A17), A9.30 (A17), A10.30 (A17), A11.30 (A17), B8.30 (A17), B9.30 (A17), B10.30 (A17), B11.30 (A17)
OBJ_~CE0: A11.22 (~CE), B7.4 (O0), B11.22 (~CE)
OBJ_~CE1: A9.22 (~CE), B7.5 (O1), B9.22 (~CE)
OBJ_~CE2: A10.22 (~CE), B7.6 (O2), B10.22 (~CE)
OBJ_~CE3: A8.22 (~CE), B7.7 (O3), B8.22 (~CE)
OBJ_~OE: A8.24 (~OE), A9.24 (~OE), A10.24 (~OE), A11.24 (~OE), B8.24 (~OE), B9.24 (~OE), B10.24 (~OE), B11.24 (~OE)
OBJ_~PGM: A8.31 (~PGM), A9.31 (~PGM), A10.31 (~PGM), A11.31 (~PGM), B8.31 (~PGM), B9.31 (~PGM), B10.31 (~PGM), B11.31 (~PGM)
OBJ_~VPP: A8.1 (VPP), A9.1 (VPP), A10.1 (VPP), A11.1 (VPP), B8.1 (VPP), B9.1 (VPP), B10.1 (VPP), B11.1 (VPP)
VCC: A8.32 (VCC), A9.32 (VCC), A10.32 (VCC), A11.32 (VCC), B8.32 (VCC), B9.32 (VCC), B10.32 (VCC), B11.32 (VCC)
VSS: A8.16 (GND), A9.16 (GND), A10.16 (GND), A11.16 (GND), B7.1 (E), B8.16 (GND), B9.16 (GND), B10.16 (GND), B11.16 (GND)

Notes on the sheet:
OBJECT ROM
