jotego/jts16/cores/s18/sch/romboard.kicad_sch

## KiCad design cores/s18/sch/romboard.kicad_sch (2022-12-19)

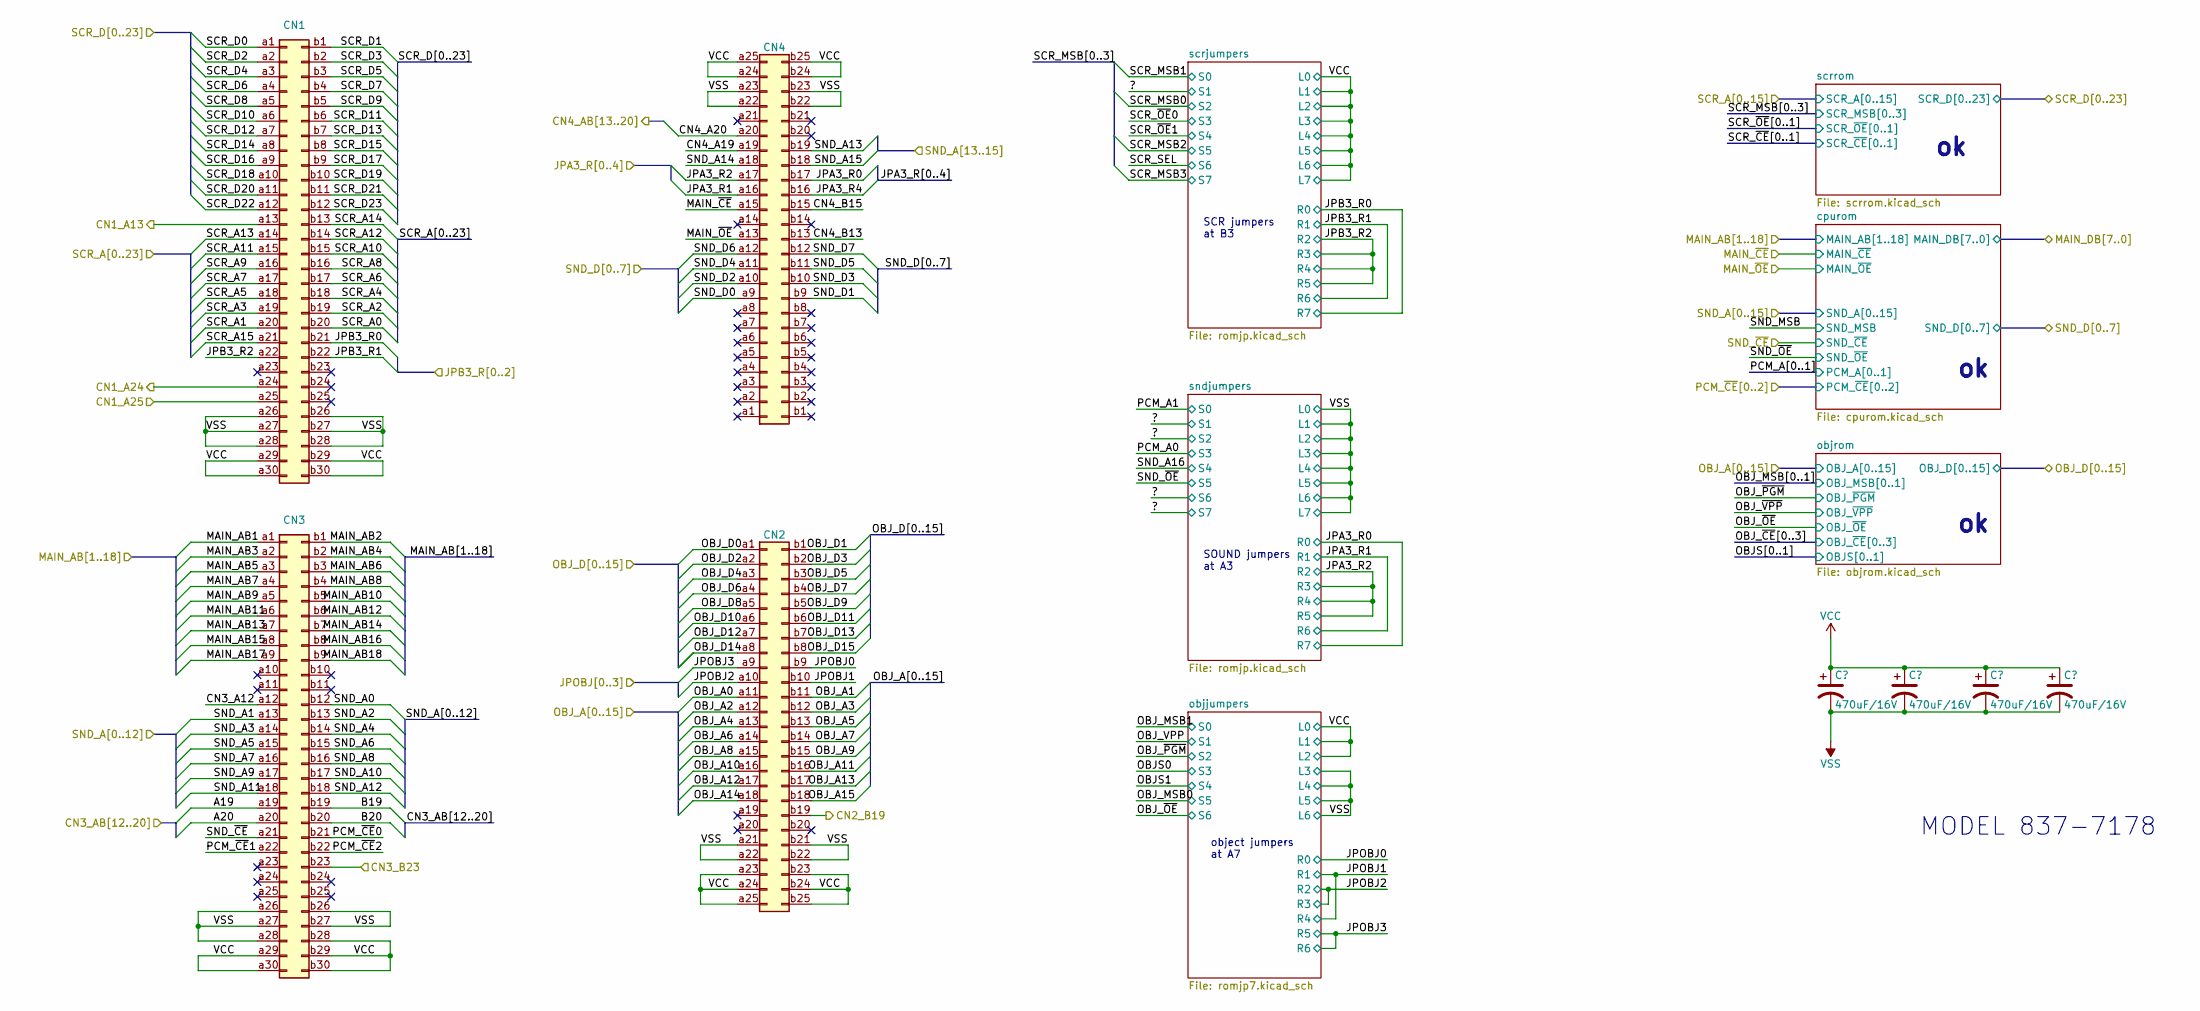
[picture p46: schematic romboard.kicad_sch]

Parts:
CN1, CN3: Conn_02x30_Row_Letter_First
CN2, CN4: Conn_02x25_Row_Letter_First

Connections:
A19: CN3.a19
A20: CN3.a20
B19: CN3.b19
B20: CN3.b20
CN1_A13: CN1.a13
CN1_A24: CN1.a24
CN1_A25: CN1.a25
CN2_B19: CN2.b19
CN3_A12: CN3.a12
CN3_B23: CN3.b23
CN4_A19: CN4.a19
CN4_A20: CN4.a20
CN4_B13: CN4.b13
CN4_B15: CN4.b15
JPA3_R0: CN4.b17
JPA3_R1: CN4.a16
JPA3_R2: CN4.a17
JPA3_R4: CN4.b16
JPB3_R0: CN1.b21
JPB3_R1: CN1.b22
JPB3_R2: CN1.a22
JPOBJ0: CN2.b9
JPOBJ1: CN2.b10
JPOBJ2: CN2.a10
JPOBJ3: CN2.a9
MAIN_AB1: CN3.a1
MAIN_AB2: CN3.b1
MAIN_AB3: CN3.a2
MAIN_AB4: CN3.b2
MAIN_AB5: CN3.a3
MAIN_AB6: CN3.b3
MAIN_AB7: CN3.a4
MAIN_AB8: CN3.b4
MAIN_AB9: CN3.a5
MAIN_AB10: CN3.b5
MAIN_AB11: CN3.a6
MAIN_AB12: CN3.b6
MAIN_AB13: CN3.a7
MAIN_AB14: CN3.b7
MAIN_AB15: CN3.a8
MAIN_AB16: CN3.b8
MAIN_AB17: CN3.a9
MAIN_AB18: CN3.b9
MAIN_~CE: CN4.a15
MAIN_~OE: CN4.a13
OBJ_A0: CN2.a11
OBJ_A1: CN2.b11
OBJ_A2: CN2.a12
OBJ_A3: CN2.b12
OBJ_A4: CN2.a13
OBJ_A5: CN2.b13
OBJ_A6: CN2.a14
OBJ_A7: CN2.b14
OBJ_A8: CN2.a15
OBJ_A9: CN2.b15
OBJ_A10: CN2.a16
OBJ_A11: CN2.b16
OBJ_A12: CN2.a17
OBJ_A13: CN2.b17
OBJ_A14: CN2.a18
OBJ_A15: CN2.b18
OBJ_D0: CN2.a1
OBJ_D1: CN2.b1
OBJ_D2: CN2.a2
OBJ_D3: CN2.b2
OBJ_D4: CN2.a3
OBJ_D5: CN2.b3
OBJ_D6: CN2.a4
OBJ_D7: CN2.b4
OBJ_D8: CN2.a5
OBJ_D9: CN2.b5
OBJ_D10: CN2.a6
OBJ_D11: CN2.b6
OBJ_D12: CN2.a7
OBJ_D13: CN2.b7
OBJ_D14: CN2.a8
OBJ_D15: CN2.b8
PCM_~CE0: CN3.b21
PCM_~CE1: CN3.a22
PCM_~CE2: CN3.b22
SCR_A0: CN1.b20
SCR_A1: CN1.a20
SCR_A2: CN1.b19
SCR_A3: CN1.a19
SCR_A4: CN1.b18
SCR_A5: CN1.a18
SCR_A6: CN1.b17
SCR_A7: CN1.a17
SCR_A8: CN1.b16
SCR_A9: CN1.a16
SCR_A10: CN1.b15
SCR_A11: CN1.a15
SCR_A12: CN1.b14
SCR_A13: CN1.a14
SCR_A14: CN1.b13
SCR_A15: CN1.a21
SCR_D0: CN1.a1
SCR_D1: CN1.b1
SCR_D2: CN1.a2
SCR_D3: CN1.b2
SCR_D4: CN1.a3
SCR_D5: CN1.b3
SCR_D6: CN1.a4
SCR_D7: CN1.b4
SCR_D8: CN1.a5
SCR_D9: CN1.b5
SCR_D10: CN1.a6
SCR_D11: CN1.b6
SCR_D12: CN1.a7
SCR_D13: CN1.b7
SCR_D14: CN1.a8
SCR_D15: CN1.b8
SCR_D16: CN1.a9
SCR_D17: CN1.b9
SCR_D18: CN1.a10
SCR_D19: CN1.b10
SCR_D20: CN1.a11
SCR_D21: CN1.b11
SCR_D22: CN1.a12
SCR_D23: CN1.b12
SND_A0: CN3.b12
SND_A1: CN3.a13
SND_A2: CN3.b13
SND_A3: CN3.a14
SND_A4: CN3.b14
SND_A5: CN3.a15
SND_A6: CN3.b15
SND_A7: CN3.a16
SND_A8: CN3.b16
SND_A9: CN3.a17
SND_A10: CN3.b17
SND_A11: CN3.a18
SND_A12: CN3.b18
SND_A13: CN4.b19
SND_A14: CN4.a18
SND_A15: CN4.b18
SND_D0: CN4.a9
SND_D1: CN4.b9
SND_D2: CN4.a10
SND_D3: CN4.b10
SND_D4: CN4.a11
SND_D5: CN4.b11
SND_D6: CN4.a12
SND_D7: CN4.b12
SND_~CE: CN3.a21
VCC: CN1.a29, CN1.a30, CN1.b29, CN1.b30, CN2.a23, CN2.a24, CN2.a25, CN2.b23, CN2.b24, CN2.b25, CN3.a29, CN3.a30, CN3.b28, CN3.b29, CN3.b30, CN4.a24, CN4.a25, CN4.b24, CN4.b25
VSS: CN1.a26, CN1.a27, CN1.a28, CN1.b26, CN1.b27, CN1.b28, CN2.a21, CN2.a22, CN2.b21, CN2.b22, CN3.a26, CN3.a27, CN3.a28, CN3.b26, CN3.b27, CN4.a22, CN4.a23, CN4.b22, CN4.b23

Notes on the sheet:
object jumpers at A7
SCR jumpers at B3
MODEL 837-7178
SOUND jumpers at A3
