jotego/jts16/cores/s18/sch/scrrom.kicad_sch

## KiCad design cores/s18/sch/scrrom.kicad_sch (2022-12-19)

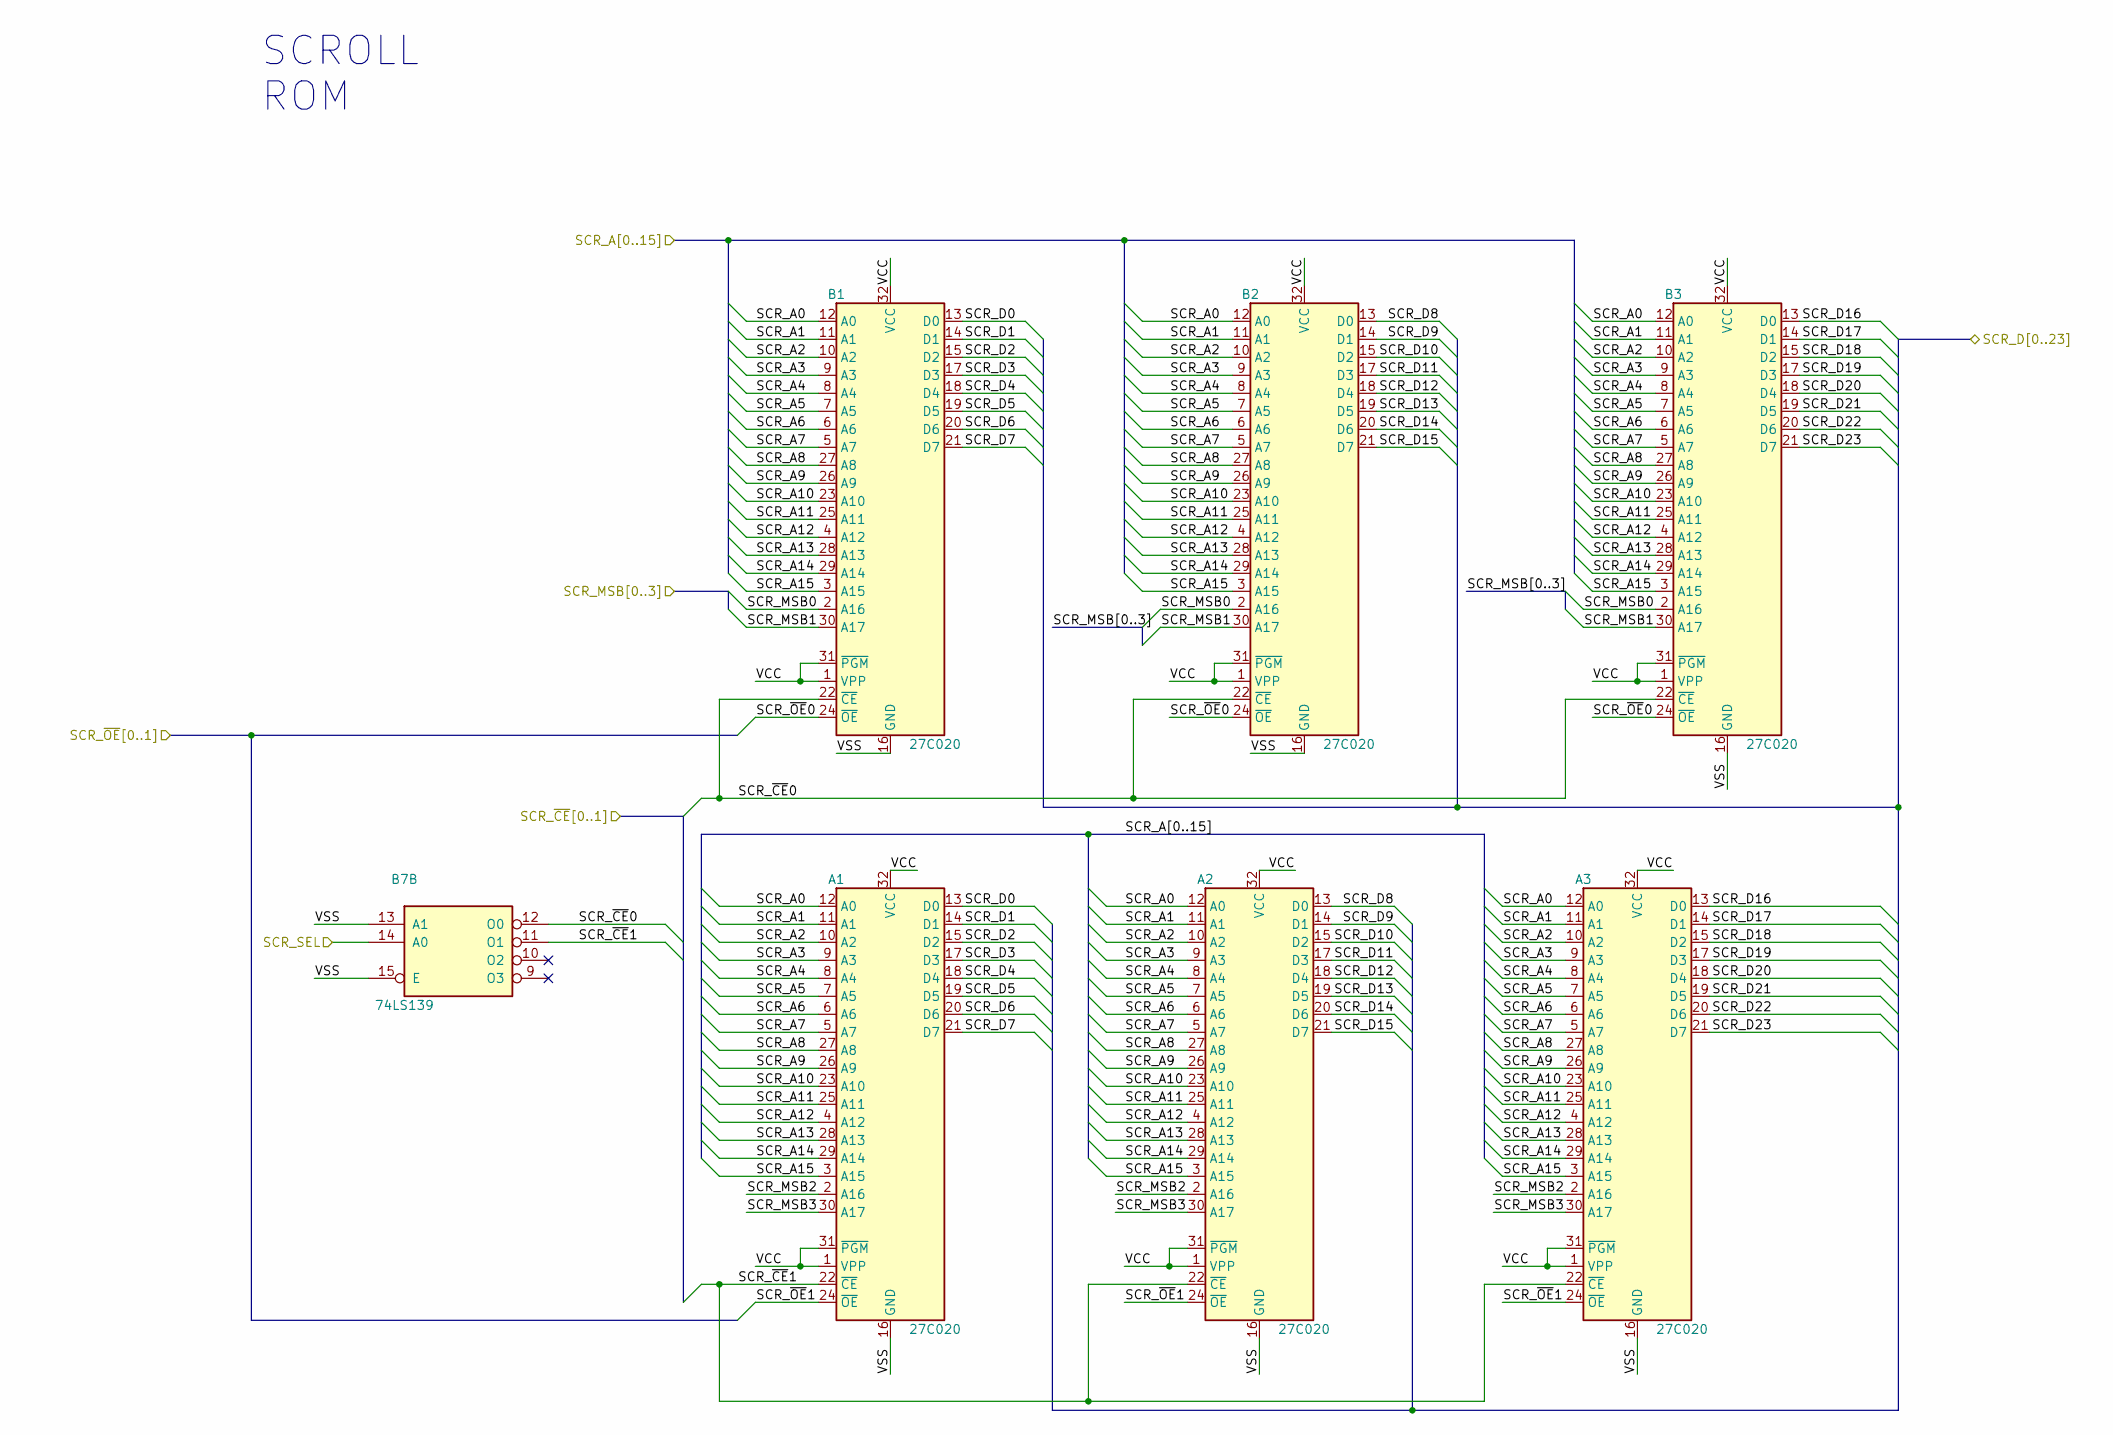
[picture p47: schematic scrrom.kicad_sch]

Parts:
A1, A2, A3: 27C020
B1, B2, B3: 27C020
B7: 74LS139

Connections:
SCR_A0: A1.12 (A0), A2.12 (A0), A3.12 (A0), B1.12 (A0), B2.12 (A0), B3.12 (A0)
SCR_A1: A1.11 (A1), A2.11 (A1), A3.11 (A1), B1.11 (A1), B2.11 (A1), B3.11 (A1)
SCR_A2: A1.10 (A2), A2.10 (A2), A3.10 (A2), B1.10 (A2), B2.10 (A2), B3.10 (A2)
SCR_A3: A1.9 (A3), A2.9 (A3), A3.9 (A3), B1.9 (A3), B2.9 (A3), B3.9 (A3)
SCR_A4: A1.8 (A4), A2.8 (A4), A3.8 (A4), B1.8 (A4), B2.8 (A4), B3.8 (A4)
SCR_A5: A1.7 (A5), A2.7 (A5), A3.7 (A5), B1.7 (A5), B2.7 (A5), B3.7 (A5)
SCR_A6: A1.6 (A6), A2.6 (A6), A3.6 (A6), B1.6 (A6), B2.6 (A6), B3.6 (A6)
SCR_A7: A1.5 (A7), A2.5 (A7), A3.5 (A7), B1.5 (A7), B2.5 (A7), B3.5 (A7)
SCR_A8: A1.27 (A8), A2.27 (A8), A3.27 (A8), B1.27 (A8), B2.27 (A8), B3.27 (A8)
SCR_A9: A1.26 (A9), A2.26 (A9), A3.26 (A9), B1.26 (A9), B2.26 (A9), B3.26 (A9)
SCR_A10: A1.23 (A10), A2.23 (A10), A3.23 (A10), B1.23 (A10), B2.23 (A10), B3.23 (A10)
SCR_A11: A1.25 (A11), A2.25 (A11), A3.25 (A11), B1.25 (A11), B2.25 (A11), B3.25 (A11)
SCR_A12: A1.4 (A12), A2.4 (A12), A3.4 (A12), B1.4 (A12), B2.4 (A12), B3.4 (A12)
SCR_A13: A1.28 (A13), A2.28 (A13), A3.28 (A13), B1.28 (A13), B2.28 (A13), B3.28 (A13)
SCR_A14: A1.29 (A14), A2.29 (A14), A3.29 (A14), B1.29 (A14), B2.29 (A14), B3.29 (A14)
SCR_A15: A1.3 (A15), A2.3 (A15), A3.3 (A15), B1.3 (A15), B2.3 (A15), B3.3 (A15)
SCR_D0: A1.13 (D0), B1.13 (D0)
SCR_D1: A1.14 (D1), B1.14 (D1)
SCR_D2: A1.15 (D2), B1.15 (D2)
SCR_D3: A1.17 (D3), B1.17 (D3)
SCR_D4: A1.18 (D4), B1.18 (D4)
SCR_D5: A1.19 (D5), B1.19 (D5)
SCR_D6: A1.20 (D6), B1.20 (D6)
SCR_D7: A1.21 (D7), B1.21 (D7)
SCR_D8: A2.13 (D0), B2.13 (D0)
SCR_D9: A2.14 (D1), B2.14 (D1)
SCR_D10: A2.15 (D2), B2.15 (D2)
SCR_D11: A2.17 (D3), B2.17 (D3)
SCR_D12: A2.18 (D4), B2.18 (D4)
SCR_D13: A2.19 (D5), B2.19 (D5)
SCR_D14: A2.20 (D6), B2.20 (D6)
SCR_D15: A2.21 (D7), B2.21 (D7)
SCR_D16: A3.13 (D0), B3.13 (D0)
SCR_D17: A3.14 (D1), B3.14 (D1)
SCR_D18: A3.15 (D2), B3.15 (D2)
SCR_D19: A3.17 (D3), B3.17 (D3)
SCR_D20: A3.18 (D4), B3.18 (D4)
SCR_D21: A3.19 (D5), B3.19 (D5)
SCR_D22: A3.20 (D6), B3.20 (D6)
SCR_D23: A3.21 (D7), B3.21 (D7)
SCR_MSB0: B1.2 (A16), B2.2 (A16), B3.2 (A16)
SCR_MSB1: B1.30 (A17), B2.30 (A17), B3.30 (A17)
SCR_MSB2: A1.2 (A16), A2.2 (A16), A3.2 (A16)
SCR_MSB3: A1.30 (A17), A2.30 (A17), A3.30 (A17)
SCR_SEL: B7.14 (A0)
SCR_~CE0: B1.22 (~CE), B2.22 (~CE), B3.22 (~CE), B7.12 (O0)
SCR_~CE1: A1.22 (~CE), A2.22 (~CE), A3.22 (~CE), B7.11 (O1)
SCR_~OE0: B1.24 (~OE), B2.24 (~OE), B3.24 (~OE)
SCR_~OE1: A1.24 (~OE), A2.24 (~OE), A3.24 (~OE)
VCC: A1.1 (VPP), A1.31 (~PGM), A1.32 (VCC), A2.1 (VPP), A2.31 (~PGM), A2.32 (VCC), A3.1 (VPP), A3.31 (~PGM), A3.32 (VCC), B1.1 (VPP), B1.31 (~PGM), B1.32 (VCC), B2.1 (VPP), B2.31 (~PGM), B2.32 (VCC), B3.1 (VPP), B3.31 (~PGM), B3.32 (VCC)
VSS: A1.16 (GND), A2.16 (GND), A3.16 (GND), B1.16 (GND), B2.16 (GND), B3.16 (GND), B7.13 (A1), B7.15 (E)

Notes on the sheet:
SCROLL ROM
