jotego/jts16/cores/s18/sch/sound_a.kicad_sch

## KiCad design cores/s18/sch/sound_a.kicad_sch (2022-12-19)

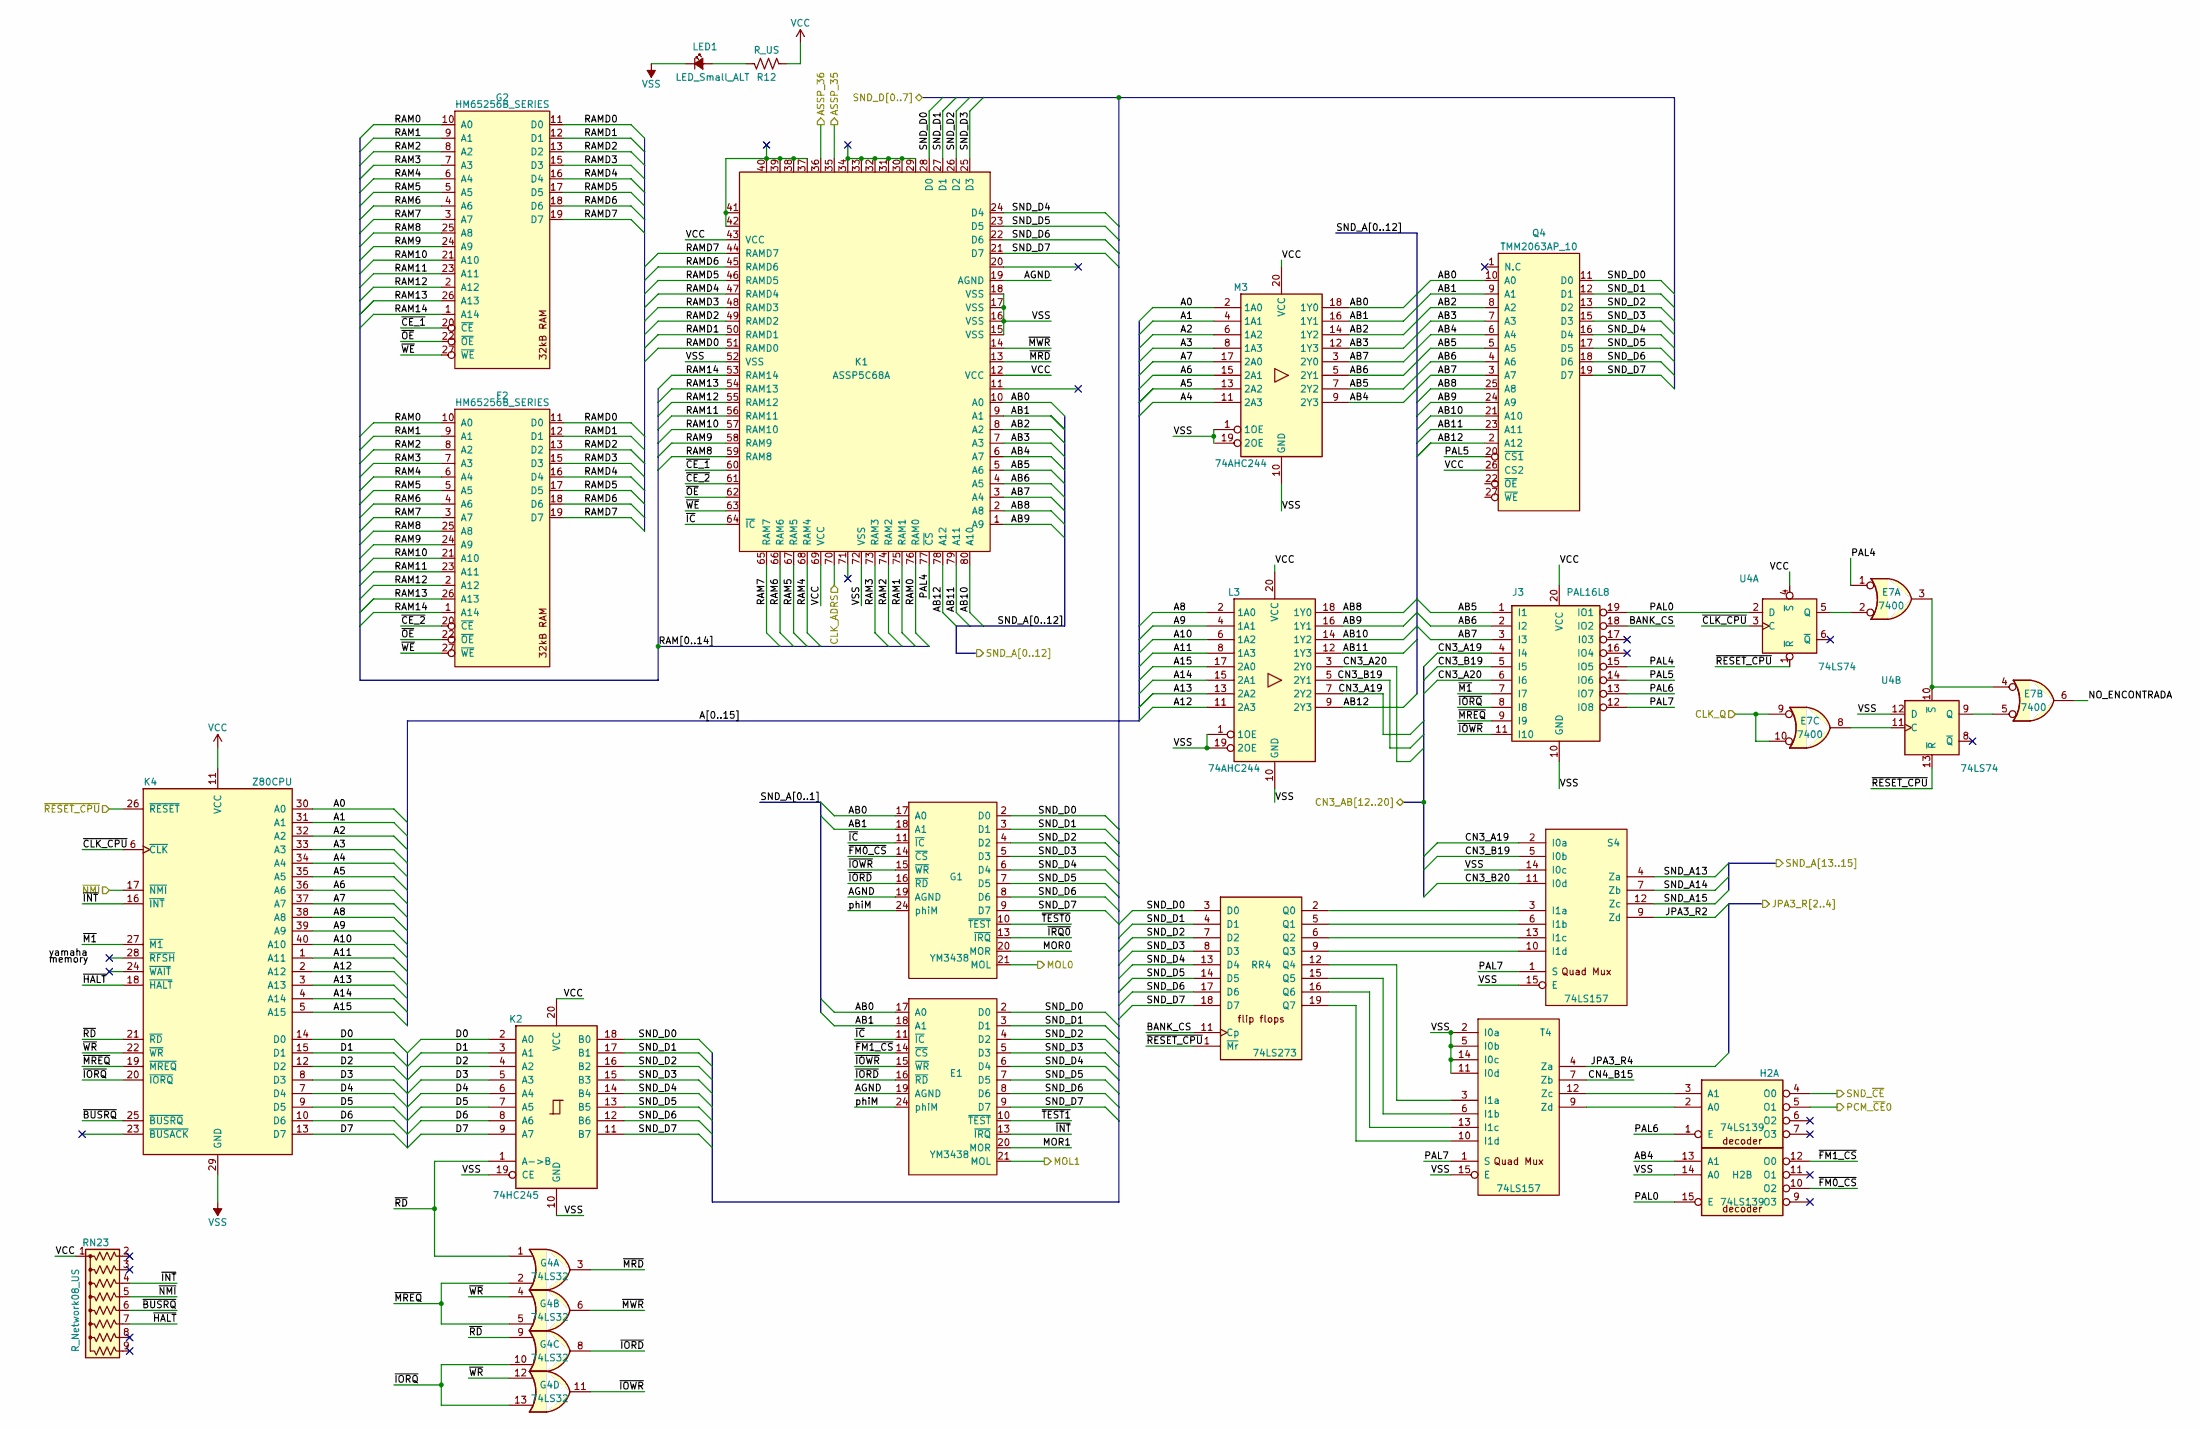
[picture p48: schematic sound_a.kicad_sch]

Parts:
E1: YM3438
E7: 7400
F2: HM65256B_SERIES
G1: YM3438
G2: HM65256B_SERIES
G4: 74LS32
H2: 74LS139
J3: PAL16L8
K1: ASSP5C68A
K2: 74HC245
K4: Z80CPU
L3: 74AHC244
LED1: LED_Small_ALT
M3: 74AHC244
Q4: TMM2063AP_10
R12: R_US
RN23: R_Network08_US; R_Array_SIP9
RR4: 74LS273
S4: 74LS157
T4: 74LS157
U4: 74LS74

Connections:
A0: K4.30 (A0), M3.2 (1A0)
A1: K4.31 (A1), M3.4 (1A1)
A2: K4.32 (A2), M3.6 (1A2)
A3: K4.33 (A3), M3.8 (1A3)
A4: K4.34 (A4), M3.11 (2A3)
A5: K4.35 (A5), M3.13 (2A2)
A6: K4.36 (A6), M3.15 (2A1)
A7: K4.37 (A7), M3.17 (2A0)
A8: K4.38 (A8), L3.2 (1A0)
A9: K4.39 (A9), L3.4 (1A1)
A10: K4.40 (A10), L3.6 (1A2)
A11: K4.1 (A11), L3.8 (1A3)
A12: K4.2 (A12), L3.11 (2A3)
A13: K4.3 (A13), L3.13 (2A2)
A14: K4.4 (A14), L3.15 (2A1)
A15: K4.5 (A15), L3.17 (2A0)
AB0: E1.17 (A0), G1.17 (A0), K1.10 (A0), M3.18 (1Y0), Q4.10 (A0)
AB1: E1.18 (A1), G1.18 (A1), K1.9 (A1), M3.16 (1Y1), Q4.9 (A1)
AB2: K1.8 (A2), M3.14 (1Y2), Q4.8 (A2)
AB3: K1.7 (A3), M3.12 (1Y3), Q4.7 (A3)
AB4: H2.13 (A1), K1.6 (A7), M3.9 (2Y3), Q4.6 (A4)
AB5: J3.1 (I1), K1.5 (A6), M3.7 (2Y2), Q4.5 (A5)
AB6: J3.2 (I2), K1.4 (A5), M3.5 (2Y1), Q4.4 (A6)
AB7: J3.3 (I3), K1.3 (A4), M3.3 (2Y0), Q4.3 (A7)
AB8: K1.2 (A8), L3.18 (1Y0), Q4.25 (A8)
AB9: K1.1 (A9), L3.16 (1Y1), Q4.24 (A9)
AB10: K1.80 (A10), L3.14 (1Y2), Q4.21 (A10)
AB11: K1.79 (A11), L3.12 (1Y3), Q4.23 (A11)
AB12: K1.78 (A12), L3.9 (2Y3), Q4.2 (A12)
AGND: E1.19 (AGND), G1.19 (AGND), K1.19 (AGND)
ASSP_35: K1.35
ASSP_36: K1.36
BANK_CS: J3.18 (IO2), RR4.11 (Cp)
CLK_ADRS: K1.70
CLK_Q: E7.9, E7.10
CN3_A19: J3.4 (I4), L3.7 (2Y2), S4.2 (I0a)
CN3_A20: J3.6 (I6), L3.3 (2Y0)
CN3_B19: J3.5 (I5), L3.5 (2Y1), S4.5 (I0b)
CN3_B20: S4.11 (I0d)
CN4_B15: T4.7 (Zb)
D0: K2.2 (A0), K4.14 (D0)
D1: K2.3 (A1), K4.15 (D1)
D2: K2.4 (A2), K4.12 (D2)
D3: K2.5 (A3), K4.8 (D3)
D4: K2.6 (A4), K4.7 (D4)
D5: K2.7 (A5), K4.9 (D5)
D6: K2.8 (A6), K4.10 (D6)
D7: K2.9 (A7), K4.13 (D7)
JPA3_R2: S4.9 (Zd)
JPA3_R4: T4.4 (Za)
MOL0: G1.21 (MOL)
MOL1: E1.21 (MOL)
MOR0: G1.20 (MOR)
MOR1: E1.20 (MOR)
NO_ENCONTRADA: E7.6
unnamed: E7.2, U4.5 (Q)
unnamed: E7.3, E7.4, U4.10 (~S)
unnamed: E7.5, U4.9 (Q)
unnamed: E7.8, U4.11 (C)
unnamed: H2.2 (A0), T4.9 (Zd)
unnamed: H2.3 (A1), T4.12 (Zc)
unnamed: K1.29, K1.30, K1.31, K1.32, K1.33, K1.34
unnamed: K1.37, K1.38, K1.39, K1.40, K1.41, K1.42
unnamed: LED1.2 (A), R12.1
unnamed: RR4.2 (Q0), S4.3 (I1a)
unnamed: RR4.5 (Q1), S4.6 (I1b)
unnamed: RR4.6 (Q2), S4.13 (I1c)
unnamed: RR4.9 (Q3), S4.10 (I1d)
unnamed: RR4.12 (Q4), T4.3 (I1a)
unnamed: RR4.15 (Q5), T4.6 (I1b)
unnamed: RR4.16 (Q6), T4.13 (I1c)
unnamed: RR4.19 (Q7), T4.10 (I1d)
PAL0: H2.15 (E), J3.19 (IO1), U4.2 (D)
PAL4: E7.1, J3.15 (IO5), K1.77 (~CS)
PAL5: J3.14 (IO6), Q4.20 (~CS1)
PAL6: H2.1 (E), J3.13 (IO7)
PAL7: J3.12 (IO8), S4.1 (S), T4.1 (S)
PCM_~CE0: H2.5 (O1)
RAM0: F2.10 (A0), G2.10 (A0), K1.76 (RAM0)
RAM1: F2.9 (A1), G2.9 (A1), K1.75 (RAM1)
RAM2: F2.8 (A2), G2.8 (A2), K1.74 (RAM2)
RAM3: F2.7 (A3), G2.7 (A3), K1.73 (RAM3)
RAM4: F2.6 (A4), G2.6 (A4), K1.68 (RAM4)
RAM5: F2.5 (A5), G2.5 (A5), K1.67 (RAM5)
RAM6: F2.4 (A6), G2.4 (A6), K1.66 (RAM6)
RAM7: F2.3 (A7), G2.3 (A7), K1.65 (RAM7)
RAM8: F2.25 (A8), G2.25 (A8), K1.59 (RAM8)
RAM9: F2.24 (A9), G2.24 (A9), K1.58 (RAM9)
RAM10: F2.21 (A10), G2.21 (A10), K1.57 (RAM10)
RAM11: F2.23 (A11), G2.23 (A11), K1.56 (RAM11)
RAM12: F2.2 (A12), G2.2 (A12), K1.55 (RAM12)
RAM13: F2.26 (A13), G2.26 (A13), K1.54 (RAM13)
RAM14: F2.1 (A14), G2.1 (A14), K1.53 (RAM14)
RAMD0: F2.11 (D0), G2.11 (D0), K1.51 (RAMD0)
RAMD1: F2.12 (D1), G2.12 (D1), K1.50 (RAMD1)
RAMD2: F2.13 (D2), G2.13 (D2), K1.49 (RAMD2)
RAMD3: F2.15 (D3), G2.15 (D3), K1.48 (RAMD3)
RAMD4: F2.16 (D4), G2.16 (D4), K1.47 (RAMD4)
RAMD5: F2.17 (D5), G2.17 (D5), K1.46 (RAMD5)
RAMD6: F2.18 (D6), G2.18 (D6), K1.45 (RAMD6)
RAMD7: F2.19 (D7), G2.19 (D7), K1.44 (RAMD7)
SND_A13: S4.4 (Za)
SND_A14: S4.7 (Zb)
SND_A15: S4.12 (Zc)
SND_D0: E1.2 (D0), G1.2 (D0), K1.28 (D0), K2.18 (B0), Q4.11 (D0), RR4.3 (D0)
SND_D1: E1.3 (D1), G1.3 (D1), K1.27 (D1), K2.17 (B1), Q4.12 (D1), RR4.4 (D1)
SND_D2: E1.4 (D2), G1.4 (D2), K1.26 (D2), K2.16 (B2), Q4.13 (D2), RR4.7 (D2)
SND_D3: E1.5 (D3), G1.5 (D3), K1.25 (D3), K2.15 (B3), Q4.15 (D3), RR4.8 (D3)
SND_D4: E1.6 (D4), G1.6 (D4), K1.24 (D4), K2.14 (B4), Q4.16 (D4), RR4.13 (D4)
SND_D5: E1.7 (D5), G1.7 (D5), K1.23 (D5), K2.13 (B5), Q4.17 (D5), RR4.14 (D5)
SND_D6: E1.8 (D6), G1.8 (D6), K1.22 (D6), K2.12 (B6), Q4.18 (D6), RR4.17 (D6)
SND_D7: E1.9 (D7), G1.9 (D7), K1.21 (D7), K2.11 (B7), Q4.19 (D7), RR4.18 (D7)
SND_~CE: H2.4 (O0)
VCC: J3.20 (VCC), K1.12 (VCC), K1.43 (VCC), K1.69 (VCC), K2.20 (VCC), L3.20 (VCC), M3.20 (VCC), Q4.26 (CS2), RN23.1 (common), U4.4 (~S)
VSS: H2.14 (A0), J3.10 (GND), K1.15 (VSS), K1.16 (VSS), K1.17 (VSS), K1.18 (VSS), K1.52 (VSS), K1.72 (VSS), K2.10 (GND), K2.19 (CE), L3.1 (1OE), L3.10 (GND), L3.19 (2OE), M3.1 (1OE), M3.10 (GND), M3.19 (2OE), S4.14 (I0c), S4.15 (E), T4.2 (I0a), T4.5 (I0b), T4.11 (I0d), T4.14 (I0c), T4.15 (E), U4.12 (D)
phiM: E1.24 (phiM), G1.24 (phiM)
~BUSRQ: K4.25 (~BUSRQ), RN23.6 (R5)
~CE_1: G2.20 (~CE), K1.60
~CE_2: F2.20 (~CE), K1.61
~CLK_CPU: K4.6 (~CLK), U4.3 (C)
~FM0_CS: G1.14 (~CS), H2.10 (O2)
~FM1_CS: E1.14 (~CS), H2.12 (O0)
~HALT: K4.18 (~HALT), RN23.7 (R6)
~IC: E1.11 (~IC), G1.11 (~IC), K1.64 (~IC)
~INT: E1.13 (~IRQ), K4.16 (~INT), RN23.4 (R3)
~IORD: E1.16 (~RD), G1.16 (~RD), G4.8
~IORQ: G4.10, G4.13, J3.8 (I8), K4.20 (~IORQ)
~IOWR: E1.15 (~WR), G1.15 (~WR), G4.11, J3.11 (I10)
~IRQ0: G1.13 (~IRQ)
~M1: J3.7 (I7), K4.27 (~M1)
~MRD: G4.3, K1.13
~MREQ: G4.2, G4.5, J3.9 (I9), K4.19 (~MREQ)
~MWR: G4.6, K1.14
~NMI: K4.17 (~NMI), RN23.5 (R4)
~OE: F2.22 (~OE), G2.22 (~OE), K1.62
~RD: G4.1, G4.9, K2.1 (A->B), K4.21 (~RD)
~RESET_CPU: K4.26 (~RESET), RR4.1 (~Mr), U4.1 (~R), U4.13 (~R)
~TEST0: G1.10 (~TEST)
~TEST1: E1.10 (~TEST)
~WE: F2.27 (~WE), G2.27 (~WE), K1.63
~WR: G4.4, G4.12, K4.22 (~WR)
