jotego/jts16/cores/s16b/ver/game/mist_dump.v

`timescale 1ns/1ps

module mist_dump(
    input           VGA_VS,
    input           led,
    input   [31:0]  frame_cnt
);

`ifdef DUMP
`ifndef NCVERILOG // iVerilog:
    initial begin
        // #(200*100*1000*1000);
        $display("DUMP enabled");
        $dumpfile("test.lxt");
    end
    `ifdef LOADROM
    always @(negedge led) if( $time > 20000 ) begin // led = downloading signal
        $display("DUMP starts");
        $dumpvars(0,mist_test);
        $dumpon;
    end
    `else
        `ifdef DUMP_START
        always @(negedge VGA_VS) if( frame_cnt==`DUMP_START ) begin
        `else
            initial begin
        `endif
            $display("DUMP starts");
            `ifdef DEEPDUMP
                $dumpvars(0,mist_test);
            `else
                $dumpvars(1,mist_test.UUT.u_game.u_main);
                $dumpvars(1,mist_test.frame_cnt);
            `endif
            $dumpon;
        end
    `endif
`else // NCVERILOG
    `ifdef DUMP_START
    always @(negedge VGA_VS) if( frame_cnt==`DUMP_START ) begin
    `else
    initial begin
    `endif
        $shm_open("test.shm");
        `ifdef DEEPDUMP
            $display("NC Verilog: will dump all signals");
            $shm_probe(mist_test,"AS");
        `else
            $display("NC Verilog: will dump selected signals");
            $shm_probe(frame_cnt);
            //$shm_probe(UUT.u_game,"A");
            //$shm_probe(UUT.u_game.u_sdram,"A");
            `ifndef NOSOUND
                $shm_probe(UUT.u_game.u_sound,"A");
                $shm_probe(UUT.u_game.u_sound.u_pcm,"AS");
            `else
                //$shm_probe(UUT.u_game.u_video,"AS");
                //$shm_probe(UUT.u_game.u_video.u_colmix,"A");
            `endif
            //$shm_probe(UUT.u_game,"A");
            `ifdef DUMPMAIN
                $shm_probe(UUT.u_game.u_main,"AS");
                //$shm_probe(UUT.u_game.u_main.u_cabinet,"A");
                //$shm_probe(UUT.u_game.u_main.u_mapper,"A");
                //$shm_probe(UUT.u_game.u_main.u_cpu,"A");
                //$shm_probe(UUT.u_game.u_main.u_timer1,"A");
                //$shm_probe(UUT.u_game.u_main.u_timer2,"A");
                //$shm_probe(UUT.u_game.u_main.u_mul,"A");
                `ifdef FD1094
                    //$shm_probe(UUT.u_game.u_main.u_dec,"AS");
                `endif
            `endif
            `ifdef LOADROM
                $shm_probe(UUT.u_game.u_sdram.u_dwnld,"A");
            `endif
        `endif
    end
`endif
`endif

endmodule // mist_dump
